iic-jku/SG13G2_ATBS-ADC/FPGA-Design/tbs_core/vivado/tbs_core_ethernet_board/tbs_core_ethernet_board.runs/synth_1/.vivado.begin.rst

<?xml version="1.0"?>
<ProcessHandle Version="1" Minor="0">
    <Process Command="vivado.bat" Owner="si150" Host="SIMIBOOK" Pid="4056" HostCore="16" HostMemory="016458313728">
    </Process>
</ProcessHandle>
