iic-jku/SG13G2_ATBS-ADC/FPGA-Design/tbs_core/vivado/tbs_core_pwm_board/tbs_core_pwm_board.runs/impl_1/.vivado.begin.rst

<?xml version="1.0"?>
<ProcessHandle Version="1" Minor="0">
    <Process Command="vivado.bat" Owner="si150" Host="SIMIBOOK" Pid="18940" HostCore="16" HostMemory="016458313728">
    </Process>
</ProcessHandle>
<?xml version="1.0"?>
<ProcessHandle Version="1" Minor="0">
    <Process Command="vivado.bat" Owner="si150" Host="SIMIBOOK" Pid="1672" HostCore="16" HostMemory="016458313728">
    </Process>
</ProcessHandle>
