iic-jku/SG13G2_ATBS-ADC/FPGA-Design/tbs_core/documentation/TBS/TBS_RTL.pdf

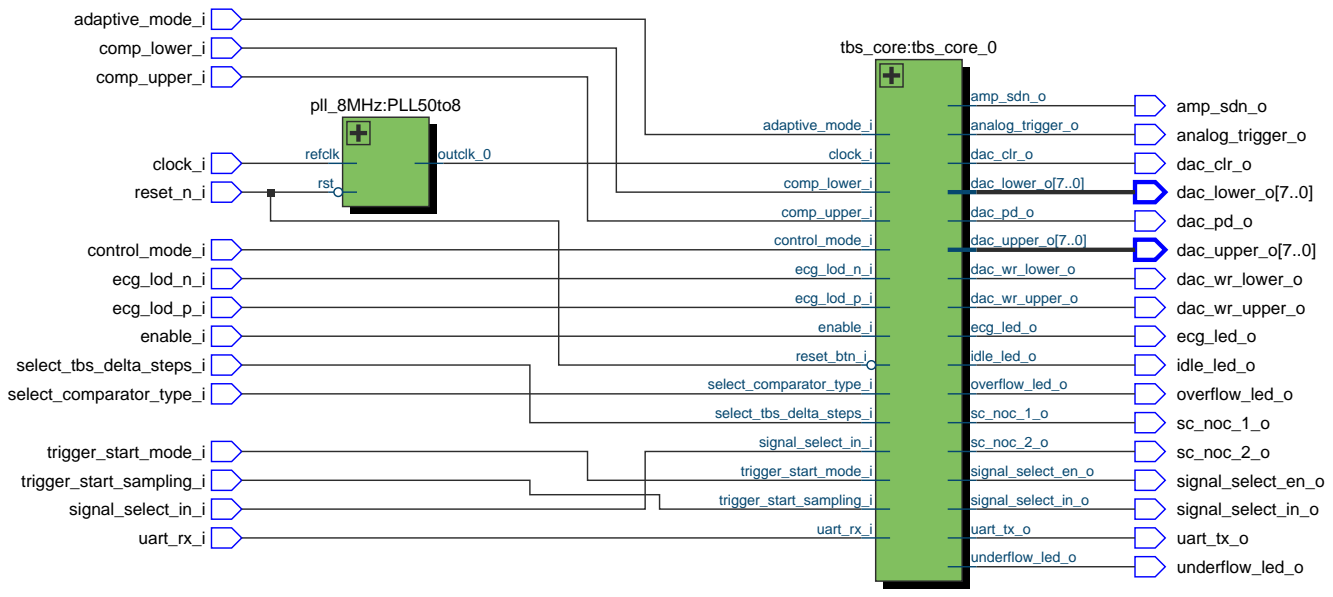
[picture p30: figure]
comp_upper_i; amp_sdn_o; comp_lower_i; analog_trigger_o; adaptive_mode_i; dac_clr_o; tbs_core:tbs_core_0; clock_i; control_mode_i; ecg_lod_n_i; ecg_lod_p_i; enable_i; reset_btn_i; select_comparator_type_i; select_tbs_delta_steps_i; signal_select_in_i; trigger_start_mode_i; trigger_start_sampling_i; uart_rx_i; dac_pd_o; dac_wr_lower_o; dac_wr_upper_o; ecg_led_o; idle_led_o; overflow_led_o; sc_noc_1_o; sc_noc_2_o; signal_select_en_o; signal_select_in_o; uart_tx_o; underflow_led_o; dac_upper_o[7..0]; dac_lower_o[7..0]; pll_8MHz:PLL50to8; refclk; rst; outclk_0; reset_n_i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
