iic-jku/SG13G2_ATBS-ADC/FPGA-Design/tbs_core/documentation/TBS_Ethernet/TBS_Ethernet_RTL.pdf

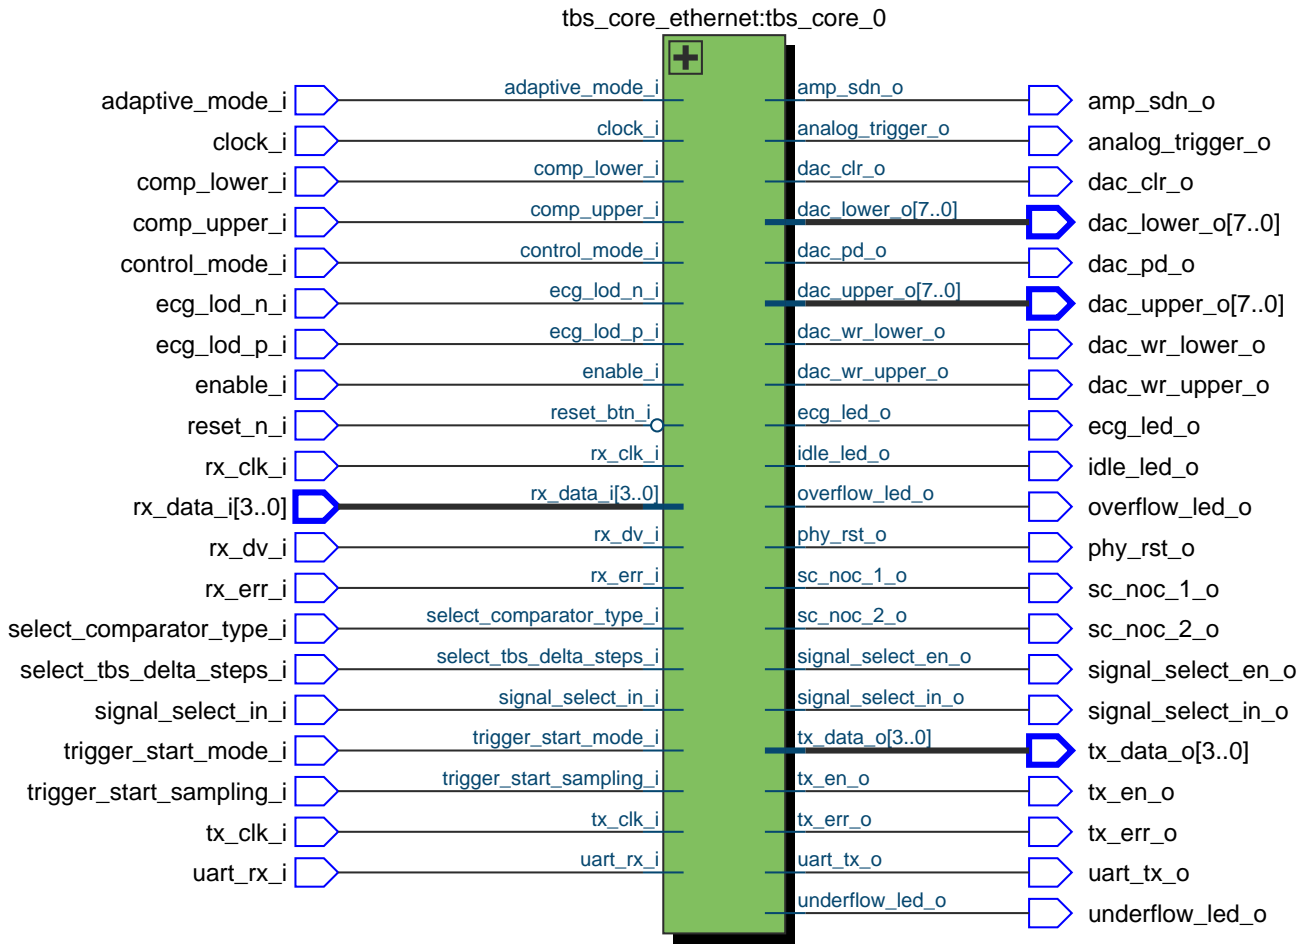
[picture p32: figure]
adaptive_mode_i; amp_sdn_o; clock_i; analog_trigger_o; comp_lower_i; dac_clr_o; comp_upper_i; dac_lower_o[7..0]; tbs_core_ethernet:tbs_core_0; control_mode_i; ecg_lod_n_i; ecg_lod_p_i; enable_i; reset_btn_i; rx_clk_i; rx_err_i; select_comparator_type_i; select_tbs_delta_steps_i; signal_select_in_i; trigger_start_mode_i; trigger_start_sampling_i; tx_clk_i; uart_rx_i; rx_data_i[3..0]; dac_pd_o; dac_wr_lower_o; dac_wr_upper_o; ecg_led_o; idle_led_o; overflow_led_o; phy_rst_o; sc_noc_1_o; sc_noc_2_o; signal_select_en_o; signal_select_in_o; tx_err_o; uart_tx_o; underflow_led_o; dac_upper_o[7..0]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
