iic-jku/SG13G2_ATBS-ADC/FPGA-Design/tbs_core/pwm_modulator/documentation/PWM-Modulator_RTL1.pdf

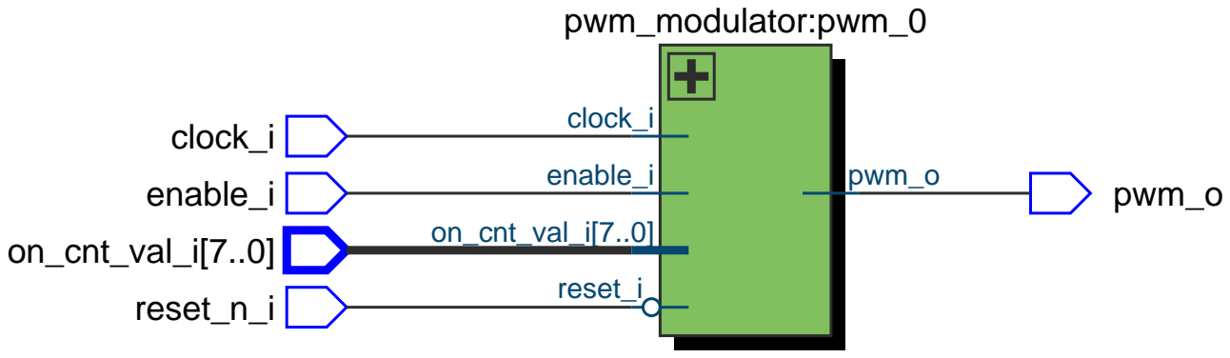
[picture p34: figure]
clock_i; pwm_modulator:pwm_0; enable_i; reset_i; on_cnt_val_i[7..0]; pwm_o enable_i; pwm_o; reset_n_i
