iic-jku/SG13G2_ATBS-ADC/FPGA-Design/tbs_core/pwm_modulator/documentation/PWM-Modulator_RTL2.pdf

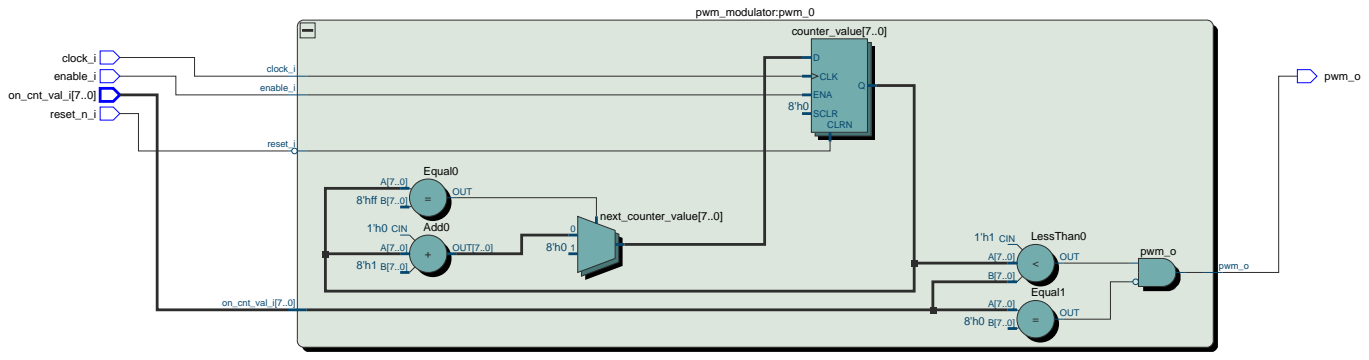
[picture p35: figure]
pwm_modulator:pwm_0; clock_i; enable_i; reset_i; on_cnt_val_i[7..0]; pwm_o; enable_i on_cnt_val_i[7..0] reset_n_i; 1'h0 CIN; Add0; OUT[7..0]; Equal0; 8'hff B[7..0]; OUT; Equal1; OUT <; 1'h1 CIN; LessThan0; counter_value[7..0] D; CLK; CLRN; ENA SCLR 8'h0; next_counter_value[7..0]
