iic-jku/SG13G2_ATBS-ADC/FPGA-Design/tbs_core/quartus/tbs_core_pwm_board/db/tbs_core_pwm_board.lpc.html

Hierarchy | Input | Constant Input | Unused Input | Floating Input | Output | Constant Output | Unused Output | Floating Output | Bidir | Constant Bidir | Unused Bidir | Input only Bidir | Output only Bidir
tbs_core_0|uart_0|uart_rx_0 | 12 | 0 | 0 | 0 | 9 | 0 | 0 | 0 | 0 | 0 | 0 | 0 | 0
tbs_core_0|uart_0|uart_tx_0 | 20 | 0 | 0 | 0 | 2 | 0 | 0 | 0 | 0 | 0 | 0 | 0 | 0
tbs_core_0|uart_0 | 21 | 0 | 0 | 0 | 11 | 0 | 0 | 0 | 0 | 0 | 0 | 0 | 0
tbs_core_0|memory2uart_0 | 24 | 0 | 0 | 0 | 9 | 0 | 0 | 0 | 0 | 0 | 0 | 0 | 0
tbs_core_0|spike_memory_0|\gen_dual_ram:dual_ram_0 | 58 | 41 | 0 | 41 | 40 | 41 | 41 | 41 | 0 | 0 | 0 | 0 | 0
tbs_core_0|spike_memory_0 | 25 | 0 | 0 | 0 | 23 | 0 | 0 | 0 | 0 | 0 | 0 | 0 | 0
tbs_core_0|spike_encoder_0 | 24 | 0 | 0 | 0 | 21 | 0 | 0 | 0 | 0 | 0 | 0 | 0 | 0
tbs_core_0|time_measurement_0 | 2 | 0 | 0 | 0 | 20 | 0 | 0 | 0 | 0 | 0 | 0 | 0 | 0
tbs_core_0|sc_noc_generator_0 | 36 | 0 | 0 | 0 | 2 | 0 | 0 | 0 | 0 | 0 | 0 | 0 | 0
tbs_core_0|analog_trigger_0 | 19 | 0 | 0 | 0 | 1 | 0 | 0 | 0 | 0 | 0 | 0 | 0 | 0
tbs_core_0|pwm_1 | 11 | 0 | 0 | 0 | 1 | 0 | 0 | 0 | 0 | 0 | 0 | 0 | 0
tbs_core_0|dac_control_1|sync_chain_0 | 3 | 0 | 0 | 0 | 1 | 0 | 0 | 0 | 0 | 0 | 0 | 0 | 0
tbs_core_0|dac_control_1 | 16 | 0 | 2 | 0 | 20 | 0 | 0 | 0 | 0 | 0 | 0 | 0 | 0
tbs_core_0|pwm_0 | 11 | 0 | 0 | 0 | 1 | 0 | 0 | 0 | 0 | 0 | 0 | 0 | 0
tbs_core_0|dac_control_0|sync_chain_0 | 3 | 0 | 0 | 0 | 1 | 0 | 0 | 0 | 0 | 0 | 0 | 0 | 0
tbs_core_0|dac_control_0 | 16 | 0 | 0 | 0 | 20 | 0 | 0 | 0 | 0 | 0 | 0 | 0 | 0
tbs_core_0|adaptive_ctrl_0|weyls_discrepancy_0|priority_encoder_1 | 5 | 1 | 2 | 1 | 3 | 1 | 1 | 1 | 0 | 0 | 0 | 0 | 0
tbs_core_0|adaptive_ctrl_0|weyls_discrepancy_0|priority_encoder_0 | 5 | 1 | 2 | 1 | 3 | 1 | 1 | 1 | 0 | 0 | 0 | 0 | 0
tbs_core_0|adaptive_ctrl_0|weyls_discrepancy_0|\gen_spike_2_tc:14:spike_2_tc | 8 | 0 | 0 | 0 | 6 | 0 | 0 | 0 | 0 | 0 | 0 | 0 | 0
tbs_core_0|adaptive_ctrl_0|weyls_discrepancy_0|\gen_spike_2_tc:13:spike_2_tc | 8 | 0 | 0 | 0 | 6 | 0 | 0 | 0 | 0 | 0 | 0 | 0 | 0
tbs_core_0|adaptive_ctrl_0|weyls_discrepancy_0|\gen_spike_2_tc:12:spike_2_tc | 8 | 0 | 0 | 0 | 6 | 0 | 0 | 0 | 0 | 0 | 0 | 0 | 0
tbs_core_0|adaptive_ctrl_0|weyls_discrepancy_0|\gen_spike_2_tc:11:spike_2_tc | 8 | 0 | 0 | 0 | 6 | 0 | 0 | 0 | 0 | 0 | 0 | 0 | 0
tbs_core_0|adaptive_ctrl_0|weyls_discrepancy_0|\gen_spike_2_tc:10:spike_2_tc | 8 | 0 | 0 | 0 | 6 | 0 | 0 | 0 | 0 | 0 | 0 | 0 | 0
tbs_core_0|adaptive_ctrl_0|weyls_discrepancy_0|\gen_spike_2_tc:9:spike_2_tc | 8 | 0 | 0 | 0 | 6 | 0 | 0 | 0 | 0 | 0 | 0 | 0 | 0
tbs_core_0|adaptive_ctrl_0|weyls_discrepancy_0|\gen_spike_2_tc:8:spike_2_tc | 8 | 0 | 0 | 0 | 6 | 0 | 0 | 0 | 0 | 0 | 0 | 0 | 0
tbs_core_0|adaptive_ctrl_0|weyls_discrepancy_0|\gen_spike_2_tc:7:spike_2_tc | 8 | 0 | 0 | 0 | 6 | 0 | 0 | 0 | 0 | 0 | 0 | 0 | 0
tbs_core_0|adaptive_ctrl_0|weyls_discrepancy_0|\gen_spike_2_tc:6:spike_2_tc | 8 | 0 | 0 | 0 | 6 | 0 | 0 | 0 | 0 | 0 | 0 | 0 | 0
tbs_core_0|adaptive_ctrl_0|weyls_discrepancy_0|\gen_spike_2_tc:5:spike_2_tc | 8 | 0 | 0 | 0 | 6 | 0 | 0 | 0 | 0 | 0 | 0 | 0 | 0
tbs_core_0|adaptive_ctrl_0|weyls_discrepancy_0|\gen_spike_2_tc:4:spike_2_tc | 8 | 0 | 0 | 0 | 6 | 0 | 0 | 0 | 0 | 0 | 0 | 0 | 0
tbs_core_0|adaptive_ctrl_0|weyls_discrepancy_0|\gen_spike_2_tc:3:spike_2_tc | 8 | 0 | 0 | 0 | 6 | 0 | 0 | 0 | 0 | 0 | 0 | 0 | 0
tbs_core_0|adaptive_ctrl_0|weyls_discrepancy_0|\gen_spike_2_tc:2:spike_2_tc | 8 | 0 | 0 | 0 | 6 | 0 | 0 | 0 | 0 | 0 | 0 | 0 | 0
tbs_core_0|adaptive_ctrl_0|weyls_discrepancy_0|\gen_spike_2_tc:1:spike_2_tc | 8 | 0 | 0 | 0 | 6 | 0 | 0 | 0 | 0 | 0 | 0 | 0 | 0
tbs_core_0|adaptive_ctrl_0|weyls_discrepancy_0|\gen_spike_2_tc:0:spike_2_tc | 8 | 6 | 0 | 6 | 6 | 6 | 6 | 6 | 0 | 0 | 0 | 0 | 0
tbs_core_0|adaptive_ctrl_0|weyls_discrepancy_0 | 33 | 0 | 0 | 0 | 4 | 0 | 0 | 0 | 0 | 0 | 0 | 0 | 0
tbs_core_0|adaptive_ctrl_0|spike_shift_reg_0 | 44 | 0 | 0 | 0 | 31 | 0 | 0 | 0 | 0 | 0 | 0 | 0 | 0
tbs_core_0|adaptive_ctrl_0 | 59 | 6 | 0 | 6 | 23 | 6 | 6 | 6 | 0 | 0 | 0 | 0 | 0
tbs_core_0|spike_detector_0 | 12 | 0 | 0 | 0 | 2 | 0 | 0 | 0 | 0 | 0 | 0 | 0 | 0
tbs_core_0|sync_chain_1 | 4 | 0 | 0 | 0 | 2 | 0 | 0 | 0 | 0 | 0 | 0 | 0 | 0
tbs_core_0|debouncer_6|sync_chain_0 | 3 | 0 | 0 | 0 | 1 | 0 | 0 | 0 | 0 | 0 | 0 | 0 | 0
tbs_core_0|debouncer_6 | 3 | 0 | 0 | 0 | 1 | 0 | 0 | 0 | 0 | 0 | 0 | 0 | 0
tbs_core_0|debouncer_5|sync_chain_0 | 3 | 0 | 0 | 0 | 1 | 0 | 0 | 0 | 0 | 0 | 0 | 0 | 0
tbs_core_0|debouncer_5 | 3 | 0 | 0 | 0 | 1 | 0 | 0 | 0 | 0 | 0 | 0 | 0 | 0
tbs_core_0|debouncer_4|sync_chain_0 | 3 | 0 | 0 | 0 | 1 | 0 | 0 | 0 | 0 | 0 | 0 | 0 | 0
tbs_core_0|debouncer_4 | 3 | 0 | 0 | 0 | 1 | 0 | 0 | 0 | 0 | 0 | 0 | 0 | 0
tbs_core_0|debouncer_3|sync_chain_0 | 3 | 0 | 0 | 0 | 1 | 0 | 0 | 0 | 0 | 0 | 0 | 0 | 0
tbs_core_0|debouncer_3 | 3 | 0 | 0 | 0 | 1 | 0 | 0 | 0 | 0 | 0 | 0 | 0 | 0
tbs_core_0|debouncer_2|sync_chain_0 | 3 | 0 | 0 | 0 | 1 | 0 | 0 | 0 | 0 | 0 | 0 | 0 | 0
tbs_core_0|debouncer_2 | 3 | 0 | 0 | 0 | 1 | 0 | 0 | 0 | 0 | 0 | 0 | 0 | 0
tbs_core_0|debouncer_1|sync_chain_0 | 3 | 0 | 0 | 0 | 1 | 0 | 0 | 0 | 0 | 0 | 0 | 0 | 0
tbs_core_0|debouncer_1 | 3 | 0 | 0 | 0 | 1 | 0 | 0 | 0 | 0 | 0 | 0 | 0 | 0
tbs_core_0|debouncer_0|sync_chain_0 | 3 | 0 | 0 | 0 | 1 | 0 | 0 | 0 | 0 | 0 | 0 | 0 | 0
tbs_core_0|debouncer_0 | 3 | 0 | 0 | 0 | 1 | 0 | 0 | 0 | 0 | 0 | 0 | 0 | 0
tbs_core_0|sync_chain_2 | 3 | 0 | 0 | 0 | 1 | 0 | 0 | 0 | 0 | 0 | 0 | 0 | 0
tbs_core_0|sync_chain_0 | 3 | 1 | 0 | 1 | 1 | 1 | 1 | 1 | 0 | 0 | 0 | 0 | 0
tbs_core_0 | 15 | 0 | 0 | 0 | 33 | 0 | 0 | 0 | 0 | 0 | 0 | 0 | 0
PLL50to8|pll_8mhz_inst | 2 | 0 | 0 | 0 | 2 | 0 | 0 | 0 | 0 | 0 | 0 | 0 | 0
PLL50to8 | 2 | 1 | 0 | 1 | 2 | 1 | 1 | 1 | 0 | 0 | 0 | 0 | 0
