iic-jku/SG13G2_ATBS-ADC/FPGA-Design/tbs_core/ethernet/documentation/Ethernet_RTL1.pdf

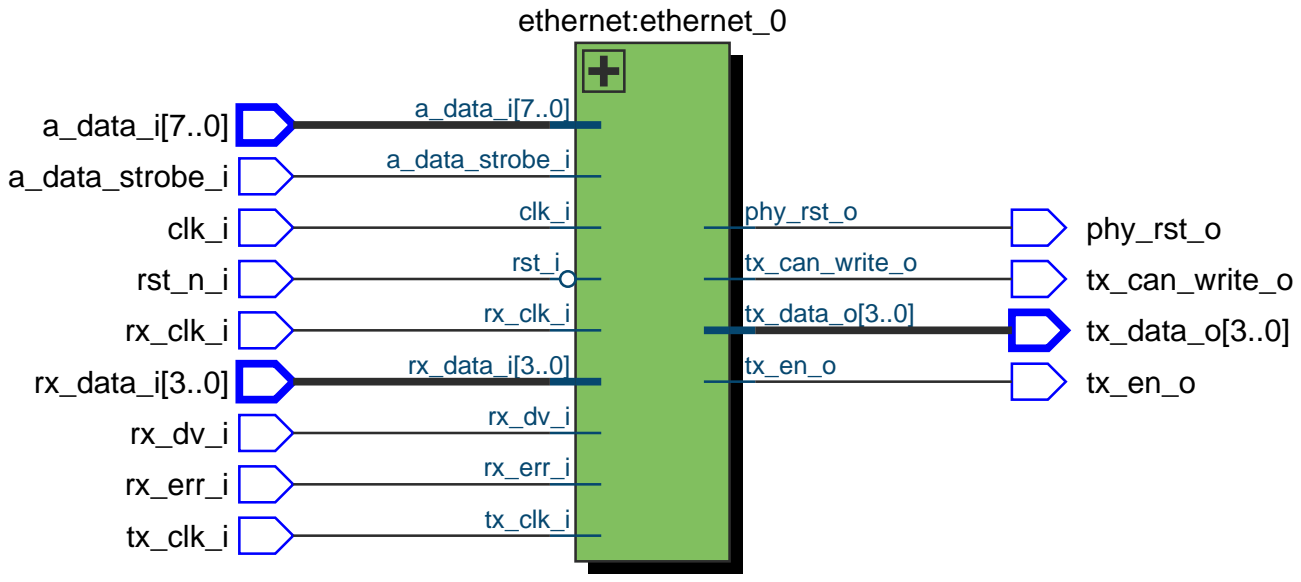
[picture p43: figure]
a_data_i[7..0] a_data_strobe_i; ethernet:ethernet_0; a_data_strobe_i; clk_i; rst_i; rx_clk_i; rx_err_i; tx_clk_i; a_data_i[7..0]; rx_data_i[3..0]; phy_rst_o; tx_can_write_o; tx_data_o[3..0]; rst_n_i; rx_clk_i rx_data_i[3..0]; rx_err_i tx_clk_i
