iic-jku/SG13G2_ATBS-ADC/FPGA-Design/tbs_core/ethernet/documentation/Ethernet_RTL2.pdf

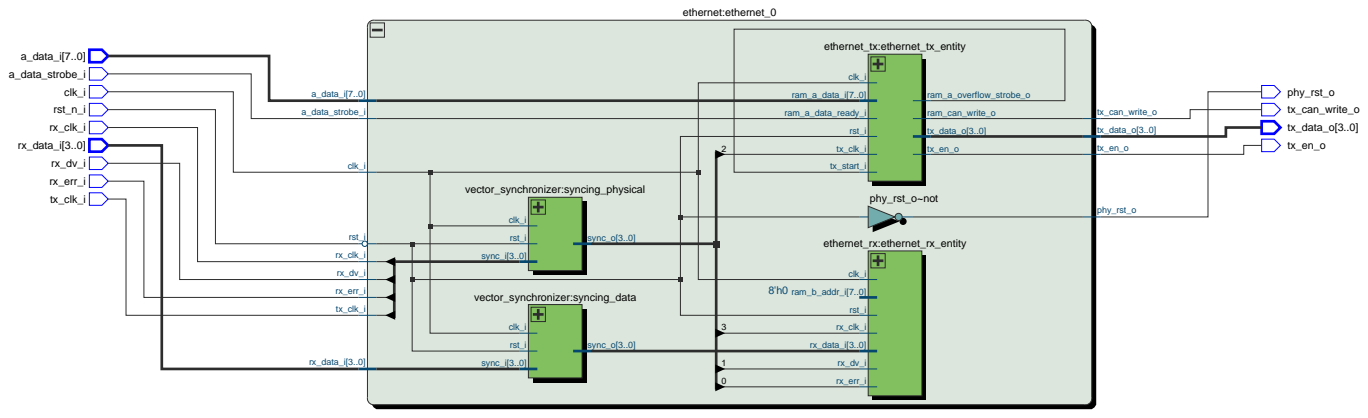
[picture p44: figure]
ethernet:ethernet_0; a_data_strobe_i; clk_i; rst_i; rx_clk_i; rx_err_i; tx_clk_i; a_data_i[7..0]; rx_data_i[3..0]; phy_rst_o; tx_can_write_o; tx_data_o[3..0]; a_data_strobe_i clk_i; ethernet_rx:ethernet_rx_entity; 8'h0 ram_b_addr_i[7..0]; ethernet_tx:ethernet_tx_entity; ram_a_data_ready_i; tx_start_i; ram_a_data_i[7..0]; ram_a_overflow_strobe_o; ram_can_write_o; phy_rst_o~not; vector_synchronizer:syncing_data; sync_i[3..0]; sync_o[3..0]; vector_synchronizer:syncing_physical; rst_n_i rx_clk_i rx_data_i[3..0] rx_dv_i rx_err_i
