iic-jku/SG13G2_ATBS-ADC/FPGA-Design/tbs_core/adaptive_threshold_control/Spike-Buffering/documentation/Spike-Buffering_RTL1.pdf

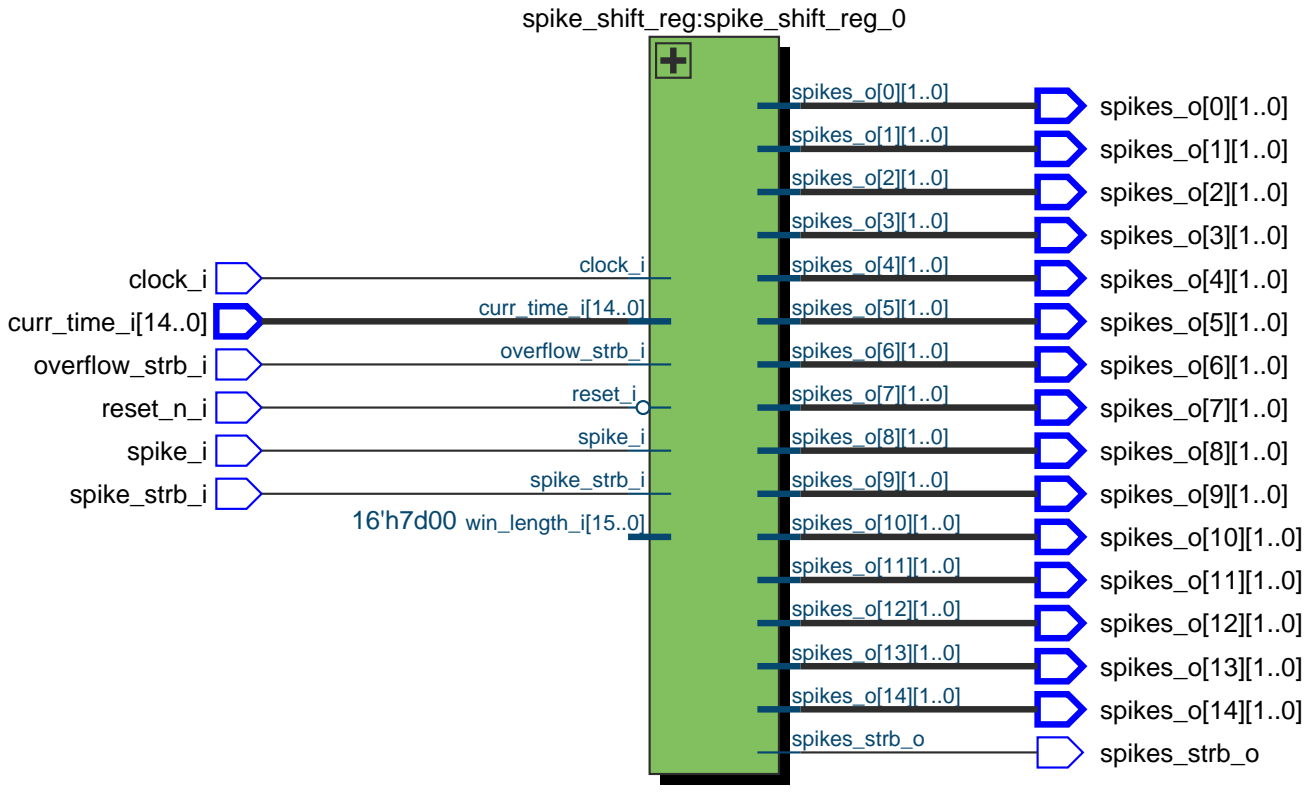
[picture p45: figure]
spikes_o[0][1..0] spikes_o[1][1..0] spikes_o[2][1..0]; spike_shift_reg:spike_shift_reg_0; clock_i; overflow_strb_i; reset_i; spike_i; spike_strb_i; curr_time_i[14..0]; 16'h7d00 win_length_i[15..0]; spikes_strb_o; spikes_o[0][1..0]; spikes_o[1][1..0]; spikes_o[2][1..0]; spikes_o[3][1..0]; spikes_o[4][1..0]; spikes_o[5][1..0]; spikes_o[6][1..0]; spikes_o[7][1..0]; spikes_o[8][1..0]; spikes_o[9][1..0]; spikes_o[10][1..0]; spikes_o[11][1..0]; spikes_o[12][1..0]; spikes_o[13][1..0]; spikes_o[14][1..0]; reset_n_i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
