iic-jku/SG13G2_ATBS-ADC/FPGA-Design/documents/s7-Mini/AP-TE0890-01/TE0890-01/Layerstack/Layerstack.JPG

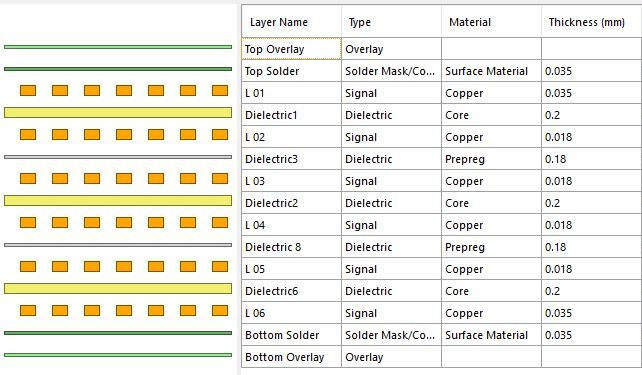
FPGA-Design/documents/s7-Mini/AP-TE0890-01/TE0890-01/Layerstack/Layerstack.JPG
