iic-jku/SG13G2_ATBS-ADC/FPGA-Design/tbs_core/documentation/Main_FSM.jpg

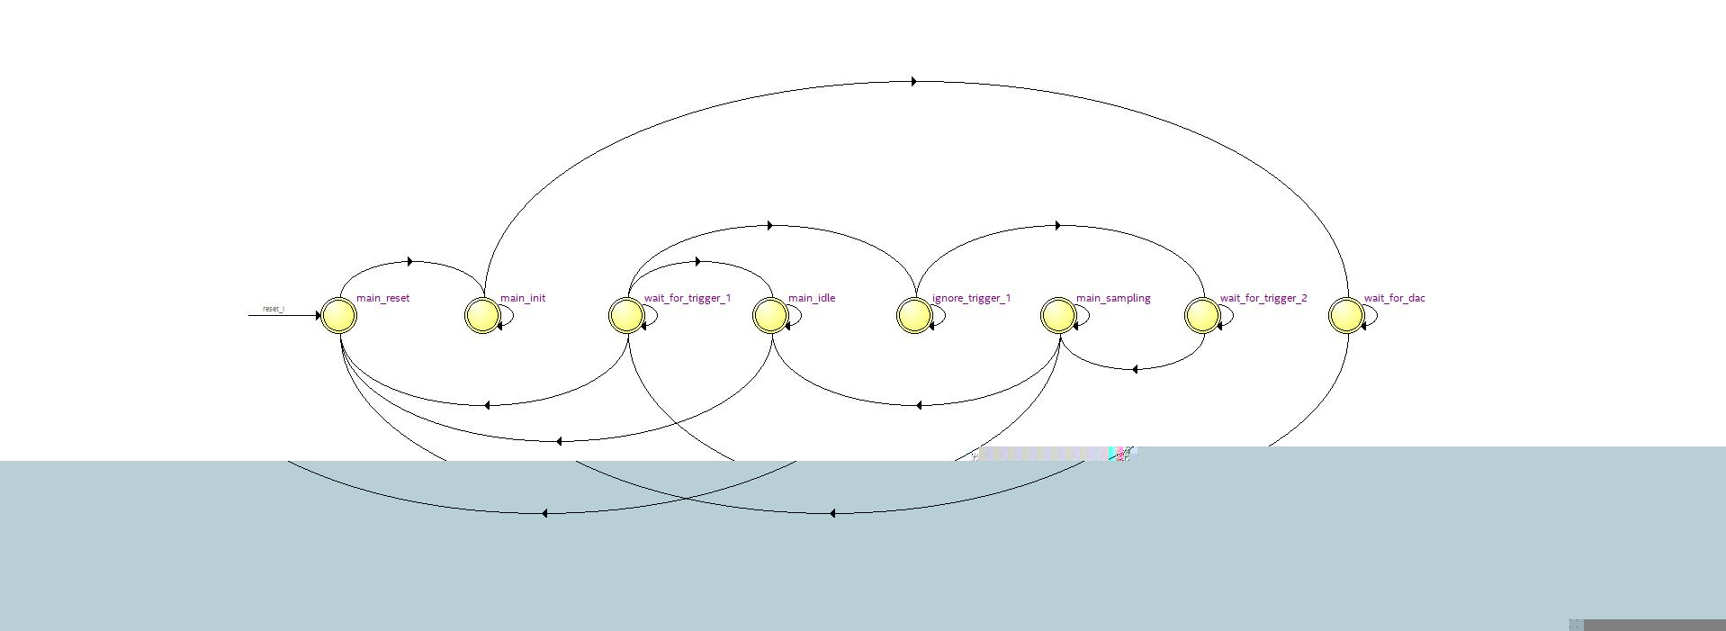
FPGA-Design/tbs_core/documentation/Main_FSM.jpg
