iic-jku/SG13G2_ATBS-ADC/PCB-Design/Ethernet_Breakout-Board/Ethernet_Breakout-Board_Pics/Ethernet_Breakout-Board_Drills_2D.png

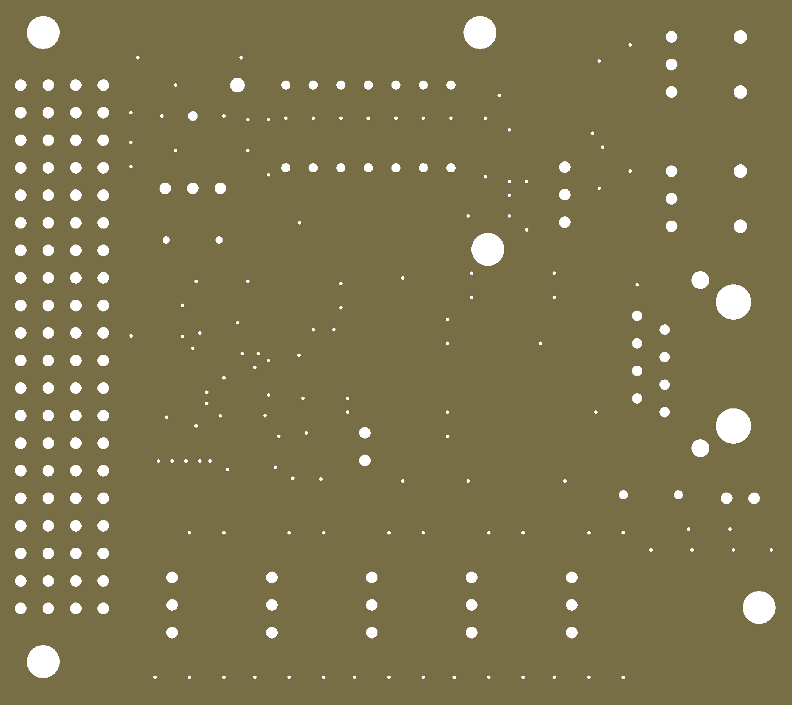
PCB-Design/Ethernet_Breakout-Board/Ethernet_Breakout-Board_Pics/Ethernet_Breakout-Board_Drills_2D.png
