iic-jku/SG13G2_ATBS-ADC/PCB-Design/Ethernet_Breakout-Board/Ethernet_Breakout-Board_Pics/Ethernet_Breakout-Board_Top_3D.png

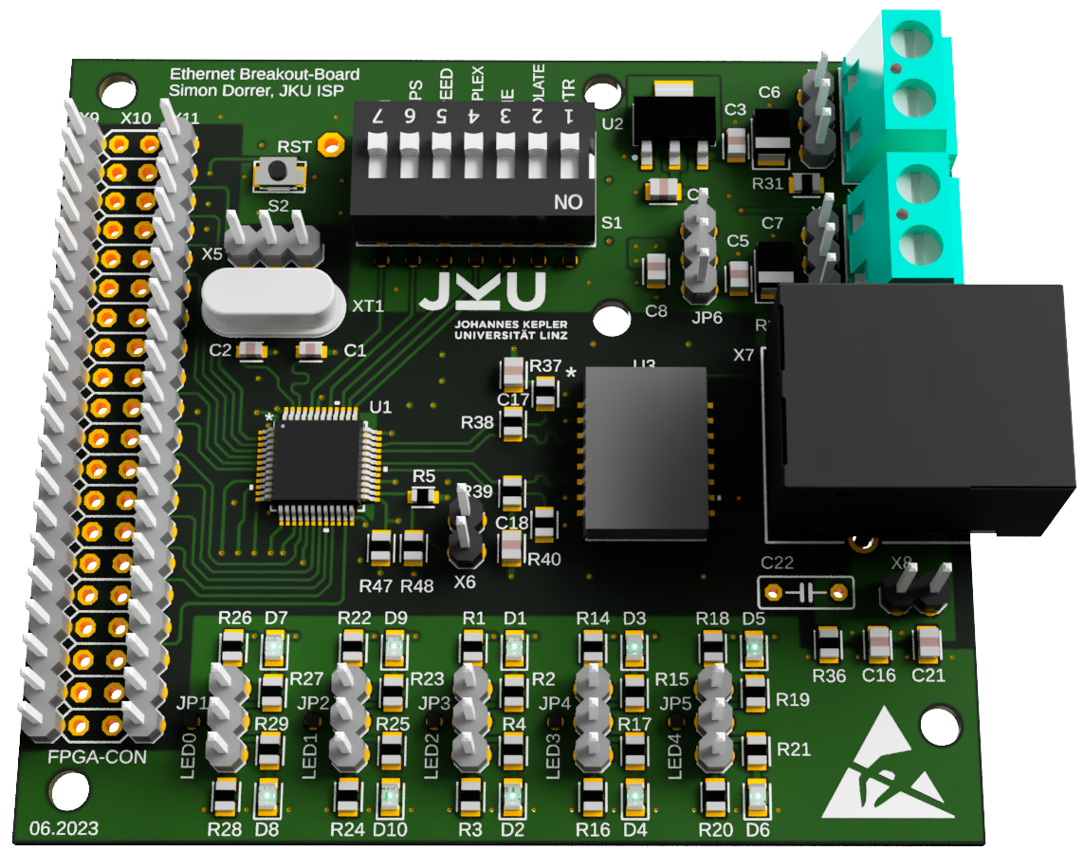
PCB-Design/Ethernet_Breakout-Board/Ethernet_Breakout-Board_Pics/Ethernet_Breakout-Board_Top_3D.png
