iic-jku/SG13G2_ATBS-ADC/PCB-Design/Ethernet_Breakout-Board/Ethernet_Breakout-Board_Stackup.png

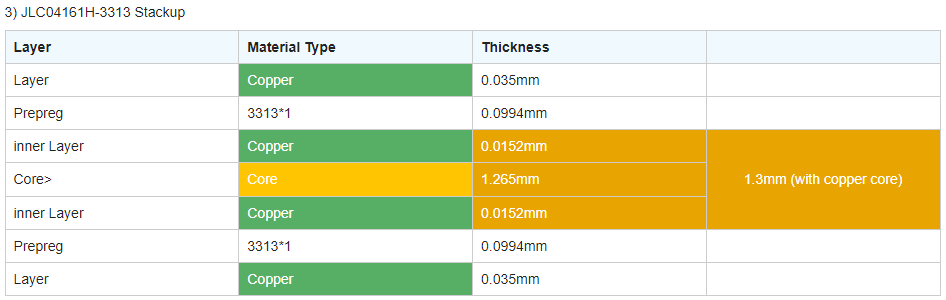
PCB-Design/Ethernet_Breakout-Board/Ethernet_Breakout-Board_Stackup.png
