iic-jku/SG13G2_ATBS-ADC/PCB-Design/Ethernet_Breakout-Board/Impedance-Calculator.png

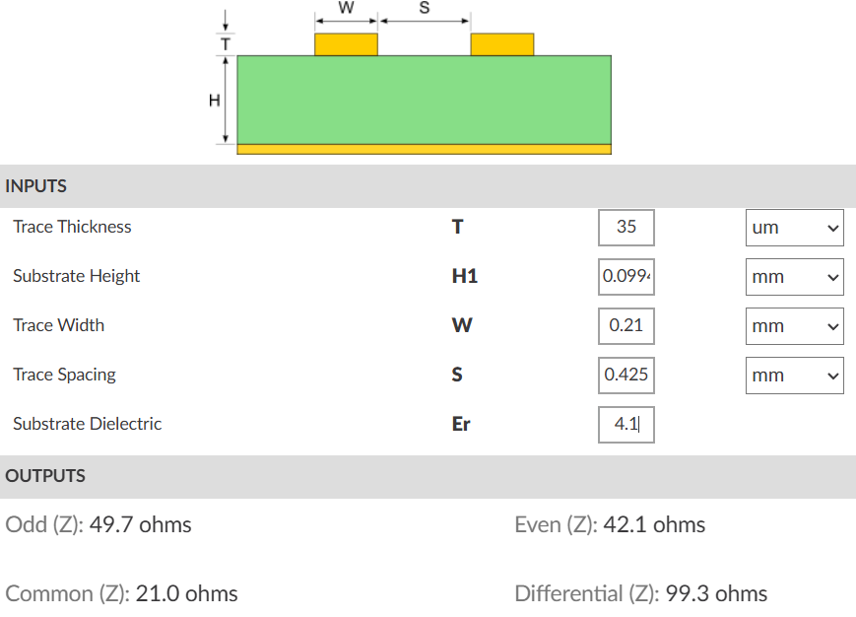
PCB-Design/Ethernet_Breakout-Board/Impedance-Calculator.png
