iic-jku/SG13G2_ATBS-ADC/PCB-Design/s7-Mini-FPGA Development Board/s7-Mini-FPGA-Development-Board_Pics/s7-Mini-FPGA Development Board_3D_Top_original.JPG

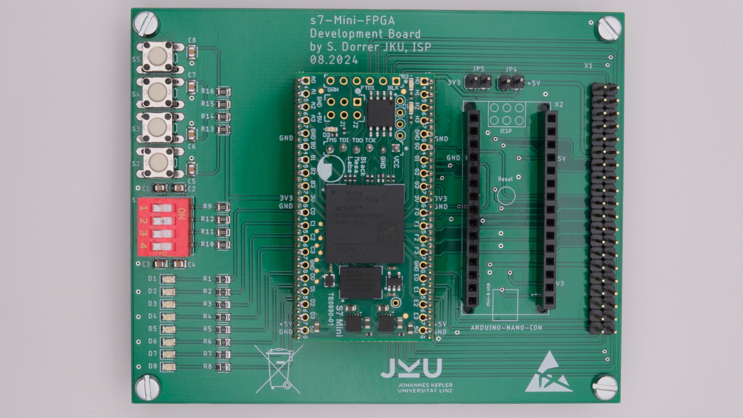
PCB-Design/s7-Mini-FPGA Development Board/s7-Mini-FPGA-Development-Board_Pics/s7-Mini-FPGA Development Board_3D_Top_original.JPG
