iic-jku/SG13G2_ATBS-ADC/PCB-Design/TBS_Analog_Front-End/TBS_Analog_Front-End_Pics/TBS_Analog_Front-End_TOP_2D.png

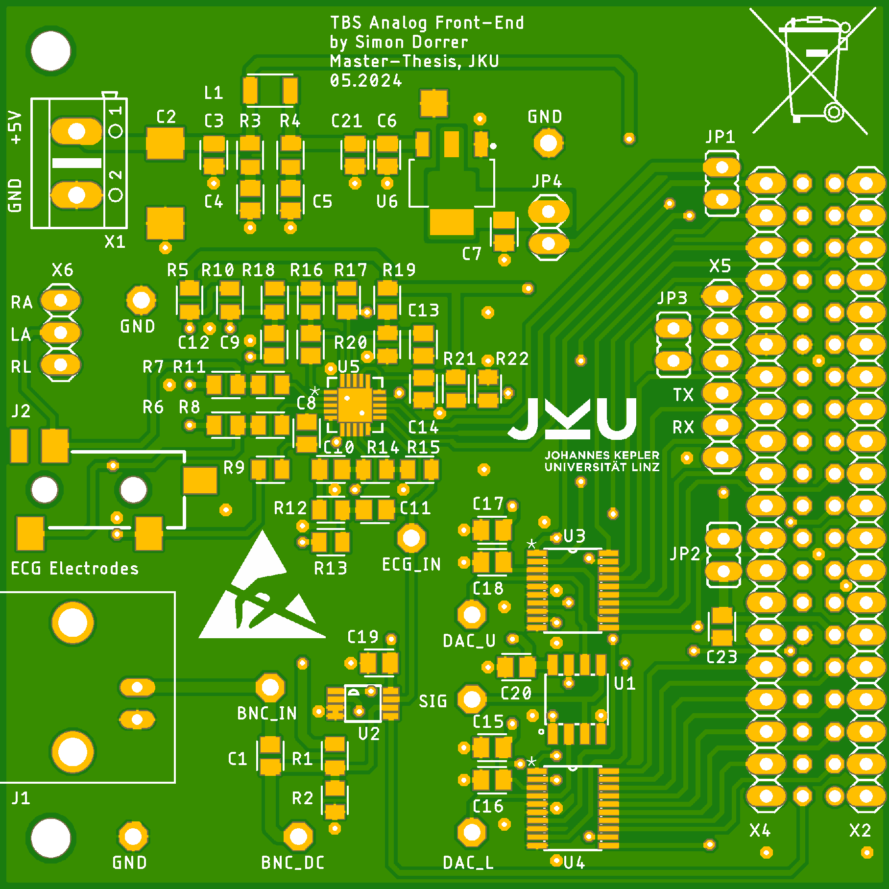
PCB-Design/TBS_Analog_Front-End/TBS_Analog_Front-End_Pics/TBS_Analog_Front-End_TOP_2D.png
