iic-jku/SG13G2_ATBS-ADC/PCB-Design/TBS_Analog_Front-End/TBS_Analog_Front-End_Assembly/TBS_Analog_Front-End_BOM.txt

Partlist exported from C:/Users/si150/AppData/Local/Temp/Neutron/ElectronFileOutput/6176/sch-4c9b82f6-f091-47ea-af62-c991dffd48f1/TBS-Analog_Front-End v54.sch at 24.10.2024 12:45

Qty Value            Device                          Package              Parts                                                   Description                                     CATEGORY  COPYRIGHT                                                CURRENT_RATING DESCRIPTION                  MANUFACTURER       MANUFACTURER_PART_NUMBER MF MFR_NAME           MPN     OC_FARNELL OC_NEWARK OPERATING_TEMP OPERATING_TEMPERATURE PART_STATUS PITCH           POPULARITY PROD_ID    RATING ROHS_COMPLIANCE ROHS_COMPLIANT SERIES  SF_ID     SPICEPREFIX SUB-CATEGORY       THERMALLOSS TOLERANCE TP_SIGNAL_NAME TYPE                                                        VOLTAGE_RATING
1                    L_CHIP-1206(3216-METRIC)        INDC3216X190         L1                                                      Inductor Fixed - Generic                        Inductor                                                                                                                                                                                                                                                                                                                                                                 Fixed                                                                                                                             
4   0R               R_CHIP-0805(2012-METRIC)        RESC2012X65          R5, R22, R25, R26                                       Resistor Fixed - Generic                        Resistor                                                                                                                                                                                                                                                                                                                                                                 Fixed                                                                                                                             
2   1.5nF            C_CHIP-0805(2012-METRIC)        CAPC2012X110         C10, C11                                                Capacitor - Generic                             Capacitor                                                                                                                                                                                                                                                                                                                                                                                                                                                                                                  
3   100k             R_CHIP-0805(2012-METRIC)        RESC2012X65          R1, R2, R14                                             Resistor Fixed - Generic                        Resistor                                                                                                                                                                                                                                                                                                                                                                 Fixed                                                                                                                             
12  100nF            C_CHIP-0805(2012-METRIC)        CAPC2012X110         C3, C6, C7, C13, C14, C16, C18, C19, C20, C22, C23, C24 Capacitor - Generic                             Capacitor                                                                                                                                                                                                                                                                                                                                                                                                                                                                                                  
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
2   AD5331BRUZ       AD5331BRUZ_FUNCAD5331BRUZ       AD5331BRUZ           U3, U4                                                                                                            Copyright (C) 2024 Ultra Librarian. All rights reserved.                                                                AD5331BRUZ                  Analog Devices Inc                                                                                                                                                                                                                                                                                                                           
1   AD8232ACPZ-RL    AD8232ACPZ-RL_FUNCAD8232ACPZ-RL AD8232ACPZ-RL        U5                                                                                                                Copyright (C) 2024 Ultra Librarian. All rights reserved.                                                                AD8232ACPZ-RL               Analog Devices Inc                                                                                                                                                                                                                                                                                                                           
1   AUDIO_JACK_3.5MM AUDIO_JACK_3.5MM_SMD            AUDIO-JACK-3.5MM-SMD J2                                                      Audio Jack                                                                                                                                                                                                                                                                                                                                CONN-10353                                                                                                                                                                                                       
4   DNP              R_CHIP-0805(2012-METRIC)        RESC2012X65          R10, R21, R23, R24                                      Resistor Fixed - Generic                        Resistor                                                                                                                                                                                                                                                                                                                                                                 Fixed                                                                                                                             
1   ECG              PINHD-1X3                       1X03                 X6                                                      PIN HEADER                                      Headers                                                                           Header, Straight, 3 Position Generic                                                           Generic                                     Generic               Active      0.100" (2.54mm)                              Generic                        Generic                       Headers, Male Pins                                      Board to Board or Cable, Unshrouded, Through Hole, Straight               
1   FPGA-CON         CON40                           CON40                X3                                                      CONNECTOR                                                                                                                                                                                                                                unknown    unknown                                                                    0                                                                                                                                                                                                                           
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
1   Meas_I           PINHD-1X2                       1X02                 JP4                                                     PIN HEADER                                      Headers                                                                           Header, Straight, 2 Position Generic                                                           Generic                                     Generic               Active      0.100" (2.54mm)                              Generic                        Generic                       Headers, Male Pins                                      Board to Board or Cable, Unshrouded, Through Hole, Straight               
1   SIGNAL           BNCPTH                          BNC                  J1                                                      BNC Right Angle Connector                                                                                                                                                                                                                                                                                                                 LPA-12729                                                PRT-10550                                                                                                                                               
9   TPPAD1-13        TPPAD1-13                       P1-13                TP1, TP2, TP3, TP4, TP5, TP6, TP7, TP8, TP9             Test pad                                                                                                                                                                                                                                                                                                                       12                                                                                                                                                                                                                          
1   TPTP20SQ         TPTP20SQ                        TP20SQ               TP10                                                    Test pad                                                                                                                                                                                                                                                                                                                       2                                                                                                                                                                                                                           
1   TSX3702IDT       TSX3702IDT                      SOIC127P600X175-8N   U1                                                                                                                                                                                                                                                                                                                                                                                                                                                                                                                                                                                                                 
1   UART             PINHD-1X6                       1X06                 X5                                                      PIN HEADER                                                                                                                                                                                                                                                                                                                     79                                                                                                                                                                                                                          
1   UART_+5V         JP1Q                            JP1                  JP3                                                     JUMPER                                                                                                                                                                                                                                                                                                                         15
