iic-jku/SG13G2_ATBS-ADC/Reconstruction/figures/testing.csv

t_recon | spikes | recon
0.03277825 | -0.25 | 1.65
0.102960875 | 0.25 | 1.753125
0.119981 | -0.25 | 1.65
0.13436775 | 0.25 | 1.753125
0.16749825 | -0.25 | 1.65
0.357068625 | 0.25 | 1.753125
0.39067525 | -0.25 | 1.65
0.394087125 | -0.25 | 1.546875
0.415457625 | 0.25 | 1.65
0.46584325 | -0.25 | 1.546875
0.494399125 | 0.25 | 1.65
0.517446625 | -0.25 | 1.546875
0.53319625 | 0.25 | 1.65
0.5355055 | 0.25 | 1.753125
0.53728 | 0.25 | 1.85625
0.538538625 | 0.25 | 1.959375
0.539564125 | 0.25 | 2.0625
0.540489375 | 0.25 | 2.165625
0.541362 | 0.25 | 2.26875
0.54218925 | 0.25 | 2.371875
0.54303525 | 0.25 | 2.475
0.5438415 | 0.25 | 2.578125
0.5446145 | 0.25 | 2.68125
0.54535475 | 0.25 | 2.784375
0.54608 | 0.25 | 2.8875
0.546811 | 0.25 | 2.990625
0.5475575 | 0.25 | 3.09375
0.548413625 | 0.25 | 3.196875
0.5639985 | -0.25 | 3.09375
0.565222125 | -0.25 | 2.990625
0.56587975 | -0.25 | 2.8875
0.56638925 | -0.25 | 2.784375
0.56683125 | -0.25 | 2.68125
0.56723425 | -0.25 | 2.578125
0.567605125 | -0.25 | 2.475
0.567976875 | -0.25 | 2.371875
0.56831 | -0.25 | 2.26875
0.568648 | -0.25 | 2.165625
0.5689835 | -0.25 | 2.0625
0.56931425 | -0.25 | 1.959375
0.569651875 | -0.25 | 1.85625
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
