iic-jku/SG13G2_ATBS-ADC/PCB-Design/ATBS_Evaluation-Board/ATBS_Evaluation-Board_Pics/ATBS_Evaluation-Board_2D_Top.png

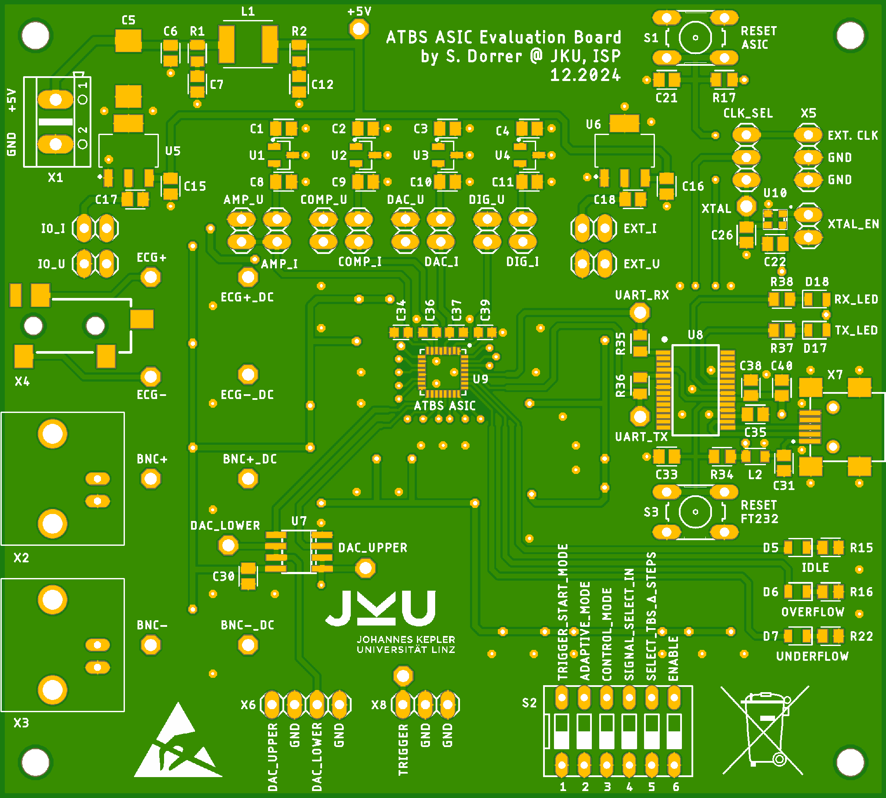
PCB-Design/ATBS_Evaluation-Board/ATBS_Evaluation-Board_Pics/ATBS_Evaluation-Board_2D_Top.png
