iic-jku/SG13G2_ATBS-ADC/PCB-Design/TBS_Analog_Front-End/TBS_Analog_Front-End_LTspice/AD8232.pdf

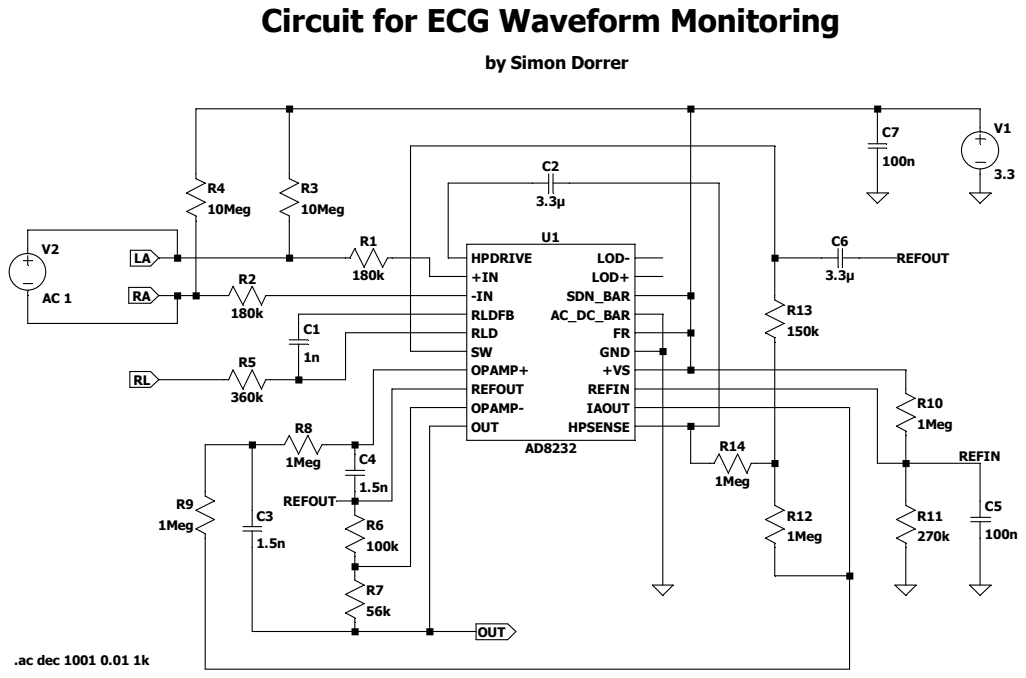
[picture p113: page 1]

Circuit for ECG Waveform Monitoring
