iic-jku/SG13G2_ATBS-ADC/SG13G2_ATBS-ADC-main/python/reconstruction/figures/ATBS_PoC_8Bit_4ms_Sine_Reconstruction.pdf

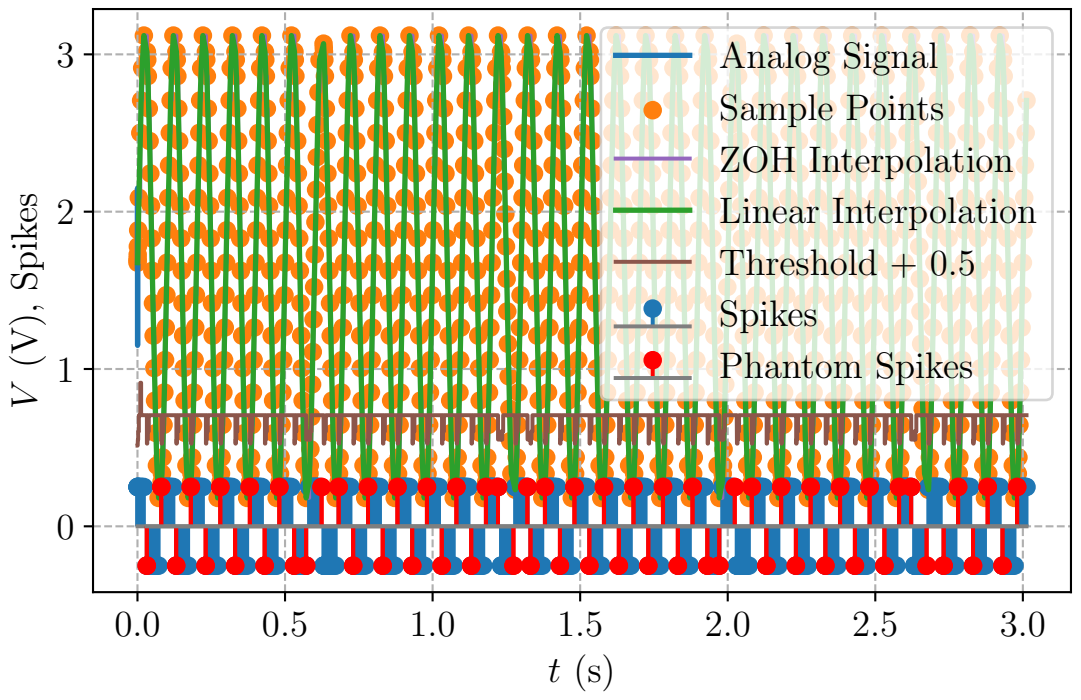
[picture p114: page 1]
V (V), Spikes; Linear Interpolation; Spikes; Phantom

Analog Signal
Sample Points ZOH Interpolation

Threshold | + 0.5
