iic-jku/SG13G2_ATBS-ADC/SG13G2_ATBS-ADC-main/python/reconstruction/figures/TBS_PoC_5Bit_virtual_ECG_Reconstruction.pdf

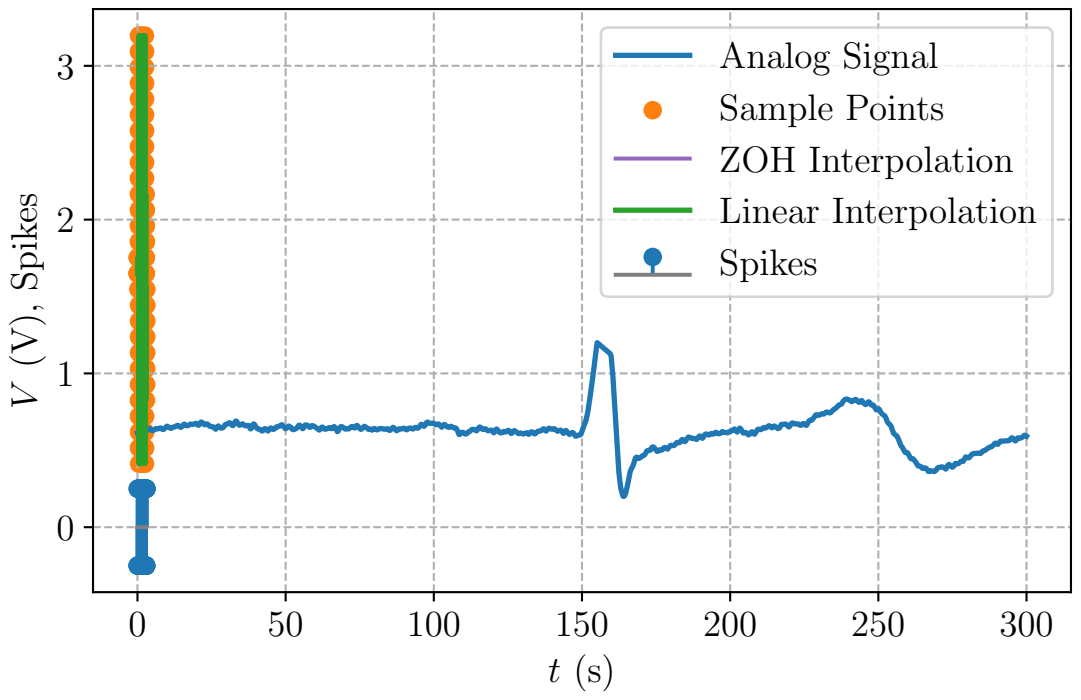
[picture p115: page 1]
V (V), Spikes; Spikes

Analog Signal
Sample Points ZOH Interpolation Linear Interpolation
