iic-jku/SG13G2_ATBS-ADC/SG13G2_ATBS-ADC-main/python/reconstruction/figures/TBS_PoC_5Bit_virtual_Sine_Reconstruction.pdf

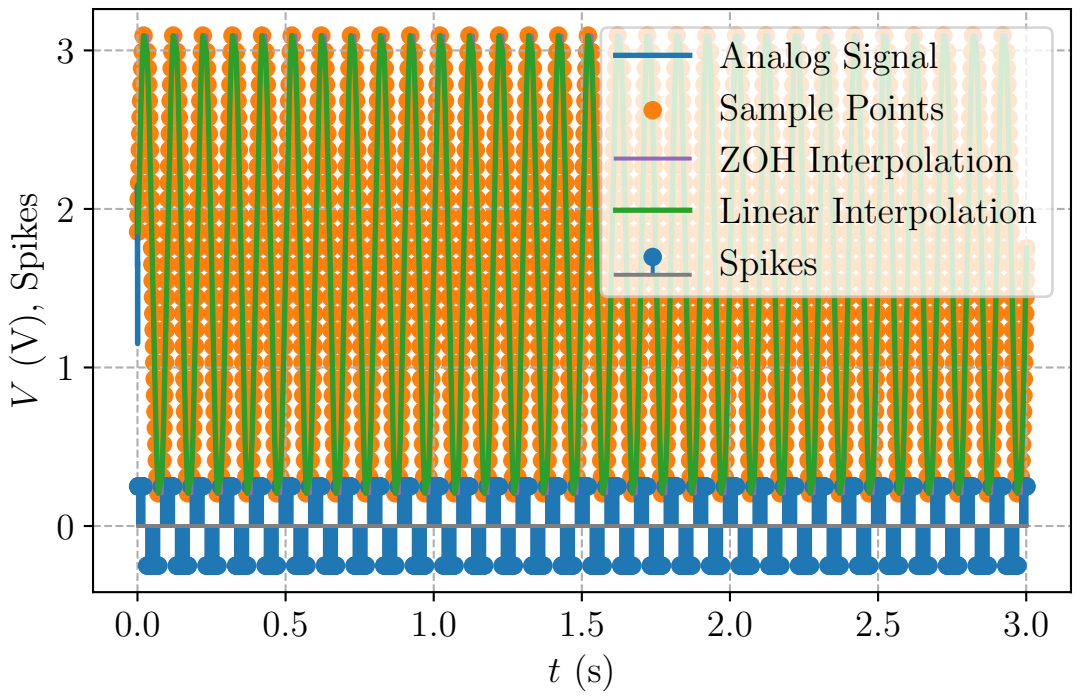
[picture p116: page 1]
V (V), Spikes; Analog Signal Sample Points ZOH Interpolation Linear Interpolation Spikes
