iic-jku/SG13G2_ATBS-ADC/SG13G2_ATBS-ADC-main/python/reconstruction/figures/TBS_Xschem_5Bit_virtual_Sine_Reconstruction_1us.pdf

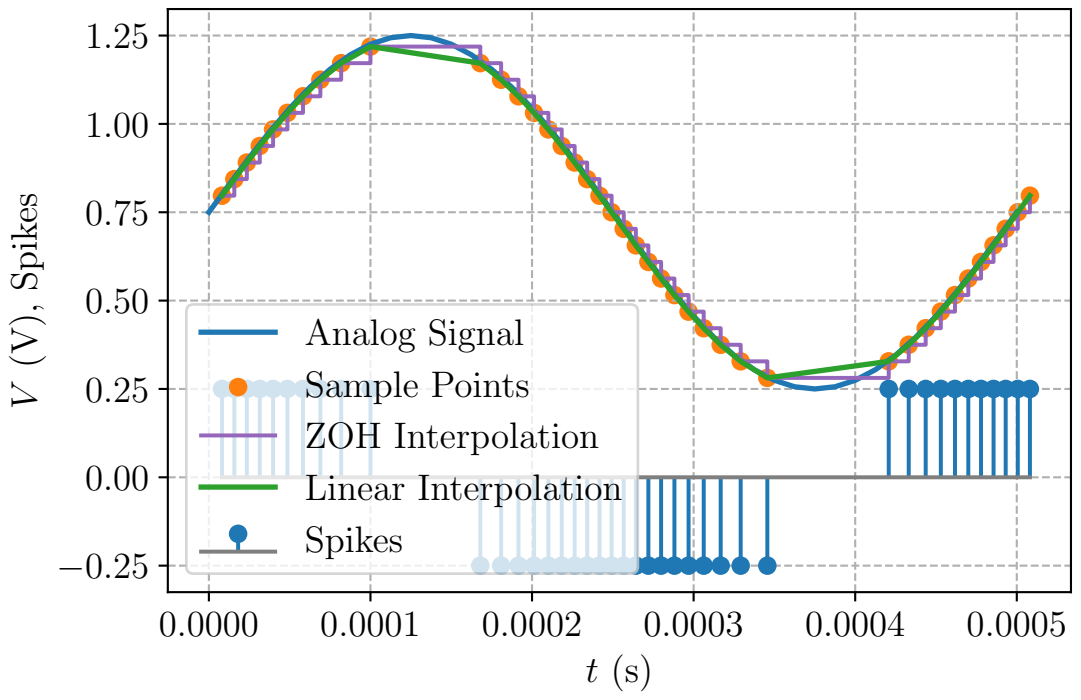
[picture p117: page 1]
V (V), Spikes; Sample Points; Spikes

Analog Signal

ZOH Interpolation
Linear Interpolation
