iic-jku/SG13G2_ATBS-ADC/FPGA-Design/tbs_core/adaptive_threshold_control/documentation/Adaptive-Threshold-Control_RTL2.pdf

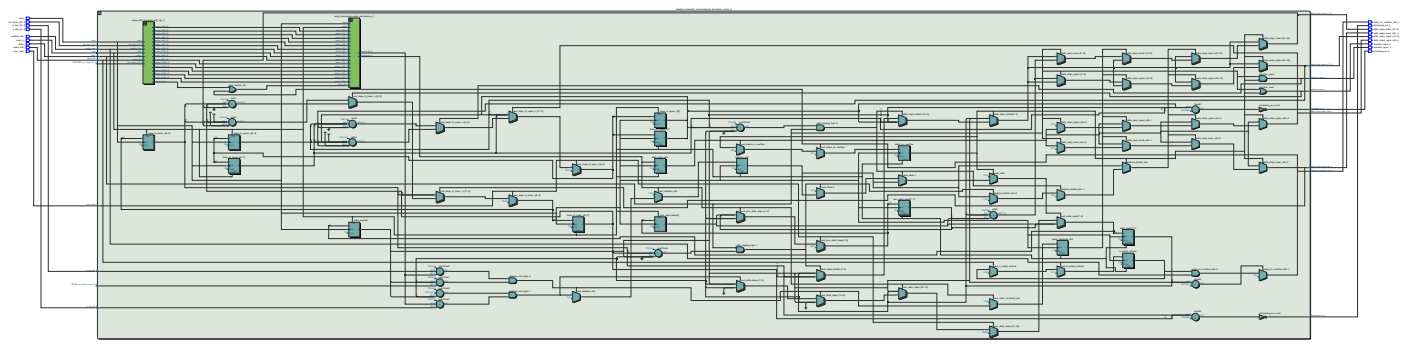
[picture p126: page 1]
adaptive_threshold_control:adaptive_threshold_control_0; clock_i overflow_strb_i reset_i spike_i spike_strb_i; sync_reset_i; curr_time_i[14..0]; d_max_i[2..0]; d_min_i[2..0]; 16'h7d00 win_length_i[15..0]; 8'h20 max_delta_steps_i[7..0]; adapt_on_overflow_strb_o; decreasing_en_o; delta_steps_lower_strb_o; delta_steps_upper_strb_o; direction_lower_o; direction_upper_o; increasing_en_o; delta_steps_upper_o[7..0]; delta_steps_lower_o[7..0]; 1'h0 CIN; Add0; OUT[7..0] +; Add1; OUT[8..0] +; Add2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

SCLR 2'h0 CLKCLRN Q | next_steps_to_upper_v[8..0] 0 9'h7d 1 | delta_steps_strb D SCLR 1'h0 CLKCLRN Q

next_steps_to_lower_v~[17..9] 01 | 1'h0 01 next_adaptive_strb | 1'h0 01 reset_delta~0

1'h0 CIN A[8..0] B[8..0] LessThan5 OUT

delta_steps_limited~[7..0] 01 | next_is_empty_interval 0 1'h0 1 next_is_empty_interval 0 1'h1 1
