iic-jku/SG13G2_ATBS-ADC/FPGA-Design/tbs_core/ethernet/documentation/Ethernet_RTL3.pdf

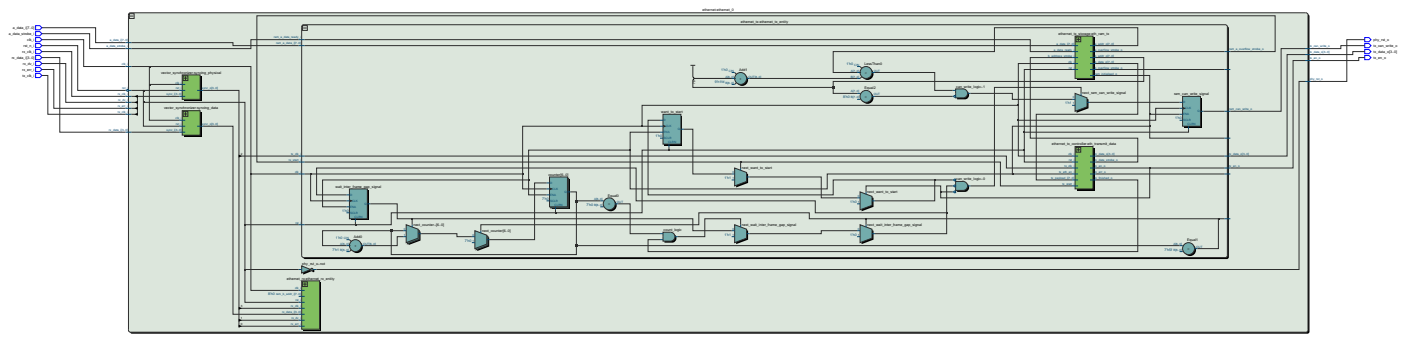
[picture p127: page 1]
ethernet:ethernet_0; a_data_strobe_i; clk_i; rst_i rx_clk_i rx_dv_i rx_err_i; tx_clk_i; a_data_i[7..0]; rx_data_i[3..0]; phy_rst_o; tx_can_write_o; tx_data_o[3..0]; ethernet_tx:ethernet_tx_entity; ram_a_data_ready_i; rst_i; tx_start_i; ram_a_data_i[7..0]; ram_a_overflow_strobe_o; ram_can_write_o; ethernet_rx:ethernet_rx_entity; rst_i rx_clk_i; rx_dv_i rx_err_i; 8'h0 ram_b_addr_i[7..0]; tx_data_o[3..0] +; 1'h0 CIN; Add0; OUT[6..0]; Add1; OUT[8..0] =Equal0; OUT; =Equal1; OUT =Equal2; OUT <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
