iic-jku/SG13G2_ATBS-ADC/FPGA-Design/tbs_core/spike_memory/documentation/Spike-Memory_RTL3.pdf

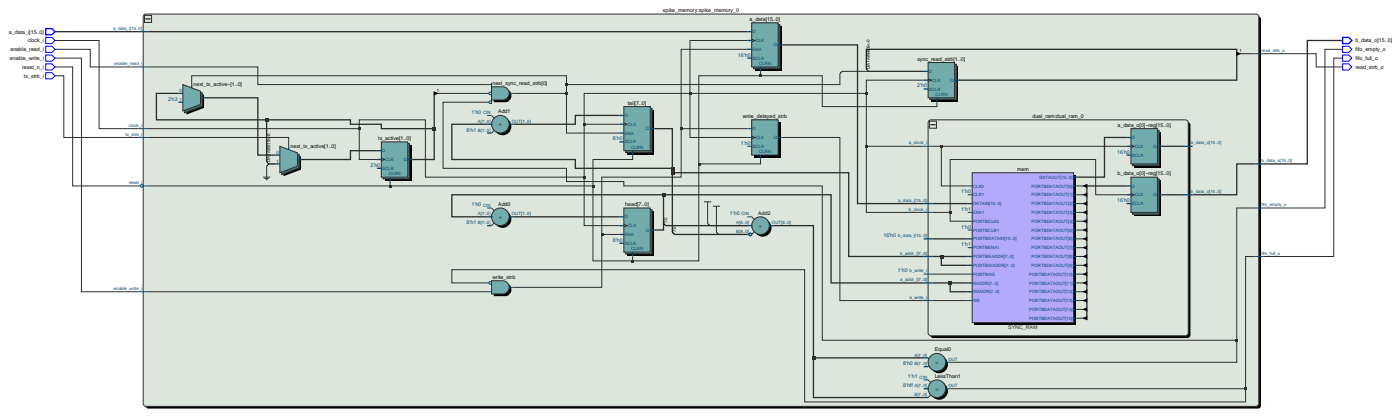
[picture p128: page 1]
spike_memory:spike_memory_0; clock_i; enable_read_i; enable_write_i; reset_i; tx_strb_i; a_data_i[15..0]; fifo_empty_o; fifo_full_o; read_strb_o; b_data_o[15..0]; a_clock_i; a_write_i; b_clock_i; 1'h0 b_write_i a_addr_i[7..0]; b_addr_i[7..0]; 16'h0 b_data_i[15..0]; a_data_o[15..0]; clock_i enable_read_i enable_write_i; fifo_empty_o fifo_full_o; reset_n_i; 1'h0 CIN; Add0; OUT[7..0] +; Add1; OUT[7..0]; Add2; OUT[8..0]; Equal0; OUT <; 1'h1 CIN; LessThan1; 8'hff A[7..0] B[7..0]; OUT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

dual_ram:dual_ram_0
PORTBDATAOUT[0] PORTBDATAOUT[1] PORTBDATAOUT[2] PORTBDATAOUT[3] PORTBDATAOUT[4] PORTBDATAOUT[5] PORTBDATAOUT[6] PORTBDATAOUT[7] PORTBDATAOUT[8] PORTBDATAOUT[9] PORTBDATAOUT[10] PORTBDATAOUT[11] PORTBDATAOUT[12] PORTBDATAOUT[13] PORTBDATAOUT[14] PORTBDATAOUT[15]
