iic-jku/SG13G2_ATBS-ADC/SG13G2_ATBS-ADC-main/sizing/techsweep/techsweep_sg13g2_lv_pmos_plots_overview/techsweep_sg13g2_lv_pmos_plots_overview.pdf

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

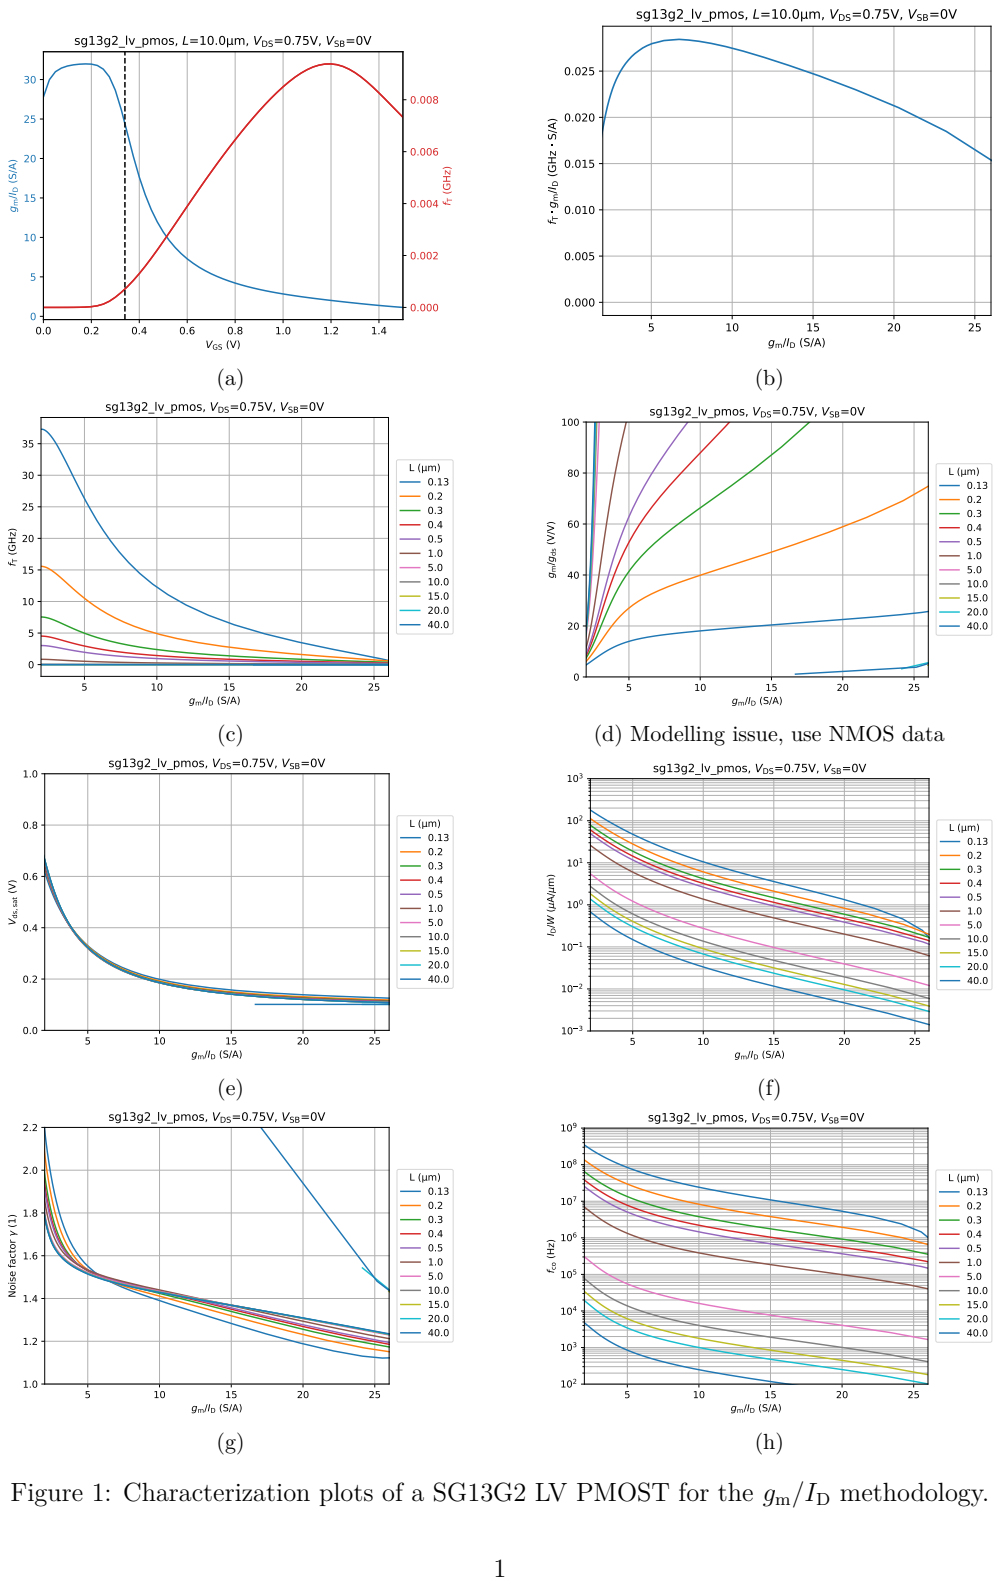
[picture p132: page 1]
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
