iic-jku/SG13G2_ATBS-ADC/SG13G2_ATBS-ADC-main/sizing/techsweep/techsweep_sg13g2_hv_nmos_plots_overview/plots/gamma_gmID.pdf

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

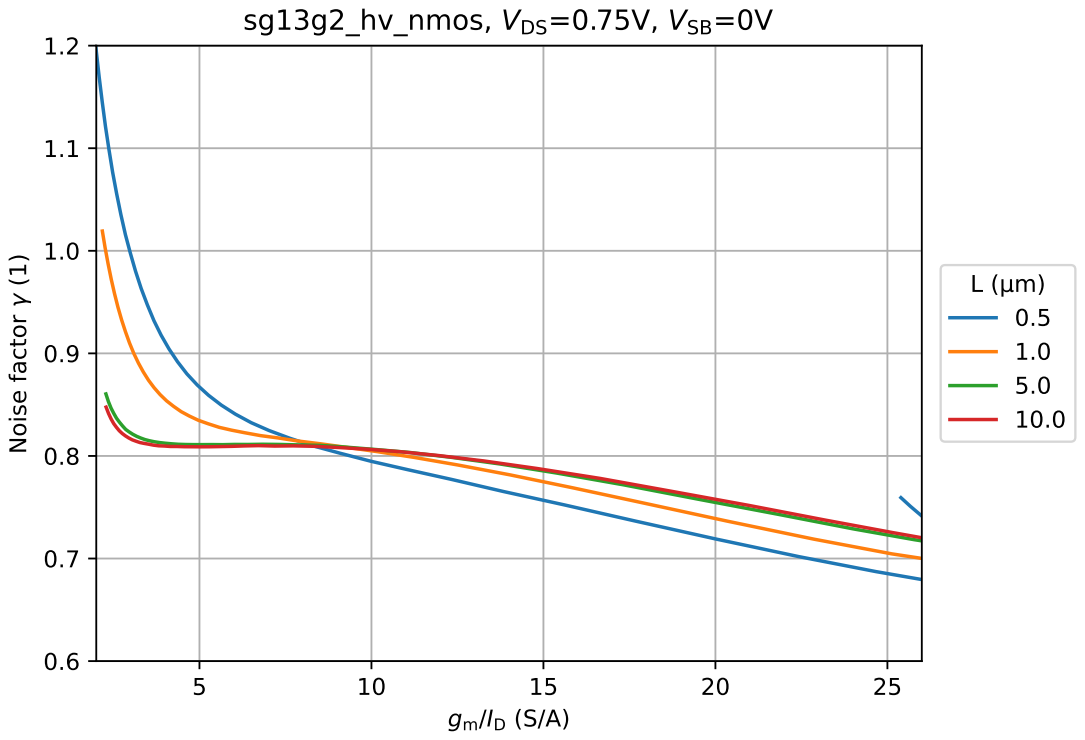
[picture p135: page 1]
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
