iic-jku/SG13G2_ATBS-ADC/PCB-Design/TBS_Analog_Front-End/TBS_Analog_Front-End_LTspice/AD8232.asc

C8: cap; 1n
C9: cap; 3.3µ
C10: cap; 1.5n
C11: cap; 1.5n
C12: cap; 3.3µ
C13: cap; 100n
C14: cap; 100n
R6: res; 10Meg
R7: res; 10Meg
R8: res; 180k
R9: res; 360k
R11: res; 180k
R12: res; 1Meg
R13: res; 1Meg
R14: res; 100k
R15: res; 56k
R16: res; 1Meg
R17: res; 1Meg
R18: res; 150k
R19: res; 1Meg
R20: res; 270k
U1: AD8232
V1: voltage; 3.3
V2: voltage; ""; AC 1
Named nets: LA, RA, RL, OUT, 0, REFOUT, REFIN
Circuit for ECG Waveform Monitoring
by Simon Dorrer
.ac dec 1001 0.01 1k
;.noise OUT V2 dec 1001 0.01 1000
