iic-jku/SG13G2_ATBS-ADC/SG13G2_ATBS-ADC-main/verilog/atbs_core_fixed_window/quartus/db/atbs_core_fixed_window_board.smp_dump.txt

State Machine - |atbs_core_fixed_window_board|atbs_core_fixed_window_8000000_20_800000_4_10_2_2_255_0_2_2_3_8_19_524288_80_8_8_160_11_2048_2_20_9_417_8:atbs_core_0|n1121_q
Name n1121_q.111 n1121_q.110 n1121_q.101 n1121_q.100 n1121_q.011 n1121_q.010 n1121_q.000 n1121_q.001 
n1121_q.001 0 0 0 0 0 0 0 0 
n1121_q.000 0 0 0 0 0 0 1 1 
n1121_q.010 0 0 0 0 0 1 0 1 
n1121_q.011 0 0 0 0 1 0 0 1 
n1121_q.100 0 0 0 1 0 0 0 1 
n1121_q.101 0 0 1 0 0 0 0 1 
n1121_q.110 0 1 0 0 0 0 0 1 
n1121_q.111 1 0 0 0 0 0 0 1 

State Machine - |atbs_core_fixed_window_board|atbs_core_fixed_window_8000000_20_800000_4_10_2_2_255_0_2_2_3_8_19_524288_80_8_8_160_11_2048_2_20_9_417_8:atbs_core_0|uart_9_8:uart_0|uart_rx_9_8:uart_rx_0|n2922_q
Name n2922_q.11 n2922_q.10 n2922_q.01 n2922_q.00 
n2922_q.00 0 0 0 0 
n2922_q.01 0 0 1 1 
n2922_q.10 0 1 0 1 
n2922_q.11 1 0 0 1 

State Machine - |atbs_core_fixed_window_board|atbs_core_fixed_window_8000000_20_800000_4_10_2_2_255_0_2_2_3_8_19_524288_80_8_8_160_11_2048_2_20_9_417_8:atbs_core_0|uart_9_8:uart_0|uart_tx_9_8:uart_tx_0|n2817_q
Name n2817_q.011 n2817_q.010 n2817_q.001 n2817_q.000 n2817_q.100 
n2817_q.000 0 0 0 0 0 
n2817_q.001 0 0 1 1 0 
n2817_q.010 0 1 0 1 0 
n2817_q.011 1 0 0 1 0 
n2817_q.100 0 0 0 1 1 

State Machine - |atbs_core_fixed_window_board|atbs_core_fixed_window_8000000_20_800000_4_10_2_2_255_0_2_2_3_8_19_524288_80_8_8_160_11_2048_2_20_9_417_8:atbs_core_0|debouncer_4_10:debouncer_5|n1220_q
Name n1220_q.00 n1220_q.10 n1220_q.01 
n1220_q.00 0 0 0 
n1220_q.01 1 0 1 
n1220_q.10 1 1 0 

State Machine - |atbs_core_fixed_window_board|atbs_core_fixed_window_8000000_20_800000_4_10_2_2_255_0_2_2_3_8_19_524288_80_8_8_160_11_2048_2_20_9_417_8:atbs_core_0|debouncer_4_10:debouncer_4|n1220_q
Name n1220_q.00 n1220_q.10 n1220_q.01 
n1220_q.00 0 0 0 
n1220_q.01 1 0 1 
n1220_q.10 1 1 0 

State Machine - |atbs_core_fixed_window_board|atbs_core_fixed_window_8000000_20_800000_4_10_2_2_255_0_2_2_3_8_19_524288_80_8_8_160_11_2048_2_20_9_417_8:atbs_core_0|debouncer_4_10:debouncer_3|n1220_q
Name n1220_q.00 n1220_q.10 n1220_q.01 
n1220_q.00 0 0 0 
n1220_q.01 1 0 1 
n1220_q.10 1 1 0 

State Machine - |atbs_core_fixed_window_board|atbs_core_fixed_window_8000000_20_800000_4_10_2_2_255_0_2_2_3_8_19_524288_80_8_8_160_11_2048_2_20_9_417_8:atbs_core_0|debouncer_4_10:debouncer_2|n1220_q
Name n1220_q.00 n1220_q.10 n1220_q.01 
n1220_q.00 0 0 0 
n1220_q.01 1 0 1 
n1220_q.10 1 1 0 

State Machine - |atbs_core_fixed_window_board|atbs_core_fixed_window_8000000_20_800000_4_10_2_2_255_0_2_2_3_8_19_524288_80_8_8_160_11_2048_2_20_9_417_8:atbs_core_0|debouncer_4_10:debouncer_1|n1220_q
Name n1220_q.00 n1220_q.10 n1220_q.01 
n1220_q.00 0 0 0 
n1220_q.01 1 0 1 
n1220_q.10 1 1 0 

State Machine - |atbs_core_fixed_window_board|atbs_core_fixed_window_8000000_20_800000_4_10_2_2_255_0_2_2_3_8_19_524288_80_8_8_160_11_2048_2_20_9_417_8:atbs_core_0|debouncer_4_10:debouncer_0|n1220_q
Name n1220_q.00 n1220_q.10 n1220_q.01 
n1220_q.00 0 0 0 
n1220_q.01 1 0 1 
n1220_q.10 1 1 0 
