iic-jku/SG13G2_ATBS-ADC/SG13G2_ATBS-ADC-main/verilog/atbs_core_fixed_window/rtl/atbs_core_fixed_window_board.v

module priority_encoder_3_3
  (input  clock_i,
   input  reset_i,
   input  [2:0] code_i,
   output [2:0] bin_o);
  wire [2:0] bin;
  wire n3525_o;
  wire [2:0] n3528_o;
  wire n3530_o;
  wire [2:0] n3532_o;
  wire n3533_o;
  wire [2:0] n3535_o;
  assign bin_o = bin; //(module output)
  /* ../../../vhdl/atbs_core_fixed_window/adaptive_threshold_control/Priority-Encoder/rtl/priority_encoder_ea.vhd:33:8  */
  assign bin = n3535_o; // (signal)
  /* ../../../vhdl/atbs_core_fixed_window/adaptive_threshold_control/Priority-Encoder/rtl/priority_encoder_ea.vhd:44:16  */
  assign n3525_o = code_i[0]; // extract
  /* ../../../vhdl/atbs_core_fixed_window/adaptive_threshold_control/Priority-Encoder/rtl/priority_encoder_ea.vhd:44:7  */
  assign n3528_o = n3525_o ? 3'b001 : 3'b000;
  /* ../../../vhdl/atbs_core_fixed_window/adaptive_threshold_control/Priority-Encoder/rtl/priority_encoder_ea.vhd:44:16  */
  assign n3530_o = code_i[1]; // extract
  /* ../../../vhdl/atbs_core_fixed_window/adaptive_threshold_control/Priority-Encoder/rtl/priority_encoder_ea.vhd:44:7  */
  assign n3532_o = n3530_o ? 3'b010 : n3528_o;
  /* ../../../vhdl/atbs_core_fixed_window/adaptive_threshold_control/Priority-Encoder/rtl/priority_encoder_ea.vhd:44:16  */
  assign n3533_o = code_i[2]; // extract
  /* ../../../vhdl/atbs_core_fixed_window/adaptive_threshold_control/Priority-Encoder/rtl/priority_encoder_ea.vhd:44:7  */
  assign n3535_o = n3533_o ? 3'b011 : n3532_o;
endmodule

module spike_2_thermocode_6
  (input  [1:0] spike_i,
   input  [5:0] thermo_i,
   output [5:0] thermo_o);
  wire plus;
  wire minus;
  wire [5:0] thermo;
  wire n3490_o;
  wire n3491_o;
  wire n3494_o;
  wire n3495_o;
  wire n3496_o;
  wire n3497_o;
  wire n3498_o;
  wire n3499_o;
  wire n3500_o;
  wire n3501_o;
  wire n3502_o;
  wire n3503_o;
  wire n3504_o;
  wire n3505_o;
  wire n3506_o;
  wire n3507_o;
  wire n3508_o;
  wire n3509_o;
  wire n3510_o;
  wire n3511_o;
  wire n3512_o;
  wire n3513_o;
  wire n3514_o;
  wire n3515_o;
  wire n3516_o;
  wire n3517_o;
  wire n3518_o;
  wire n3519_o;
  wire [5:0] n3520_o;
  wire [5:0] n3521_o;
  assign thermo_o = thermo; //(module output)
  /* ../../../vhdl/atbs_core_fixed_window/adaptive_threshold_control/Spike-2-Thermocode/rtl/spike_2_thermocode_ea.vhd:30:8  */
  assign plus = n3491_o; // (signal)
  /* ../../../vhdl/atbs_core_fixed_window/adaptive_threshold_control/Spike-2-Thermocode/rtl/spike_2_thermocode_ea.vhd:31:8  */
  assign minus = n3490_o; // (signal)
  /* ../../../vhdl/atbs_core_fixed_window/adaptive_threshold_control/Spike-2-Thermocode/rtl/spike_2_thermocode_ea.vhd:32:8  */
  assign thermo = n3521_o; // (signal)
  /* ../../../vhdl/atbs_core_fixed_window/adaptive_threshold_control/Spike-2-Thermocode/rtl/spike_2_thermocode_ea.vhd:37:19  */
  assign n3490_o = spike_i[1]; // extract
  /* ../../../vhdl/atbs_core_fixed_window/adaptive_threshold_control/Spike-2-Thermocode/rtl/spike_2_thermocode_ea.vhd:38:18  */
  assign n3491_o = spike_i[0]; // extract
  /* ../../../vhdl/atbs_core_fixed_window/adaptive_threshold_control/Spike-2-Thermocode/rtl/spike_2_thermocode_ea.vhd:43:16  */
  assign n3494_o = spike_i == 2'b00;
  /* ../../../vhdl/atbs_core_fixed_window/adaptive_threshold_control/Spike-2-Thermocode/rtl/spike_2_thermocode_ea.vhd:48:37  */
  assign n3495_o = thermo_i[1]; // extract
  /* ../../../vhdl/atbs_core_fixed_window/adaptive_threshold_control/Spike-2-Thermocode/rtl/spike_2_thermocode_ea.vhd:48:41  */
  assign n3496_o = n3495_o & minus;
  /* ../../../vhdl/atbs_core_fixed_window/adaptive_threshold_control/Spike-2-Thermocode/rtl/spike_2_thermocode_ea.vhd:48:25  */
  assign n3497_o = plus | n3496_o;
  /* ../../../vhdl/atbs_core_fixed_window/adaptive_threshold_control/Spike-2-Thermocode/rtl/spike_2_thermocode_ea.vhd:53:31  */
  assign n3498_o = thermo_i[0]; // extract
  /* ../../../vhdl/atbs_core_fixed_window/adaptive_threshold_control/Spike-2-Thermocode/rtl/spike_2_thermocode_ea.vhd:53:37  */
  assign n3499_o = n3498_o & plus;
  /* ../../../vhdl/atbs_core_fixed_window/adaptive_threshold_control/Spike-2-Thermocode/rtl/spike_2_thermocode_ea.vhd:53:59  */
  assign n3500_o = thermo_i[2]; // extract
  /* ../../../vhdl/atbs_core_fixed_window/adaptive_threshold_control/Spike-2-Thermocode/rtl/spike_2_thermocode_ea.vhd:53:65  */
  assign n3501_o = n3500_o & minus;
  /* ../../../vhdl/atbs_core_fixed_window/adaptive_threshold_control/Spike-2-Thermocode/rtl/spike_2_thermocode_ea.vhd:53:47  */
  assign n3502_o = n3499_o | n3501_o;
  /* ../../../vhdl/atbs_core_fixed_window/adaptive_threshold_control/Spike-2-Thermocode/rtl/spike_2_thermocode_ea.vhd:53:31  */
  assign n3503_o = thermo_i[1]; // extract
  /* ../../../vhdl/atbs_core_fixed_window/adaptive_threshold_control/Spike-2-Thermocode/rtl/spike_2_thermocode_ea.vhd:53:37  */
  assign n3504_o = n3503_o & plus;
  /* ../../../vhdl/atbs_core_fixed_window/adaptive_threshold_control/Spike-2-Thermocode/rtl/spike_2_thermocode_ea.vhd:53:59  */
  assign n3505_o = thermo_i[3]; // extract
  /* ../../../vhdl/atbs_core_fixed_window/adaptive_threshold_control/Spike-2-Thermocode/rtl/spike_2_thermocode_ea.vhd:53:65  */
  assign n3506_o = n3505_o & minus;
  /* ../../../vhdl/atbs_core_fixed_window/adaptive_threshold_control/Spike-2-Thermocode/rtl/spike_2_thermocode_ea.vhd:53:47  */
  assign n3507_o = n3504_o | n3506_o;
  /* ../../../vhdl/atbs_core_fixed_window/adaptive_threshold_control/Spike-2-Thermocode/rtl/spike_2_thermocode_ea.vhd:53:31  */
  assign n3508_o = thermo_i[2]; // extract
  /* ../../../vhdl/atbs_core_fixed_window/adaptive_threshold_control/Spike-2-Thermocode/rtl/spike_2_thermocode_ea.vhd:53:37  */
  assign n3509_o = n3508_o & plus;
  /* ../../../vhdl/atbs_core_fixed_window/adaptive_threshold_control/Spike-2-Thermocode/rtl/spike_2_thermocode_ea.vhd:53:59  */
  assign n3510_o = thermo_i[4]; // extract
  /* ../../../vhdl/atbs_core_fixed_window/adaptive_threshold_control/Spike-2-Thermocode/rtl/spike_2_thermocode_ea.vhd:53:65  */
  assign n3511_o = n3510_o & minus;
  /* ../../../vhdl/atbs_core_fixed_window/adaptive_threshold_control/Spike-2-Thermocode/rtl/spike_2_thermocode_ea.vhd:53:47  */
  assign n3512_o = n3509_o | n3511_o;
  /* ../../../vhdl/atbs_core_fixed_window/adaptive_threshold_control/Spike-2-Thermocode/rtl/spike_2_thermocode_ea.vhd:53:31  */
  assign n3513_o = thermo_i[3]; // extract
  /* ../../../vhdl/atbs_core_fixed_window/adaptive_threshold_control/Spike-2-Thermocode/rtl/spike_2_thermocode_ea.vhd:53:37  */
  assign n3514_o = n3513_o & plus;
  /* ../../../vhdl/atbs_core_fixed_window/adaptive_threshold_control/Spike-2-Thermocode/rtl/spike_2_thermocode_ea.vhd:53:59  */
  assign n3515_o = thermo_i[5]; // extract
  /* ../../../vhdl/atbs_core_fixed_window/adaptive_threshold_control/Spike-2-Thermocode/rtl/spike_2_thermocode_ea.vhd:53:65  */
  assign n3516_o = n3515_o & minus;
  /* ../../../vhdl/atbs_core_fixed_window/adaptive_threshold_control/Spike-2-Thermocode/rtl/spike_2_thermocode_ea.vhd:53:47  */
  assign n3517_o = n3514_o | n3516_o;
  /* ../../../vhdl/atbs_core_fixed_window/adaptive_threshold_control/Spike-2-Thermocode/rtl/spike_2_thermocode_ea.vhd:57:40  */
  assign n3518_o = thermo_i[4]; // extract
  /* ../../../vhdl/atbs_core_fixed_window/adaptive_threshold_control/Spike-2-Thermocode/rtl/spike_2_thermocode_ea.vhd:57:56  */
  assign n3519_o = n3518_o & plus;
  assign n3520_o = {n3519_o, n3517_o, n3512_o, n3507_o, n3502_o, n3497_o};
  /* ../../../vhdl/atbs_core_fixed_window/adaptive_threshold_control/Spike-2-Thermocode/rtl/spike_2_thermocode_ea.vhd:43:5  */
  assign n3521_o = n3494_o ? thermo_i : n3520_o;
endmodule

module uart_rx_9_8
  (input  clock_i,
   input  reset_i,
   input  [8:0] baudrate_adj_i,
   input  rx_i,
   output [7:0] data_o,
   output data_valid_strb_o);
  wire [2:0] receive_counter_value;
  wire [2:0] next_receive_counter_value;
  wire [8:0] baud_counter_value;
  wire [8:0] next_baud_counter_value;
  wire [7:0] received_data;
  wire [7:0] next_received_data;
  wire data_valid_strb;
  wire [1:0] rx_state;
  wire [1:0] next_rx_state;
  wire next_strobe;
  wire n3384_o;
  wire n3385_o;
  wire [2:0] n3387_o;
  wire [2:0] n3388_o;
  wire [2:0] n3390_o;
  wire n3393_o;
  wire [8:0] n3395_o;
  wire [8:0] n3397_o;
  wire n3399_o;
  wire [8:0] n3401_o;
  wire n3404_o;
  wire [1:0] n3406_o;
  wire n3408_o;
  wire n3409_o;
  wire [1:0] n3411_o;
  wire n3413_o;
  wire [8:0] n3415_o;
  wire n3416_o;
  wire [7:0] n3420_o;
  wire n3421_o;
  wire n3423_o;
  wire n3424_o;
  wire [1:0] n3426_o;
  wire n3428_o;
  wire [8:0] n3430_o;
  wire n3431_o;
  wire [1:0] n3433_o;
  wire n3436_o;
  wire n3438_o;
  wire [3:0] n3439_o;
  reg [7:0] n3441_o;
  reg [1:0] n3442_o;
  reg n3445_o;
  reg [2:0] n3448_q;
  reg [8:0] n3449_q;
  reg [7:0] n3450_q;
  reg n3451_q;
  reg [1:0] n3452_q;
  wire n3454_o;
  wire n3455_o;
  wire n3456_o;
  wire n3457_o;
  wire n3458_o;
  wire n3459_o;
  wire n3460_o;
  wire n3461_o;
  wire n3462_o;
  wire n3463_o;
  wire n3464_o;
  wire n3465_o;
  wire n3466_o;
  wire n3467_o;
  wire n3468_o;
  wire n3469_o;
  wire n3470_o;
  wire n3471_o;
  wire n3472_o;
  wire n3473_o;
  wire n3474_o;
  wire n3475_o;
  wire n3476_o;
  wire n3477_o;
  wire n3478_o;
  wire n3479_o;
  wire n3480_o;
  wire n3481_o;
  wire n3482_o;
  wire n3483_o;
  wire n3484_o;
  wire n3485_o;
  wire n3486_o;
  wire n3487_o;
  wire [7:0] n3488_o;
  assign data_o = received_data; //(module output)
  assign data_valid_strb_o = data_valid_strb; //(module output)
  /* ../../../vhdl/atbs_core_fixed_window/uart/rtl/uart_rx_ea.vhd:38:8  */
  assign receive_counter_value = n3448_q; // (signal)
  /* ../../../vhdl/atbs_core_fixed_window/uart/rtl/uart_rx_ea.vhd:39:8  */
  assign next_receive_counter_value = n3390_o; // (signal)
  /* ../../../vhdl/atbs_core_fixed_window/uart/rtl/uart_rx_ea.vhd:42:8  */
  assign baud_counter_value = n3449_q; // (signal)
  /* ../../../vhdl/atbs_core_fixed_window/uart/rtl/uart_rx_ea.vhd:43:8  */
  assign next_baud_counter_value = n3401_o; // (signal)
  /* ../../../vhdl/atbs_core_fixed_window/uart/rtl/uart_rx_ea.vhd:46:8  */
  assign received_data = n3450_q; // (signal)
  /* ../../../vhdl/atbs_core_fixed_window/uart/rtl/uart_rx_ea.vhd:47:8  */
  assign next_received_data = n3441_o; // (signal)
  /* ../../../vhdl/atbs_core_fixed_window/uart/rtl/uart_rx_ea.vhd:48:8  */
  assign data_valid_strb = n3451_q; // (signal)
  /* ../../../vhdl/atbs_core_fixed_window/uart/rtl/uart_rx_ea.vhd:51:8  */
  assign rx_state = n3452_q; // (signal)
  /* ../../../vhdl/atbs_core_fixed_window/uart/rtl/uart_rx_ea.vhd:52:8  */
  assign next_rx_state = n3442_o; // (signal)
  /* ../../../vhdl/atbs_core_fixed_window/uart/rtl/uart_rx_ea.vhd:54:8  */
  assign next_strobe = n3445_o; // (signal)
  /* ../../../vhdl/atbs_core_fixed_window/uart/rtl/uart_rx_ea.vhd:81:17  */
  assign n3384_o = rx_state == 2'b10;
  /* ../../../vhdl/atbs_core_fixed_window/uart/rtl/uart_rx_ea.vhd:82:29  */
  assign n3385_o = baud_counter_value == baudrate_adj_i;
  /* ../../../vhdl/atbs_core_fixed_window/uart/rtl/uart_rx_ea.vhd:83:61  */
  assign n3387_o = receive_counter_value + 3'b001;
  /* ../../../vhdl/atbs_core_fixed_window/uart/rtl/uart_rx_ea.vhd:82:7  */
  assign n3388_o = n3385_o ? n3387_o : receive_counter_value;
  /* ../../../vhdl/atbs_core_fixed_window/uart/rtl/uart_rx_ea.vhd:81:5  */
  assign n3390_o = n3384_o ? n3388_o : 3'b000;
  /* ../../../vhdl/atbs_core_fixed_window/uart/rtl/uart_rx_ea.vhd:96:27  */
  assign n3393_o = $unsigned(baud_counter_value) < $unsigned(baudrate_adj_i);
  /* ../../../vhdl/atbs_core_fixed_window/uart/rtl/uart_rx_ea.vhd:97:53  */
  assign n3395_o = baud_counter_value + 9'b000000001;
  /* ../../../vhdl/atbs_core_fixed_window/uart/rtl/uart_rx_ea.vhd:96:5  */
  assign n3397_o = n3393_o ? n3395_o : 9'b000000000;
  /* ../../../vhdl/atbs_core_fixed_window/uart/rtl/uart_rx_ea.vhd:102:17  */
  assign n3399_o = rx_state == 2'b00;
  /* ../../../vhdl/atbs_core_fixed_window/uart/rtl/uart_rx_ea.vhd:102:5  */
  assign n3401_o = n3399_o ? 9'b000000000 : n3397_o;
  /* ../../../vhdl/atbs_core_fixed_window/uart/rtl/uart_rx_ea.vhd:118:17  */
  assign n3404_o = ~rx_i;
  /* ../../../vhdl/atbs_core_fixed_window/uart/rtl/uart_rx_ea.vhd:118:9  */
  assign n3406_o = n3404_o ? 2'b01 : rx_state;
  /* ../../../vhdl/atbs_core_fixed_window/uart/rtl/uart_rx_ea.vhd:116:7  */
  assign n3408_o = rx_state == 2'b00;
  /* ../../../vhdl/atbs_core_fixed_window/uart/rtl/uart_rx_ea.vhd:123:31  */
  assign n3409_o = baud_counter_value == baudrate_adj_i;
  /* ../../../vhdl/atbs_core_fixed_window/uart/rtl/uart_rx_ea.vhd:123:9  */
  assign n3411_o = n3409_o ? 2'b10 : rx_state;
  /* ../../../vhdl/atbs_core_fixed_window/uart/rtl/uart_rx_ea.vhd:122:7  */
  assign n3413_o = rx_state == 2'b01;
  /* ../../../vhdl/atbs_core_fixed_window/uart/rtl/uart_rx_ea.vhd:128:33  */
  assign n3415_o = baudrate_adj_i >> 31'b0000000000000000000000000000001;
  /* ../../../vhdl/atbs_core_fixed_window/uart/rtl/uart_rx_ea.vhd:128:31  */
  assign n3416_o = baud_counter_value == n3415_o;
  /* ../../../vhdl/atbs_core_fixed_window/uart/rtl/uart_rx_ea.vhd:128:9  */
  assign n3420_o = n3416_o ? n3488_o : received_data;
  /* ../../../vhdl/atbs_core_fixed_window/uart/rtl/uart_rx_ea.vhd:131:31  */
  assign n3421_o = baud_counter_value == baudrate_adj_i;
  /* ../../../vhdl/atbs_core_fixed_window/uart/rtl/uart_rx_ea.vhd:131:74  */
  assign n3423_o = receive_counter_value == 3'b111;
  /* ../../../vhdl/atbs_core_fixed_window/uart/rtl/uart_rx_ea.vhd:131:48  */
  assign n3424_o = n3423_o & n3421_o;
  /* ../../../vhdl/atbs_core_fixed_window/uart/rtl/uart_rx_ea.vhd:131:9  */
  assign n3426_o = n3424_o ? 2'b11 : rx_state;
  /* ../../../vhdl/atbs_core_fixed_window/uart/rtl/uart_rx_ea.vhd:127:7  */
  assign n3428_o = rx_state == 2'b10;
  /* ../../../vhdl/atbs_core_fixed_window/uart/rtl/uart_rx_ea.vhd:136:33  */
  assign n3430_o = baudrate_adj_i >> 31'b0000000000000000000000000000001;
  /* ../../../vhdl/atbs_core_fixed_window/uart/rtl/uart_rx_ea.vhd:136:31  */
  assign n3431_o = baud_counter_value == n3430_o;
  /* ../../../vhdl/atbs_core_fixed_window/uart/rtl/uart_rx_ea.vhd:136:9  */
  assign n3433_o = n3431_o ? 2'b00 : rx_state;
  /* ../../../vhdl/atbs_core_fixed_window/uart/rtl/uart_rx_ea.vhd:136:9  */
  assign n3436_o = n3431_o ? 1'b1 : 1'b0;
  /* ../../../vhdl/atbs_core_fixed_window/uart/rtl/uart_rx_ea.vhd:135:7  */
  assign n3438_o = rx_state == 2'b11;
  assign n3439_o = {n3438_o, n3428_o, n3413_o, n3408_o};
  /* ../../../vhdl/atbs_core_fixed_window/uart/rtl/uart_rx_ea.vhd:115:5  */
  always @*
    case (n3439_o)
      4'b1000: n3441_o = received_data;
      4'b0100: n3441_o = n3420_o;
      4'b0010: n3441_o = received_data;
      4'b0001: n3441_o = received_data;
      default: n3441_o = 8'b00000000;
    endcase
  /* ../../../vhdl/atbs_core_fixed_window/uart/rtl/uart_rx_ea.vhd:115:5  */
  always @*
    case (n3439_o)
      4'b1000: n3442_o = n3433_o;
      4'b0100: n3442_o = n3426_o;
      4'b0010: n3442_o = n3411_o;
      4'b0001: n3442_o = n3406_o;
      default: n3442_o = rx_state;
    endcase
  /* ../../../vhdl/atbs_core_fixed_window/uart/rtl/uart_rx_ea.vhd:115:5  */
  always @*
    case (n3439_o)
      4'b1000: n3445_o = n3436_o;
      4'b0100: n3445_o = 1'b0;
      4'b0010: n3445_o = 1'b0;
      4'b0001: n3445_o = 1'b0;
      default: n3445_o = 1'b0;
    endcase
  /* ../../../vhdl/atbs_core_fixed_window/uart/rtl/uart_rx_ea.vhd:66:5  */
  always @(posedge clock_i or posedge reset_i)
    if (reset_i)
      n3448_q <= 3'b000;
    else
      n3448_q <= next_receive_counter_value;
  /* ../../../vhdl/atbs_core_fixed_window/uart/rtl/uart_rx_ea.vhd:66:5  */
  always @(posedge clock_i or posedge reset_i)
    if (reset_i)
      n3449_q <= 9'b000000000;
    else
      n3449_q <= next_baud_counter_value;
  /* ../../../vhdl/atbs_core_fixed_window/uart/rtl/uart_rx_ea.vhd:66:5  */
  always @(posedge clock_i or posedge reset_i)
    if (reset_i)
      n3450_q <= 8'b00000000;
    else
      n3450_q <= next_received_data;
  /* ../../../vhdl/atbs_core_fixed_window/uart/rtl/uart_rx_ea.vhd:66:5  */
  always @(posedge clock_i or posedge reset_i)
    if (reset_i)
      n3451_q <= 1'b0;
    else
      n3451_q <= next_strobe;
  /* ../../../vhdl/atbs_core_fixed_window/uart/rtl/uart_rx_ea.vhd:66:5  */
  always @(posedge clock_i or posedge reset_i)
    if (reset_i)
      n3452_q <= 2'b00;
    else
      n3452_q <= next_rx_state;
  /* ../../../vhdl/atbs_core_fixed_window/uart/rtl/uart_rx_ea.vhd:129:11  */
  assign n3454_o = receive_counter_value[2]; // extract
  /* ../../../vhdl/atbs_core_fixed_window/uart/rtl/uart_rx_ea.vhd:129:11  */
  assign n3455_o = ~n3454_o;
  /* ../../../vhdl/atbs_core_fixed_window/uart/rtl/uart_rx_ea.vhd:129:11  */
  assign n3456_o = receive_counter_value[1]; // extract
  /* ../../../vhdl/atbs_core_fixed_window/uart/rtl/uart_rx_ea.vhd:129:11  */
  assign n3457_o = ~n3456_o;
  /* ../../../vhdl/atbs_core_fixed_window/uart/rtl/uart_rx_ea.vhd:129:11  */
  assign n3458_o = n3455_o & n3457_o;
  /* ../../../vhdl/atbs_core_fixed_window/uart/rtl/uart_rx_ea.vhd:129:11  */
  assign n3459_o = n3455_o & n3456_o;
  /* ../../../vhdl/atbs_core_fixed_window/uart/rtl/uart_rx_ea.vhd:129:11  */
  assign n3460_o = n3454_o & n3457_o;
  /* ../../../vhdl/atbs_core_fixed_window/uart/rtl/uart_rx_ea.vhd:129:11  */
  assign n3461_o = n3454_o & n3456_o;
  /* ../../../vhdl/atbs_core_fixed_window/uart/rtl/uart_rx_ea.vhd:129:11  */
  assign n3462_o = receive_counter_value[0]; // extract
  /* ../../../vhdl/atbs_core_fixed_window/uart/rtl/uart_rx_ea.vhd:129:11  */
  assign n3463_o = ~n3462_o;
  /* ../../../vhdl/atbs_core_fixed_window/uart/rtl/uart_rx_ea.vhd:129:11  */
  assign n3464_o = n3458_o & n3463_o;
  /* ../../../vhdl/atbs_core_fixed_window/uart/rtl/uart_rx_ea.vhd:129:11  */
  assign n3465_o = n3458_o & n3462_o;
  /* ../../../vhdl/atbs_core_fixed_window/uart/rtl/uart_rx_ea.vhd:129:11  */
  assign n3466_o = n3459_o & n3463_o;
  /* ../../../vhdl/atbs_core_fixed_window/uart/rtl/uart_rx_ea.vhd:129:11  */
  assign n3467_o = n3459_o & n3462_o;
  /* ../../../vhdl/atbs_core_fixed_window/uart/rtl/uart_rx_ea.vhd:129:11  */
  assign n3468_o = n3460_o & n3463_o;
  /* ../../../vhdl/atbs_core_fixed_window/uart/rtl/uart_rx_ea.vhd:129:11  */
  assign n3469_o = n3460_o & n3462_o;
  /* ../../../vhdl/atbs_core_fixed_window/uart/rtl/uart_rx_ea.vhd:129:11  */
  assign n3470_o = n3461_o & n3463_o;
  /* ../../../vhdl/atbs_core_fixed_window/uart/rtl/uart_rx_ea.vhd:129:11  */
  assign n3471_o = n3461_o & n3462_o;
  assign n3472_o = received_data[0]; // extract
  /* ../../../vhdl/atbs_core_fixed_window/uart/rtl/uart_rx_ea.vhd:129:11  */
  assign n3473_o = n3464_o ? rx_i : n3472_o;
  assign n3474_o = received_data[1]; // extract
  /* ../../../vhdl/atbs_core_fixed_window/uart/rtl/uart_rx_ea.vhd:129:11  */
  assign n3475_o = n3465_o ? rx_i : n3474_o;
  assign n3476_o = received_data[2]; // extract
  /* ../../../vhdl/atbs_core_fixed_window/uart/rtl/uart_rx_ea.vhd:129:11  */
  assign n3477_o = n3466_o ? rx_i : n3476_o;
  assign n3478_o = received_data[3]; // extract
  /* ../../../vhdl/atbs_core_fixed_window/uart/rtl/uart_rx_ea.vhd:129:11  */
  assign n3479_o = n3467_o ? rx_i : n3478_o;
  assign n3480_o = received_data[4]; // extract
  /* ../../../vhdl/atbs_core_fixed_window/uart/rtl/uart_rx_ea.vhd:129:11  */
  assign n3481_o = n3468_o ? rx_i : n3480_o;
  assign n3482_o = received_data[5]; // extract
  /* ../../../vhdl/atbs_core_fixed_window/uart/rtl/uart_rx_ea.vhd:129:11  */
  assign n3483_o = n3469_o ? rx_i : n3482_o;
  assign n3484_o = received_data[6]; // extract
  /* ../../../vhdl/atbs_core_fixed_window/uart/rtl/uart_rx_ea.vhd:129:11  */
  assign n3485_o = n3470_o ? rx_i : n3484_o;
  assign n3486_o = received_data[7]; // extract
  /* ../../../vhdl/atbs_core_fixed_window/uart/rtl/uart_rx_ea.vhd:129:11  */
  assign n3487_o = n3471_o ? rx_i : n3486_o;
  assign n3488_o = {n3487_o, n3485_o, n3483_o, n3481_o, n3479_o, n3477_o, n3475_o, n3473_o};
endmodule

module uart_tx_9_8
  (input  clock_i,
   input  reset_i,
   input  [8:0] baudrate_adj_i,
   input  tx_start_strb_i,
   input  [7:0] data_i,
   output tx_strb_o,
   output tx_o);
  wire tx;
  wire tx_strb;
  wire next_tx_strb;
  wire [2:0] transmit_counter_value;
  wire [2:0] next_transmit_counter_value;
  wire [8:0] baud_counter_value;
  wire [8:0] next_baud_counter_value;
  wire [2:0] tx_state;
  wire [2:0] next_tx_state;
  wire n3264_o;
  wire n3265_o;
  wire [2:0] n3267_o;
  wire [2:0] n3268_o;
  wire [2:0] n3270_o;
  wire n3273_o;
  wire [8:0] n3275_o;
  wire [8:0] n3277_o;
  wire n3280_o;
  wire [2:0] n3283_o;
  wire [2:0] n3284_o;
  wire n3286_o;
  wire n3287_o;
  wire n3290_o;
  wire [2:0] n3293_o;
  wire n3295_o;
  wire n3296_o;
  wire [2:0] n3298_o;
  wire n3300_o;
  wire n3302_o;
  wire n3307_o;
  wire n3308_o;
  wire n3309_o;
  wire [2:0] n3311_o;
  wire n3313_o;
  wire n3314_o;
  wire n3316_o;
  wire n3317_o;
  wire [2:0] n3320_o;
  wire [2:0] n3321_o;
  wire n3323_o;
  wire [4:0] n3324_o;
  reg n3329_o;
  reg [2:0] n3331_o;
  wire n3335_o;
  wire n3337_o;
  wire n3339_o;
  wire n3340_o;
  wire n3341_o;
  wire n3342_o;
  reg n3344_q;
  reg [2:0] n3345_q;
  reg [8:0] n3346_q;
  reg [2:0] n3347_q;
  wire n3348_o;
  wire n3349_o;
  wire n3350_o;
  wire n3351_o;
  wire n3352_o;
  wire n3353_o;
  wire n3354_o;
  wire n3355_o;
  wire [1:0] n3356_o;
  reg n3357_o;
  wire [1:0] n3358_o;
  reg n3359_o;
  wire n3360_o;
  wire n3361_o;
  assign tx_strb_o = tx_strb; //(module output)
  assign tx_o = tx; //(module output)
  /* ../../../vhdl/atbs_core_fixed_window/uart/rtl/uart_tx_ea.vhd:38:8  */
  assign tx = n3329_o; // (signal)
  /* ../../../vhdl/atbs_core_fixed_window/uart/rtl/uart_tx_ea.vhd:39:8  */
  assign tx_strb = n3344_q; // (signal)
  /* ../../../vhdl/atbs_core_fixed_window/uart/rtl/uart_tx_ea.vhd:40:8  */
  assign next_tx_strb = n3342_o; // (signal)
  /* ../../../vhdl/atbs_core_fixed_window/uart/rtl/uart_tx_ea.vhd:43:8  */
  assign transmit_counter_value = n3345_q; // (signal)
  /* ../../../vhdl/atbs_core_fixed_window/uart/rtl/uart_tx_ea.vhd:44:8  */
  assign next_transmit_counter_value = n3270_o; // (signal)
  /* ../../../vhdl/atbs_core_fixed_window/uart/rtl/uart_tx_ea.vhd:47:8  */
  assign baud_counter_value = n3346_q; // (signal)
  /* ../../../vhdl/atbs_core_fixed_window/uart/rtl/uart_tx_ea.vhd:48:8  */
  assign next_baud_counter_value = n3277_o; // (signal)
  /* ../../../vhdl/atbs_core_fixed_window/uart/rtl/uart_tx_ea.vhd:51:8  */
  assign tx_state = n3347_q; // (signal)
  /* ../../../vhdl/atbs_core_fixed_window/uart/rtl/uart_tx_ea.vhd:52:8  */
  assign next_tx_state = n3331_o; // (signal)
  /* ../../../vhdl/atbs_core_fixed_window/uart/rtl/uart_tx_ea.vhd:78:29  */
  assign n3264_o = tx_state == 3'b011;
  /* ../../../vhdl/atbs_core_fixed_window/uart/rtl/uart_tx_ea.vhd:79:47  */
  assign n3265_o = baud_counter_value == baudrate_adj_i;
  /* ../../../vhdl/atbs_core_fixed_window/uart/rtl/uart_tx_ea.vhd:80:87  */
  assign n3267_o = transmit_counter_value + 3'b001;
  /* ../../../vhdl/atbs_core_fixed_window/uart/rtl/uart_tx_ea.vhd:79:25  */
  assign n3268_o = n3265_o ? n3267_o : transmit_counter_value;
  /* ../../../vhdl/atbs_core_fixed_window/uart/rtl/uart_tx_ea.vhd:78:17  */
  assign n3270_o = n3264_o ? n3268_o : 3'b000;
  /* ../../../vhdl/atbs_core_fixed_window/uart/rtl/uart_tx_ea.vhd:93:39  */
  assign n3273_o = $unsigned(baud_counter_value) < $unsigned(baudrate_adj_i);
  /* ../../../vhdl/atbs_core_fixed_window/uart/rtl/uart_tx_ea.vhd:94:71  */
  assign n3275_o = baud_counter_value + 9'b000000001;
  /* ../../../vhdl/atbs_core_fixed_window/uart/rtl/uart_tx_ea.vhd:93:17  */
  assign n3277_o = n3273_o ? n3275_o : 9'b000000000;
  /* ../../../vhdl/atbs_core_fixed_window/uart/rtl/uart_tx_ea.vhd:111:63  */
  assign n3280_o = baud_counter_value == baudrate_adj_i;
  /* ../../../vhdl/atbs_core_fixed_window/uart/rtl/uart_tx_ea.vhd:111:41  */
  assign n3283_o = n3280_o ? 3'b010 : 3'b001;
  /* ../../../vhdl/atbs_core_fixed_window/uart/rtl/uart_tx_ea.vhd:110:33  */
  assign n3284_o = tx_start_strb_i ? n3283_o : tx_state;
  /* ../../../vhdl/atbs_core_fixed_window/uart/rtl/uart_tx_ea.vhd:108:25  */
  assign n3286_o = tx_state == 3'b000;
  /* ../../../vhdl/atbs_core_fixed_window/uart/rtl/uart_tx_ea.vhd:123:55  */
  assign n3287_o = baud_counter_value == baudrate_adj_i;
  /* ../../../vhdl/atbs_core_fixed_window/uart/rtl/uart_tx_ea.vhd:123:33  */
  assign n3290_o = n3287_o ? 1'b0 : 1'b1;
  /* ../../../vhdl/atbs_core_fixed_window/uart/rtl/uart_tx_ea.vhd:123:33  */
  assign n3293_o = n3287_o ? 3'b010 : tx_state;
  /* ../../../vhdl/atbs_core_fixed_window/uart/rtl/uart_tx_ea.vhd:121:25  */
  assign n3295_o = tx_state == 3'b001;
  /* ../../../vhdl/atbs_core_fixed_window/uart/rtl/uart_tx_ea.vhd:130:55  */
  assign n3296_o = baud_counter_value == baudrate_adj_i;
  /* ../../../vhdl/atbs_core_fixed_window/uart/rtl/uart_tx_ea.vhd:130:33  */
  assign n3298_o = n3296_o ? 3'b011 : tx_state;
  /* ../../../vhdl/atbs_core_fixed_window/uart/rtl/uart_tx_ea.vhd:128:25  */
  assign n3300_o = tx_state == 3'b010;
  /* ../../../vhdl/atbs_core_fixed_window/uart/rtl/uart_tx_ea.vhd:135:59  */
  assign n3302_o = $unsigned(transmit_counter_value) <= $unsigned(3'b111);
  /* ../../../vhdl/atbs_core_fixed_window/uart/rtl/uart_tx_ea.vhd:137:67  */
  assign n3307_o = transmit_counter_value == 3'b111;
  /* ../../../vhdl/atbs_core_fixed_window/uart/rtl/uart_tx_ea.vhd:137:113  */
  assign n3308_o = baud_counter_value == baudrate_adj_i;
  /* ../../../vhdl/atbs_core_fixed_window/uart/rtl/uart_tx_ea.vhd:137:90  */
  assign n3309_o = n3308_o & n3307_o;
  /* ../../../vhdl/atbs_core_fixed_window/uart/rtl/uart_tx_ea.vhd:135:33  */
  assign n3311_o = n3314_o ? 3'b100 : tx_state;
  /* ../../../vhdl/atbs_core_fixed_window/uart/rtl/uart_tx_ea.vhd:135:33  */
  assign n3313_o = n3302_o ? n3361_o : 1'bX;
  /* ../../../vhdl/atbs_core_fixed_window/uart/rtl/uart_tx_ea.vhd:135:33  */
  assign n3314_o = n3309_o & n3302_o;
  /* ../../../vhdl/atbs_core_fixed_window/uart/rtl/uart_tx_ea.vhd:134:25  */
  assign n3316_o = tx_state == 3'b011;
  /* ../../../vhdl/atbs_core_fixed_window/uart/rtl/uart_tx_ea.vhd:144:55  */
  assign n3317_o = baud_counter_value == baudrate_adj_i;
  /* ../../../vhdl/atbs_core_fixed_window/uart/rtl/uart_tx_ea.vhd:146:41  */
  assign n3320_o = tx_start_strb_i ? 3'b010 : 3'b000;
  /* ../../../vhdl/atbs_core_fixed_window/uart/rtl/uart_tx_ea.vhd:144:33  */
  assign n3321_o = n3317_o ? n3320_o : tx_state;
  /* ../../../vhdl/atbs_core_fixed_window/uart/rtl/uart_tx_ea.vhd:142:25  */
  assign n3323_o = tx_state == 3'b100;
  assign n3324_o = {n3323_o, n3316_o, n3300_o, n3295_o, n3286_o};
  /* ../../../vhdl/atbs_core_fixed_window/uart/rtl/uart_tx_ea.vhd:107:17  */
  always @*
    case (n3324_o)
      5'b10000: n3329_o = 1'b1;
      5'b01000: n3329_o = n3313_o;
      5'b00100: n3329_o = 1'b0;
      5'b00010: n3329_o = n3290_o;
      5'b00001: n3329_o = 1'b1;
      default: n3329_o = 1'bX;
    endcase
  /* ../../../vhdl/atbs_core_fixed_window/uart/rtl/uart_tx_ea.vhd:107:17  */
  always @*
    case (n3324_o)
      5'b10000: n3331_o = n3321_o;
      5'b01000: n3331_o = n3311_o;
      5'b00100: n3331_o = n3298_o;
      5'b00010: n3331_o = n3293_o;
      5'b00001: n3331_o = n3284_o;
      default: n3331_o = tx_state;
    endcase
  /* ../../../vhdl/atbs_core_fixed_window/uart/rtl/uart_tx_ea.vhd:158:37  */
  assign n3335_o = tx_state == 3'b100;
  /* ../../../vhdl/atbs_core_fixed_window/uart/rtl/uart_tx_ea.vhd:158:66  */
  assign n3337_o = next_tx_state == 3'b010;
  /* ../../../vhdl/atbs_core_fixed_window/uart/rtl/uart_tx_ea.vhd:158:94  */
  assign n3339_o = next_tx_state == 3'b000;
  /* ../../../vhdl/atbs_core_fixed_window/uart/rtl/uart_tx_ea.vhd:158:77  */
  assign n3340_o = n3337_o | n3339_o;
  /* ../../../vhdl/atbs_core_fixed_window/uart/rtl/uart_tx_ea.vhd:158:47  */
  assign n3341_o = n3340_o & n3335_o;
  /* ../../../vhdl/atbs_core_fixed_window/uart/rtl/uart_tx_ea.vhd:158:23  */
  assign n3342_o = n3341_o ? 1'b1 : 1'b0;
  /* ../../../vhdl/atbs_core_fixed_window/uart/rtl/uart_tx_ea.vhd:63:17  */
  always @(posedge clock_i or posedge reset_i)
    if (reset_i)
      n3344_q <= 1'b0;
    else
      n3344_q <= next_tx_strb;
  /* ../../../vhdl/atbs_core_fixed_window/uart/rtl/uart_tx_ea.vhd:63:17  */
  always @(posedge clock_i or posedge reset_i)
    if (reset_i)
      n3345_q <= 3'b000;
    else
      n3345_q <= next_transmit_counter_value;
  /* ../../../vhdl/atbs_core_fixed_window/uart/rtl/uart_tx_ea.vhd:63:17  */
  always @(posedge clock_i or posedge reset_i)
    if (reset_i)
      n3346_q <= 9'b000000000;
    else
      n3346_q <= next_baud_counter_value;
  /* ../../../vhdl/atbs_core_fixed_window/uart/rtl/uart_tx_ea.vhd:63:17  */
  always @(posedge clock_i or posedge reset_i)
    if (reset_i)
      n3347_q <= 3'b000;
    else
      n3347_q <= next_tx_state;
  /* ../../../vhdl/atbs_core_fixed_window/uart/rtl/uart_tx_ea.vhd:25:17  */
  assign n3348_o = data_i[0]; // extract
  /* ../../../vhdl/atbs_core_fixed_window/uart/rtl/uart_tx_ea.vhd:24:5  */
  assign n3349_o = data_i[1]; // extract
  assign n3350_o = data_i[2]; // extract
  assign n3351_o = data_i[3]; // extract
  /* ../../../vhdl/atbs_core_fixed_window/uart/rtl/uart_tx_ea.vhd:136:54  */
  assign n3352_o = data_i[4]; // extract
  assign n3353_o = data_i[5]; // extract
  /* ../../../vhdl/atbs_core_fixed_window/uart/rtl/uart_tx_ea.vhd:101:9  */
  assign n3354_o = data_i[6]; // extract
  assign n3355_o = data_i[7]; // extract
  /* ../../../vhdl/atbs_core_fixed_window/uart/rtl/uart_tx_ea.vhd:136:53  */
  assign n3356_o = transmit_counter_value[1:0]; // extract
  /* ../../../vhdl/atbs_core_fixed_window/uart/rtl/uart_tx_ea.vhd:136:53  */
  always @*
    case (n3356_o)
      2'b00: n3357_o = n3348_o;
      2'b01: n3357_o = n3349_o;
      2'b10: n3357_o = n3350_o;
      2'b11: n3357_o = n3351_o;
    endcase
  /* ../../../vhdl/atbs_core_fixed_window/uart/rtl/uart_tx_ea.vhd:136:53  */
  assign n3358_o = transmit_counter_value[1:0]; // extract
  /* ../../../vhdl/atbs_core_fixed_window/uart/rtl/uart_tx_ea.vhd:136:53  */
  always @*
    case (n3358_o)
      2'b00: n3359_o = n3352_o;
      2'b01: n3359_o = n3353_o;
      2'b10: n3359_o = n3354_o;
      2'b11: n3359_o = n3355_o;
    endcase
  /* ../../../vhdl/atbs_core_fixed_window/uart/rtl/uart_tx_ea.vhd:136:53  */
  assign n3360_o = transmit_counter_value[2]; // extract
  /* ../../../vhdl/atbs_core_fixed_window/uart/rtl/uart_tx_ea.vhd:136:53  */
  assign n3361_o = n3360_o ? n3359_o : n3357_o;
endmodule

module weyls_discrepancy_8_3_6
  (input  clock_i,
   input  reset_i,
   input  [29:0] spikes_i,
   input  spikes_strb_i,
   output [2:0] weylsd_o,
   output weylsd_strb_o);
  wire [5:0] buf_reg;
  wire [5:0] next_buf_reg;
  wire [1:0] sync_weylsd_strb;
  wire next_weylsd_strb;
  wire [95:0] thermocodes;
  wire [95:0] buf_thermocodes;
  wire [5:0] orresult;
  wire [2:0] neg_orresult;
  wire [95:0] temp_orresult;
  wire [2:0] weylsd;
  wire [2:0] next_weylsd;
  wire [2:0] weylsd_neg;
  wire [2:0] weylsd_pos;
  wire n3033_o;
  wire [1:0] n3035_o;
  wire [5:0] gen_spike_2_tc_n1_spike_2_tc_thermo_o;
  wire [1:0] n3046_o;
  wire [5:0] n3047_o;
  wire [5:0] gen_spike_2_tc_n2_spike_2_tc_thermo_o;
  wire [1:0] n3049_o;
  wire [5:0] n3050_o;
  wire [5:0] gen_spike_2_tc_n3_spike_2_tc_thermo_o;
  wire [1:0] n3052_o;
  wire [5:0] n3053_o;
  wire [5:0] gen_spike_2_tc_n4_spike_2_tc_thermo_o;
  wire [1:0] n3055_o;
  wire [5:0] n3056_o;
  wire [5:0] gen_spike_2_tc_n5_spike_2_tc_thermo_o;
  wire [1:0] n3058_o;
  wire [5:0] n3059_o;
  wire [5:0] gen_spike_2_tc_n6_spike_2_tc_thermo_o;
  wire [1:0] n3061_o;
  wire [5:0] n3062_o;
  wire [5:0] gen_spike_2_tc_n7_spike_2_tc_thermo_o;
  wire [1:0] n3064_o;
  wire [5:0] n3065_o;
  wire [5:0] gen_spike_2_tc_n8_spike_2_tc_thermo_o;
  wire [1:0] n3067_o;
  wire [5:0] n3068_o;
  wire [5:0] gen_spike_2_tc_n9_spike_2_tc_thermo_o;
  wire [1:0] n3070_o;
  wire [5:0] n3071_o;
  wire [5:0] gen_spike_2_tc_n10_spike_2_tc_thermo_o;
  wire [1:0] n3073_o;
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
  assign next_buf_reg = n3092_o; // (signal)
  /* ../../../vhdl/atbs_core_fixed_window/adaptive_threshold_control/Weyls-Discrepancy/rtl/weyls_discrepancy_ea.vhd:63:8  */
  assign sync_weylsd_strb = n3237_q; // (signal)
  /* ../../../vhdl/atbs_core_fixed_window/adaptive_threshold_control/Weyls-Discrepancy/rtl/weyls_discrepancy_ea.vhd:64:8  */
  assign next_weylsd_strb = spikes_strb_i; // (signal)
  /* ../../../vhdl/atbs_core_fixed_window/adaptive_threshold_control/Weyls-Discrepancy/rtl/weyls_discrepancy_ea.vhd:66:8  */
  assign thermocodes = n3238_o; // (signal)
  /* ../../../vhdl/atbs_core_fixed_window/adaptive_threshold_control/Weyls-Discrepancy/rtl/weyls_discrepancy_ea.vhd:67:8  */
  assign buf_thermocodes = n3239_o; // (signal)
  /* ../../../vhdl/atbs_core_fixed_window/adaptive_threshold_control/Weyls-Discrepancy/rtl/weyls_discrepancy_ea.vhd:69:8  */
  assign orresult = n3223_o; // (signal)
  /* ../../../vhdl/atbs_core_fixed_window/adaptive_threshold_control/Weyls-Discrepancy/rtl/weyls_discrepancy_ea.vhd:70:8  */
  assign neg_orresult = n3240_o; // (signal)
  /* ../../../vhdl/atbs_core_fixed_window/adaptive_threshold_control/Weyls-Discrepancy/rtl/weyls_discrepancy_ea.vhd:71:8  */
  assign temp_orresult = n3241_o; // (signal)
  /* ../../../vhdl/atbs_core_fixed_window/adaptive_threshold_control/Weyls-Discrepancy/rtl/weyls_discrepancy_ea.vhd:73:8  */
  assign weylsd = n3242_q; // (signal)
  /* ../../../vhdl/atbs_core_fixed_window/adaptive_threshold_control/Weyls-Discrepancy/rtl/weyls_discrepancy_ea.vhd:74:8  */
  assign next_weylsd = n3234_o; // (signal)
  /* ../../../vhdl/atbs_core_fixed_window/adaptive_threshold_control/Weyls-Discrepancy/rtl/weyls_discrepancy_ea.vhd:75:8  */
  assign weylsd_neg = priority_encoder_0_bin_o; // (signal)
  /* ../../../vhdl/atbs_core_fixed_window/adaptive_threshold_control/Weyls-Discrepancy/rtl/weyls_discrepancy_ea.vhd:76:8  */
  assign weylsd_pos = priority_encoder_1_bin_o; // (signal)
  /* ../../../vhdl/atbs_core_fixed_window/adaptive_threshold_control/Weyls-Discrepancy/rtl/weyls_discrepancy_ea.vhd:97:48  */
  assign n3033_o = sync_weylsd_strb[0]; // extract
  assign n3035_o = {n3033_o, next_weylsd_strb};
  /* ../../../vhdl/atbs_core_fixed_window/adaptive_threshold_control/Weyls-Discrepancy/rtl/weyls_discrepancy_ea.vhd:107:5  */
  spike_2_thermocode_6 gen_spike_2_tc_n1_spike_2_tc (
    .spike_i(n3046_o),
    .thermo_i(n3047_o),
    .thermo_o(gen_spike_2_tc_n1_spike_2_tc_thermo_o));
  /* ../../../vhdl/atbs_core_fixed_window/adaptive_threshold_control/Weyls-Discrepancy/rtl/weyls_discrepancy_ea.vhd:112:30  */
  assign n3046_o = spikes_i[29:28]; // extract
  /* ../../../vhdl/atbs_core_fixed_window/adaptive_threshold_control/Weyls-Discrepancy/rtl/weyls_discrepancy_ea.vhd:113:33  */
  assign n3047_o = thermocodes[5:0]; // extract
  /* ../../../vhdl/atbs_core_fixed_window/adaptive_threshold_control/Weyls-Discrepancy/rtl/weyls_discrepancy_ea.vhd:107:5  */
  spike_2_thermocode_6 gen_spike_2_tc_n2_spike_2_tc (
    .spike_i(n3049_o),
    .thermo_i(n3050_o),
    .thermo_o(gen_spike_2_tc_n2_spike_2_tc_thermo_o));
  /* ../../../vhdl/atbs_core_fixed_window/adaptive_threshold_control/Weyls-Discrepancy/rtl/weyls_discrepancy_ea.vhd:112:30  */
  assign n3049_o = spikes_i[27:26]; // extract
  /* ../../../vhdl/atbs_core_fixed_window/adaptive_threshold_control/Weyls-Discrepancy/rtl/weyls_discrepancy_ea.vhd:113:33  */
  assign n3050_o = thermocodes[11:6]; // extract
  /* ../../../vhdl/atbs_core_fixed_window/adaptive_threshold_control/Weyls-Discrepancy/rtl/weyls_discrepancy_ea.vhd:107:5  */
  spike_2_thermocode_6 gen_spike_2_tc_n3_spike_2_tc (
    .spike_i(n3052_o),
    .thermo_i(n3053_o),
    .thermo_o(gen_spike_2_tc_n3_spike_2_tc_thermo_o));
  /* ../../../vhdl/atbs_core_fixed_window/adaptive_threshold_control/Weyls-Discrepancy/rtl/weyls_discrepancy_ea.vhd:112:30  */
  assign n3052_o = spikes_i[25:24]; // extract
  /* ../../../vhdl/atbs_core_fixed_window/adaptive_threshold_control/Weyls-Discrepancy/rtl/weyls_discrepancy_ea.vhd:113:33  */
  assign n3053_o = thermocodes[17:12]; // extract
  /* ../../../vhdl/atbs_core_fixed_window/adaptive_threshold_control/Weyls-Discrepancy/rtl/weyls_discrepancy_ea.vhd:107:5  */
  spike_2_thermocode_6 gen_spike_2_tc_n4_spike_2_tc (
    .spike_i(n3055_o),
    .thermo_i(n3056_o),
    .thermo_o(gen_spike_2_tc_n4_spike_2_tc_thermo_o));
  /* ../../../vhdl/atbs_core_fixed_window/adaptive_threshold_control/Weyls-Discrepancy/rtl/weyls_discrepancy_ea.vhd:112:30  */
  assign n3055_o = spikes_i[23:22]; // extract
  /* ../../../vhdl/atbs_core_fixed_window/adaptive_threshold_control/Weyls-Discrepancy/rtl/weyls_discrepancy_ea.vhd:113:33  */
  assign n3056_o = thermocodes[23:18]; // extract
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
  assign n3093_o = buf_thermocodes[95:54]; // extract
  assign n3094_o = buf_thermocodes[47:0]; // extract
  /* ../../../vhdl/atbs_core_fixed_window/adaptive_threshold_control/Weyls-Discrepancy/rtl/weyls_discrepancy_ea.vhd:136:12  */
  always @*
    eval_orresult_offset_comp = n3225_o; // (isignal)
  initial
    eval_orresult_offset_comp = 96'bX;
  /* ../../../vhdl/atbs_core_fixed_window/adaptive_threshold_control/Weyls-Discrepancy/rtl/weyls_discrepancy_ea.vhd:138:71  */
  assign n3098_o = thermocodes[2:0]; // extract
  /* ../../../vhdl/atbs_core_fixed_window/adaptive_threshold_control/Weyls-Discrepancy/rtl/weyls_discrepancy_ea.vhd:138:53  */
  assign n3099_o = ~n3098_o;
  /* ../../../vhdl/atbs_core_fixed_window/adaptive_threshold_control/Weyls-Discrepancy/rtl/weyls_discrepancy_ea.vhd:139:77  */
  assign n3100_o = thermocodes[5:3]; // extract
  assign n3101_o = eval_orresult_offset_comp[95:6]; // extract
  assign n3102_o = {n3101_o, n3100_o, n3099_o};
  /* ../../../vhdl/atbs_core_fixed_window/adaptive_threshold_control/Weyls-Discrepancy/rtl/weyls_discrepancy_ea.vhd:140:36  */
  assign n3103_o = n3102_o[5:0]; // extract
  /* ../../../vhdl/atbs_core_fixed_window/adaptive_threshold_control/Weyls-Discrepancy/rtl/weyls_discrepancy_ea.vhd:146:73  */
  assign n3104_o = thermocodes[8:6]; // extract
  /* ../../../vhdl/atbs_core_fixed_window/adaptive_threshold_control/Weyls-Discrepancy/rtl/weyls_discrepancy_ea.vhd:146:55  */
  assign n3105_o = ~n3104_o;
  /* ../../../vhdl/atbs_core_fixed_window/adaptive_threshold_control/Weyls-Discrepancy/rtl/weyls_discrepancy_ea.vhd:147:79  */
  assign n3106_o = thermocodes[11:9]; // extract
  /* ../../../vhdl/atbs_core_fixed_window/adaptive_threshold_control/Weyls-Discrepancy/rtl/weyls_discrepancy_ea.vhd:148:40  */
  assign n3107_o = temp_orresult[5:0]; // extract
  assign n3108_o = eval_orresult_offset_comp[95:12]; // extract
  assign n3109_o = {n3108_o, n3106_o, n3105_o, n3100_o, n3099_o};
  /* ../../../vhdl/atbs_core_fixed_window/adaptive_threshold_control/Weyls-Discrepancy/rtl/weyls_discrepancy_ea.vhd:148:60  */
  assign n3110_o = n3109_o[11:6]; // extract
  /* ../../../vhdl/atbs_core_fixed_window/adaptive_threshold_control/Weyls-Discrepancy/rtl/weyls_discrepancy_ea.vhd:148:46  */
  assign n3111_o = n3107_o | n3110_o;
  /* ../../../vhdl/atbs_core_fixed_window/adaptive_threshold_control/Weyls-Discrepancy/rtl/weyls_discrepancy_ea.vhd:146:73  */
  assign n3112_o = thermocodes[14:12]; // extract
  /* ../../../vhdl/atbs_core_fixed_window/adaptive_threshold_control/Weyls-Discrepancy/rtl/weyls_discrepancy_ea.vhd:146:55  */
  assign n3113_o = ~n3112_o;
  /* ../../../vhdl/atbs_core_fixed_window/adaptive_threshold_control/Weyls-Discrepancy/rtl/weyls_discrepancy_ea.vhd:147:79  */
  assign n3114_o = thermocodes[17:15]; // extract
  /* ../../../vhdl/atbs_core_fixed_window/adaptive_threshold_control/Weyls-Discrepancy/rtl/weyls_discrepancy_ea.vhd:148:40  */
  assign n3115_o = temp_orresult[11:6]; // extract
  assign n3116_o = eval_orresult_offset_comp[95:18]; // extract
  assign n3117_o = {n3116_o, n3114_o, n3113_o, n3106_o, n3105_o, n3100_o, n3099_o};
  /* ../../../vhdl/atbs_core_fixed_window/adaptive_threshold_control/Weyls-Discrepancy/rtl/weyls_discrepancy_ea.vhd:148:60  */
  assign n3118_o = n3117_o[17:12]; // extract
  /* ../../../vhdl/atbs_core_fixed_window/adaptive_threshold_control/Weyls-Discrepancy/rtl/weyls_discrepancy_ea.vhd:148:46  */
  assign n3119_o = n3115_o | n3118_o;
  /* ../../../vhdl/atbs_core_fixed_window/adaptive_threshold_control/Weyls-Discrepancy/rtl/weyls_discrepancy_ea.vhd:146:73  */
  assign n3120_o = thermocodes[20:18]; // extract
  /* ../../../vhdl/atbs_core_fixed_window/adaptive_threshold_control/Weyls-Discrepancy/rtl/weyls_discrepancy_ea.vhd:146:55  */
  assign n3121_o = ~n3120_o;
  /* ../../../vhdl/atbs_core_fixed_window/adaptive_threshold_control/Weyls-Discrepancy/rtl/weyls_discrepancy_ea.vhd:147:79  */
  assign n3122_o = thermocodes[23:21]; // extract
  /* ../../../vhdl/atbs_core_fixed_window/adaptive_threshold_control/Weyls-Discrepancy/rtl/weyls_discrepancy_ea.vhd:148:40  */
  assign n3123_o = temp_orresult[17:12]; // extract
  assign n3124_o = eval_orresult_offset_comp[95:24]; // extract
  assign n3125_o = {n3124_o, n3122_o, n3121_o, n3114_o, n3113_o, n3106_o, n3105_o, n3100_o, n3099_o};
  /* ../../../vhdl/atbs_core_fixed_window/adaptive_threshold_control/Weyls-Discrepancy/rtl/weyls_discrepancy_ea.vhd:148:60  */
  assign n3126_o = n3125_o[23:18]; // extract
  /* ../../../vhdl/atbs_core_fixed_window/adaptive_threshold_control/Weyls-Discrepancy/rtl/weyls_discrepancy_ea.vhd:148:46  */
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
  assign n3154_o = thermocodes[47:45]; // extract
  /* ../../../vhdl/atbs_core_fixed_window/adaptive_threshold_control/Weyls-Discrepancy/rtl/weyls_discrepancy_ea.vhd:148:40  */
  assign n3155_o = temp_orresult[41:36]; // extract
  assign n3156_o = eval_orresult_offset_comp[95:48]; // extract
  assign n3157_o = {n3156_o, n3154_o, n3153_o, n3146_o, n3145_o, n3138_o, n3137_o, n3130_o, n3129_o, n3122_o, n3121_o, n3114_o, n3113_o, n3106_o, n3105_o, n3100_o, n3099_o};
  /* ../../../vhdl/atbs_core_fixed_window/adaptive_threshold_control/Weyls-Discrepancy/rtl/weyls_discrepancy_ea.vhd:148:60  */
  assign n3158_o = n3157_o[47:42]; // extract
  /* ../../../vhdl/atbs_core_fixed_window/adaptive_threshold_control/Weyls-Discrepancy/rtl/weyls_discrepancy_ea.vhd:148:46  */
  assign n3159_o = n3155_o | n3158_o;
  /* ../../../vhdl/atbs_core_fixed_window/adaptive_threshold_control/Weyls-Discrepancy/rtl/weyls_discrepancy_ea.vhd:146:73  */
  assign n3160_o = thermocodes[50:48]; // extract
  /* ../../../vhdl/atbs_core_fixed_window/adaptive_threshold_control/Weyls-Discrepancy/rtl/weyls_discrepancy_ea.vhd:146:55  */
  assign n3161_o = ~n3160_o;
  /* ../../../vhdl/atbs_core_fixed_window/adaptive_threshold_control/Weyls-Discrepancy/rtl/weyls_discrepancy_ea.vhd:147:79  */
  assign n3162_o = thermocodes[53:51]; // extract
  /* ../../../vhdl/atbs_core_fixed_window/adaptive_threshold_control/Weyls-Discrepancy/rtl/weyls_discrepancy_ea.vhd:148:40  */
  assign n3163_o = temp_orresult[47:42]; // extract
  assign n3164_o = eval_orresult_offset_comp[95:54]; // extract
  assign n3165_o = {n3164_o, n3162_o, n3161_o, n3154_o, n3153_o, n3146_o, n3145_o, n3138_o, n3137_o, n3130_o, n3129_o, n3122_o, n3121_o, n3114_o, n3113_o, n3106_o, n3105_o, n3100_o, n3099_o};
  /* ../../../vhdl/atbs_core_fixed_window/adaptive_threshold_control/Weyls-Discrepancy/rtl/weyls_discrepancy_ea.vhd:148:60  */
  assign n3166_o = n3165_o[53:48]; // extract
  /* ../../../vhdl/atbs_core_fixed_window/adaptive_threshold_control/Weyls-Discrepancy/rtl/weyls_discrepancy_ea.vhd:148:46  */
  assign n3167_o = n3163_o | n3166_o;
  /* ../../../vhdl/atbs_core_fixed_window/adaptive_threshold_control/Weyls-Discrepancy/rtl/weyls_discrepancy_ea.vhd:146:73  */
  assign n3168_o = thermocodes[56:54]; // extract
  /* ../../../vhdl/atbs_core_fixed_window/adaptive_threshold_control/Weyls-Discrepancy/rtl/weyls_discrepancy_ea.vhd:146:55  */
  assign n3169_o = ~n3168_o;
  /* ../../../vhdl/atbs_core_fixed_window/adaptive_threshold_control/Weyls-Discrepancy/rtl/weyls_discrepancy_ea.vhd:147:79  */
  assign n3170_o = thermocodes[59:57]; // extract
  /* ../../../vhdl/atbs_core_fixed_window/adaptive_threshold_control/Weyls-Discrepancy/rtl/weyls_discrepancy_ea.vhd:148:40  */
  assign n3171_o = temp_orresult[53:48]; // extract
  assign n3172_o = eval_orresult_offset_comp[95:60]; // extract
  assign n3173_o = {n3172_o, n3170_o, n3169_o, n3162_o, n3161_o, n3154_o, n3153_o, n3146_o, n3145_o, n3138_o, n3137_o, n3130_o, n3129_o, n3122_o, n3121_o, n3114_o, n3113_o, n3106_o, n3105_o, n3100_o, n3099_o};
  /* ../../../vhdl/atbs_core_fixed_window/adaptive_threshold_control/Weyls-Discrepancy/rtl/weyls_discrepancy_ea.vhd:148:60  */
  assign n3174_o = n3173_o[59:54]; // extract
  /* ../../../vhdl/atbs_core_fixed_window/adaptive_threshold_control/Weyls-Discrepancy/rtl/weyls_discrepancy_ea.vhd:148:46  */
  assign n3175_o = n3171_o | n3174_o;
  /* ../../../vhdl/atbs_core_fixed_window/adaptive_threshold_control/Weyls-Discrepancy/rtl/weyls_discrepancy_ea.vhd:146:73  */
  assign n3176_o = thermocodes[62:60]; // extract
  /* ../../../vhdl/atbs_core_fixed_window/adaptive_threshold_control/Weyls-Discrepancy/rtl/weyls_discrepancy_ea.vhd:146:55  */
  assign n3177_o = ~n3176_o;
  /* ../../../vhdl/atbs_core_fixed_window/adaptive_threshold_control/Weyls-Discrepancy/rtl/weyls_discrepancy_ea.vhd:147:79  */
  assign n3178_o = thermocodes[65:63]; // extract
  /* ../../../vhdl/atbs_core_fixed_window/adaptive_threshold_control/Weyls-Discrepancy/rtl/weyls_discrepancy_ea.vhd:148:40  */
  assign n3179_o = temp_orresult[59:54]; // extract
  assign n3180_o = eval_orresult_offset_comp[95:66]; // extract
  assign n3181_o = {n3180_o, n3178_o, n3177_o, n3170_o, n3169_o, n3162_o, n3161_o, n3154_o, n3153_o, n3146_o, n3145_o, n3138_o, n3137_o, n3130_o, n3129_o, n3122_o, n3121_o, n3114_o, n3113_o, n3106_o, n3105_o, n3100_o, n3099_o};
  /* ../../../vhdl/atbs_core_fixed_window/adaptive_threshold_control/Weyls-Discrepancy/rtl/weyls_discrepancy_ea.vhd:148:60  */
  assign n3182_o = n3181_o[65:60]; // extract
  /* ../../../vhdl/atbs_core_fixed_window/adaptive_threshold_control/Weyls-Discrepancy/rtl/weyls_discrepancy_ea.vhd:148:46  */
  assign n3183_o = n3179_o | n3182_o;
  /* ../../../vhdl/atbs_core_fixed_window/adaptive_threshold_control/Weyls-Discrepancy/rtl/weyls_discrepancy_ea.vhd:146:73  */
  assign n3184_o = thermocodes[68:66]; // extract
  /* ../../../vhdl/atbs_core_fixed_window/adaptive_threshold_control/Weyls-Discrepancy/rtl/weyls_discrepancy_ea.vhd:146:55  */
  assign n3185_o = ~n3184_o;
  /* ../../../vhdl/atbs_core_fixed_window/adaptive_threshold_control/Weyls-Discrepancy/rtl/weyls_discrepancy_ea.vhd:147:79  */
  assign n3186_o = thermocodes[71:69]; // extract
  /* ../../../vhdl/atbs_core_fixed_window/adaptive_threshold_control/Weyls-Discrepancy/rtl/weyls_discrepancy_ea.vhd:148:40  */
  assign n3187_o = temp_orresult[65:60]; // extract
  assign n3188_o = eval_orresult_offset_comp[95:72]; // extract
  assign n3189_o = {n3188_o, n3186_o, n3185_o, n3178_o, n3177_o, n3170_o, n3169_o, n3162_o, n3161_o, n3154_o, n3153_o, n3146_o, n3145_o, n3138_o, n3137_o, n3130_o, n3129_o, n3122_o, n3121_o, n3114_o, n3113_o, n3106_o, n3105_o, n3100_o, n3099_o};
  /* ../../../vhdl/atbs_core_fixed_window/adaptive_threshold_control/Weyls-Discrepancy/rtl/weyls_discrepancy_ea.vhd:148:60  */
  assign n3190_o = n3189_o[71:66]; // extract
  /* ../../../vhdl/atbs_core_fixed_window/adaptive_threshold_control/Weyls-Discrepancy/rtl/weyls_discrepancy_ea.vhd:148:46  */
  assign n3191_o = n3187_o | n3190_o;
  /* ../../../vhdl/atbs_core_fixed_window/adaptive_threshold_control/Weyls-Discrepancy/rtl/weyls_discrepancy_ea.vhd:146:73  */
  assign n3192_o = thermocodes[74:72]; // extract
  /* ../../../vhdl/atbs_core_fixed_window/adaptive_threshold_control/Weyls-Discrepancy/rtl/weyls_discrepancy_ea.vhd:146:55  */
  assign n3193_o = ~n3192_o;
  /* ../../../vhdl/atbs_core_fixed_window/adaptive_threshold_control/Weyls-Discrepancy/rtl/weyls_discrepancy_ea.vhd:147:79  */
  assign n3194_o = thermocodes[77:75]; // extract
  /* ../../../vhdl/atbs_core_fixed_window/adaptive_threshold_control/Weyls-Discrepancy/rtl/weyls_discrepancy_ea.vhd:148:40  */
  assign n3195_o = temp_orresult[71:66]; // extract
  assign n3196_o = eval_orresult_offset_comp[95:78]; // extract
  assign n3197_o = {n3196_o, n3194_o, n3193_o, n3186_o, n3185_o, n3178_o, n3177_o, n3170_o, n3169_o, n3162_o, n3161_o, n3154_o, n3153_o, n3146_o, n3145_o, n3138_o, n3137_o, n3130_o, n3129_o, n3122_o, n3121_o, n3114_o, n3113_o, n3106_o, n3105_o, n3100_o, n3099_o};
  /* ../../../vhdl/atbs_core_fixed_window/adaptive_threshold_control/Weyls-Discrepancy/rtl/weyls_discrepancy_ea.vhd:148:60  */
  assign n3198_o = n3197_o[77:72]; // extract
  /* ../../../vhdl/atbs_core_fixed_window/adaptive_threshold_control/Weyls-Discrepancy/rtl/weyls_discrepancy_ea.vhd:148:46  */
  assign n3199_o = n3195_o | n3198_o;
  /* ../../../vhdl/atbs_core_fixed_window/adaptive_threshold_control/Weyls-Discrepancy/rtl/weyls_discrepancy_ea.vhd:146:73  */
  assign n3200_o = thermocodes[80:78]; // extract
  /* ../../../vhdl/atbs_core_fixed_window/adaptive_threshold_control/Weyls-Discrepancy/rtl/weyls_discrepancy_ea.vhd:146:55  */
  assign n3201_o = ~n3200_o;
  /* ../../../vhdl/atbs_core_fixed_window/adaptive_threshold_control/Weyls-Discrepancy/rtl/weyls_discrepancy_ea.vhd:147:79  */
  assign n3202_o = thermocodes[83:81]; // extract
  /* ../../../vhdl/atbs_core_fixed_window/adaptive_threshold_control/Weyls-Discrepancy/rtl/weyls_discrepancy_ea.vhd:148:40  */
  assign n3203_o = temp_orresult[77:72]; // extract
  assign n3204_o = eval_orresult_offset_comp[95:84]; // extract
  assign n3205_o = {n3204_o, n3202_o, n3201_o, n3194_o, n3193_o, n3186_o, n3185_o, n3178_o, n3177_o, n3170_o, n3169_o, n3162_o, n3161_o, n3154_o, n3153_o, n3146_o, n3145_o, n3138_o, n3137_o, n3130_o, n3129_o, n3122_o, n3121_o, n3114_o, n3113_o, n3106_o, n3105_o, n3100_o, n3099_o};
  /* ../../../vhdl/atbs_core_fixed_window/adaptive_threshold_control/Weyls-Discrepancy/rtl/weyls_discrepancy_ea.vhd:148:60  */
  assign n3206_o = n3205_o[83:78]; // extract
  /* ../../../vhdl/atbs_core_fixed_window/adaptive_threshold_control/Weyls-Discrepancy/rtl/weyls_discrepancy_ea.vhd:148:46  */
  assign n3207_o = n3203_o | n3206_o;
  /* ../../../vhdl/atbs_core_fixed_window/adaptive_threshold_control/Weyls-Discrepancy/rtl/weyls_discrepancy_ea.vhd:146:73  */
  assign n3208_o = thermocodes[86:84]; // extract
  /* ../../../vhdl/atbs_core_fixed_window/adaptive_threshold_control/Weyls-Discrepancy/rtl/weyls_discrepancy_ea.vhd:146:55  */
  assign n3209_o = ~n3208_o;
  /* ../../../vhdl/atbs_core_fixed_window/adaptive_threshold_control/Weyls-Discrepancy/rtl/weyls_discrepancy_ea.vhd:147:79  */
  assign n3210_o = thermocodes[89:87]; // extract
  /* ../../../vhdl/atbs_core_fixed_window/adaptive_threshold_control/Weyls-Discrepancy/rtl/weyls_discrepancy_ea.vhd:148:40  */
  assign n3211_o = temp_orresult[83:78]; // extract
  assign n3212_o = eval_orresult_offset_comp[95:90]; // extract
  assign n3213_o = {n3212_o, n3210_o, n3209_o, n3202_o, n3201_o, n3194_o, n3193_o, n3186_o, n3185_o, n3178_o, n3177_o, n3170_o, n3169_o, n3162_o, n3161_o, n3154_o, n3153_o, n3146_o, n3145_o, n3138_o, n3137_o, n3130_o, n3129_o, n3122_o, n3121_o, n3114_o, n3113_o, n3106_o, n3105_o, n3100_o, n3099_o};
  /* ../../../vhdl/atbs_core_fixed_window/adaptive_threshold_control/Weyls-Discrepancy/rtl/weyls_discrepancy_ea.vhd:148:60  */
  assign n3214_o = n3213_o[89:84]; // extract
  /* ../../../vhdl/atbs_core_fixed_window/adaptive_threshold_control/Weyls-Discrepancy/rtl/weyls_discrepancy_ea.vhd:148:46  */
  assign n3215_o = n3211_o | n3214_o;
  /* ../../../vhdl/atbs_core_fixed_window/adaptive_threshold_control/Weyls-Discrepancy/rtl/weyls_discrepancy_ea.vhd:146:73  */
  assign n3216_o = thermocodes[92:90]; // extract
  /* ../../../vhdl/atbs_core_fixed_window/adaptive_threshold_control/Weyls-Discrepancy/rtl/weyls_discrepancy_ea.vhd:146:55  */
  assign n3217_o = ~n3216_o;
  /* ../../../vhdl/atbs_core_fixed_window/adaptive_threshold_control/Weyls-Discrepancy/rtl/weyls_discrepancy_ea.vhd:147:79  */
  assign n3218_o = thermocodes[95:93]; // extract
  /* ../../../vhdl/atbs_core_fixed_window/adaptive_threshold_control/Weyls-Discrepancy/rtl/weyls_discrepancy_ea.vhd:148:40  */
  assign n3219_o = temp_orresult[89:84]; // extract
  assign n3220_o = {n3218_o, n3217_o, n3210_o, n3209_o, n3202_o, n3201_o, n3194_o, n3193_o, n3186_o, n3185_o, n3178_o, n3177_o, n3170_o, n3169_o, n3162_o, n3161_o, n3154_o, n3153_o, n3146_o, n3145_o, n3138_o, n3137_o, n3130_o, n3129_o, n3122_o, n3121_o, n3114_o, n3113_o, n3106_o, n3105_o, n3100_o, n3099_o};
  /* ../../../vhdl/atbs_core_fixed_window/adaptive_threshold_control/Weyls-Discrepancy/rtl/weyls_discrepancy_ea.vhd:148:60  */
  assign n3221_o = n3220_o[95:90]; // extract
  /* ../../../vhdl/atbs_core_fixed_window/adaptive_threshold_control/Weyls-Discrepancy/rtl/weyls_discrepancy_ea.vhd:148:46  */
  assign n3222_o = n3219_o | n3221_o;
  /* ../../../vhdl/atbs_core_fixed_window/adaptive_threshold_control/Weyls-Discrepancy/rtl/weyls_discrepancy_ea.vhd:151:30  */
  assign n3223_o = temp_orresult[95:90]; // extract
  assign n3225_o = {n3218_o, n3217_o, n3210_o, n3209_o, n3202_o, n3201_o, n3194_o, n3193_o, n3186_o, n3185_o, n3178_o, n3177_o, n3170_o, n3169_o, n3162_o, n3161_o, n3154_o, n3153_o, n3146_o, n3145_o, n3138_o, n3137_o, n3130_o, n3129_o, n3122_o, n3121_o, n3114_o, n3113_o, n3106_o, n3105_o, n3100_o, n3099_o};
  /* ../../../vhdl/atbs_core_fixed_window/adaptive_threshold_control/Weyls-Discrepancy/rtl/weyls_discrepancy_ea.vhd:160:54  */
  assign n3227_o = orresult[0]; // extract
  /* ../../../vhdl/atbs_core_fixed_window/adaptive_threshold_control/Weyls-Discrepancy/rtl/weyls_discrepancy_ea.vhd:160:54  */
  assign n3228_o = orresult[1]; // extract
  /* ../../../vhdl/atbs_core_fixed_window/adaptive_threshold_control/Weyls-Discrepancy/rtl/weyls_discrepancy_ea.vhd:160:54  */
  assign n3229_o = orresult[2]; // extract
  /* ../../../vhdl/atbs_core_fixed_window/adaptive_threshold_control/Weyls-Discrepancy/rtl/weyls_discrepancy_ea.vhd:164:3  */
  priority_encoder_3_3 priority_encoder_0 (
    .clock_i(clock_i),
    .reset_i(reset_i),
    .code_i(neg_orresult),
    .bin_o(priority_encoder_0_bin_o));
  /* ../../../vhdl/atbs_core_fixed_window/adaptive_threshold_control/Weyls-Discrepancy/rtl/weyls_discrepancy_ea.vhd:179:3  */
  priority_encoder_3_3 priority_encoder_1 (
    .clock_i(clock_i),
    .reset_i(reset_i),
    .code_i(n3232_o),
    .bin_o(priority_encoder_1_bin_o));
  /* ../../../vhdl/atbs_core_fixed_window/adaptive_threshold_control/Weyls-Discrepancy/rtl/weyls_discrepancy_ea.vhd:187:24  */
  assign n3232_o = orresult[5:3]; // extract
  /* ../../../vhdl/atbs_core_fixed_window/adaptive_threshold_control/Weyls-Discrepancy/rtl/weyls_discrepancy_ea.vhd:194:36  */
  assign n3234_o = weylsd_neg + weylsd_pos;
  /* ../../../vhdl/atbs_core_fixed_window/adaptive_threshold_control/Weyls-Discrepancy/rtl/weyls_discrepancy_ea.vhd:199:36  */
  assign n3235_o = sync_weylsd_strb[1]; // extract
  /* ../../../vhdl/atbs_core_fixed_window/adaptive_threshold_control/Weyls-Discrepancy/rtl/weyls_discrepancy_ea.vhd:91:5  */
  always @(posedge clock_i or posedge reset_i)
    if (reset_i)
      n3236_q <= 6'b000000;
    else
      n3236_q <= next_buf_reg;
  /* ../../../vhdl/atbs_core_fixed_window/adaptive_threshold_control/Weyls-Discrepancy/rtl/weyls_discrepancy_ea.vhd:91:5  */
  always @(posedge clock_i or posedge reset_i)
    if (reset_i)
      n3237_q <= 2'b00;
    else
      n3237_q <= n3035_o;
  /* ../../../vhdl/atbs_core_fixed_window/adaptive_threshold_control/Weyls-Discrepancy/rtl/weyls_discrepancy_ea.vhd:87:5  */
  assign n3238_o = {n3093_o, buf_reg, n3094_o};
  /* ../../../vhdl/atbs_core_fixed_window/adaptive_threshold_control/Weyls-Discrepancy/rtl/weyls_discrepancy_ea.vhd:87:5  */
  assign n3239_o = {gen_spike_2_tc_n15_spike_2_tc_thermo_o, gen_spike_2_tc_n14_spike_2_tc_thermo_o, gen_spike_2_tc_n13_spike_2_tc_thermo_o, gen_spike_2_tc_n12_spike_2_tc_thermo_o, gen_spike_2_tc_n11_spike_2_tc_thermo_o, gen_spike_2_tc_n10_spike_2_tc_thermo_o, gen_spike_2_tc_n9_spike_2_tc_thermo_o, gen_spike_2_tc_n8_spike_2_tc_thermo_o, gen_spike_2_tc_n7_spike_2_tc_thermo_o, gen_spike_2_tc_n6_spike_2_tc_thermo_o, gen_spike_2_tc_n5_spike_2_tc_thermo_o, gen_spike_2_tc_n4_spike_2_tc_thermo_o, gen_spike_2_tc_n3_spike_2_tc_thermo_o, gen_spike_2_tc_n2_spike_2_tc_thermo_o, gen_spike_2_tc_n1_spike_2_tc_thermo_o, 6'b000111};
  assign n3240_o = {n3227_o, n3228_o, n3229_o};
  assign n3241_o = {n3222_o, n3215_o, n3207_o, n3199_o, n3191_o, n3183_o, n3175_o, n3167_o, n3159_o, n3151_o, n3143_o, n3135_o, n3127_o, n3119_o, n3111_o, n3103_o};
  /* ../../../vhdl/atbs_core_fixed_window/adaptive_threshold_control/Weyls-Discrepancy/rtl/weyls_discrepancy_ea.vhd:91:5  */
  always @(posedge clock_i or posedge reset_i)
    if (reset_i)
      n3242_q <= 3'b000;
    else
      n3242_q <= next_weylsd;
endmodule
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
