iic-jku/SG13G2_ATBS-ADC/SG13G2_ATBS-ADC-main/verilog/atbs_core_floating_window/rtl/atbs_core_floating_window_board.v

module priority_encoder_3_3
  (input  clock_i,
   input  reset_i,
   input  [2:0] code_i,
   output [2:0] bin_o);
  wire [2:0] bin;
  wire n2960_o;
  wire [2:0] n2963_o;
  wire n2965_o;
  wire [2:0] n2967_o;
  wire n2968_o;
  wire [2:0] n2970_o;
  assign bin_o = bin; //(module output)
  /* ../../../vhdl/atbs_core_floating_window/adaptive_threshold_control/Priority-Encoder/rtl/priority_encoder_ea.vhd:33:8  */
  assign bin = n2970_o; // (signal)
  /* ../../../vhdl/atbs_core_floating_window/adaptive_threshold_control/Priority-Encoder/rtl/priority_encoder_ea.vhd:44:16  */
  assign n2960_o = code_i[0]; // extract
  /* ../../../vhdl/atbs_core_floating_window/adaptive_threshold_control/Priority-Encoder/rtl/priority_encoder_ea.vhd:44:7  */
  assign n2963_o = n2960_o ? 3'b001 : 3'b000;
  /* ../../../vhdl/atbs_core_floating_window/adaptive_threshold_control/Priority-Encoder/rtl/priority_encoder_ea.vhd:44:16  */
  assign n2965_o = code_i[1]; // extract
  /* ../../../vhdl/atbs_core_floating_window/adaptive_threshold_control/Priority-Encoder/rtl/priority_encoder_ea.vhd:44:7  */
  assign n2967_o = n2965_o ? 3'b010 : n2963_o;
  /* ../../../vhdl/atbs_core_floating_window/adaptive_threshold_control/Priority-Encoder/rtl/priority_encoder_ea.vhd:44:16  */
  assign n2968_o = code_i[2]; // extract
  /* ../../../vhdl/atbs_core_floating_window/adaptive_threshold_control/Priority-Encoder/rtl/priority_encoder_ea.vhd:44:7  */
  assign n2970_o = n2968_o ? 3'b011 : n2967_o;
endmodule

module spike_2_thermocode_6
  (input  [1:0] spike_i,
   input  [5:0] thermo_i,
   output [5:0] thermo_o);
  wire plus;
  wire minus;
  wire [5:0] thermo;
  wire n2925_o;
  wire n2926_o;
  wire n2929_o;
  wire n2930_o;
  wire n2931_o;
  wire n2932_o;
  wire n2933_o;
  wire n2934_o;
  wire n2935_o;
  wire n2936_o;
  wire n2937_o;
  wire n2938_o;
  wire n2939_o;
  wire n2940_o;
  wire n2941_o;
  wire n2942_o;
  wire n2943_o;
  wire n2944_o;
  wire n2945_o;
  wire n2946_o;
  wire n2947_o;
  wire n2948_o;
  wire n2949_o;
  wire n2950_o;
  wire n2951_o;
  wire n2952_o;
  wire n2953_o;
  wire n2954_o;
  wire [5:0] n2955_o;
  wire [5:0] n2956_o;
  assign thermo_o = thermo; //(module output)
  /* ../../../vhdl/atbs_core_floating_window/adaptive_threshold_control/Spike-2-Thermocode/rtl/spike_2_thermocode_ea.vhd:30:8  */
  assign plus = n2926_o; // (signal)
  /* ../../../vhdl/atbs_core_floating_window/adaptive_threshold_control/Spike-2-Thermocode/rtl/spike_2_thermocode_ea.vhd:31:8  */
  assign minus = n2925_o; // (signal)
  /* ../../../vhdl/atbs_core_floating_window/adaptive_threshold_control/Spike-2-Thermocode/rtl/spike_2_thermocode_ea.vhd:32:8  */
  assign thermo = n2956_o; // (signal)
  /* ../../../vhdl/atbs_core_floating_window/adaptive_threshold_control/Spike-2-Thermocode/rtl/spike_2_thermocode_ea.vhd:37:19  */
  assign n2925_o = spike_i[1]; // extract
  /* ../../../vhdl/atbs_core_floating_window/adaptive_threshold_control/Spike-2-Thermocode/rtl/spike_2_thermocode_ea.vhd:38:18  */
  assign n2926_o = spike_i[0]; // extract
  /* ../../../vhdl/atbs_core_floating_window/adaptive_threshold_control/Spike-2-Thermocode/rtl/spike_2_thermocode_ea.vhd:43:16  */
  assign n2929_o = spike_i == 2'b00;
  /* ../../../vhdl/atbs_core_floating_window/adaptive_threshold_control/Spike-2-Thermocode/rtl/spike_2_thermocode_ea.vhd:48:37  */
  assign n2930_o = thermo_i[1]; // extract
  /* ../../../vhdl/atbs_core_floating_window/adaptive_threshold_control/Spike-2-Thermocode/rtl/spike_2_thermocode_ea.vhd:48:41  */
  assign n2931_o = n2930_o & minus;
  /* ../../../vhdl/atbs_core_floating_window/adaptive_threshold_control/Spike-2-Thermocode/rtl/spike_2_thermocode_ea.vhd:48:25  */
  assign n2932_o = plus | n2931_o;
  /* ../../../vhdl/atbs_core_floating_window/adaptive_threshold_control/Spike-2-Thermocode/rtl/spike_2_thermocode_ea.vhd:53:31  */
  assign n2933_o = thermo_i[0]; // extract
  /* ../../../vhdl/atbs_core_floating_window/adaptive_threshold_control/Spike-2-Thermocode/rtl/spike_2_thermocode_ea.vhd:53:37  */
  assign n2934_o = n2933_o & plus;
  /* ../../../vhdl/atbs_core_floating_window/adaptive_threshold_control/Spike-2-Thermocode/rtl/spike_2_thermocode_ea.vhd:53:59  */
  assign n2935_o = thermo_i[2]; // extract
  /* ../../../vhdl/atbs_core_floating_window/adaptive_threshold_control/Spike-2-Thermocode/rtl/spike_2_thermocode_ea.vhd:53:65  */
  assign n2936_o = n2935_o & minus;
  /* ../../../vhdl/atbs_core_floating_window/adaptive_threshold_control/Spike-2-Thermocode/rtl/spike_2_thermocode_ea.vhd:53:47  */
  assign n2937_o = n2934_o | n2936_o;
  /* ../../../vhdl/atbs_core_floating_window/adaptive_threshold_control/Spike-2-Thermocode/rtl/spike_2_thermocode_ea.vhd:53:31  */
  assign n2938_o = thermo_i[1]; // extract
  /* ../../../vhdl/atbs_core_floating_window/adaptive_threshold_control/Spike-2-Thermocode/rtl/spike_2_thermocode_ea.vhd:53:37  */
  assign n2939_o = n2938_o & plus;
  /* ../../../vhdl/atbs_core_floating_window/adaptive_threshold_control/Spike-2-Thermocode/rtl/spike_2_thermocode_ea.vhd:53:59  */
  assign n2940_o = thermo_i[3]; // extract
  /* ../../../vhdl/atbs_core_floating_window/adaptive_threshold_control/Spike-2-Thermocode/rtl/spike_2_thermocode_ea.vhd:53:65  */
  assign n2941_o = n2940_o & minus;
  /* ../../../vhdl/atbs_core_floating_window/adaptive_threshold_control/Spike-2-Thermocode/rtl/spike_2_thermocode_ea.vhd:53:47  */
  assign n2942_o = n2939_o | n2941_o;
  /* ../../../vhdl/atbs_core_floating_window/adaptive_threshold_control/Spike-2-Thermocode/rtl/spike_2_thermocode_ea.vhd:53:31  */
  assign n2943_o = thermo_i[2]; // extract
  /* ../../../vhdl/atbs_core_floating_window/adaptive_threshold_control/Spike-2-Thermocode/rtl/spike_2_thermocode_ea.vhd:53:37  */
  assign n2944_o = n2943_o & plus;
  /* ../../../vhdl/atbs_core_floating_window/adaptive_threshold_control/Spike-2-Thermocode/rtl/spike_2_thermocode_ea.vhd:53:59  */
  assign n2945_o = thermo_i[4]; // extract
  /* ../../../vhdl/atbs_core_floating_window/adaptive_threshold_control/Spike-2-Thermocode/rtl/spike_2_thermocode_ea.vhd:53:65  */
  assign n2946_o = n2945_o & minus;
  /* ../../../vhdl/atbs_core_floating_window/adaptive_threshold_control/Spike-2-Thermocode/rtl/spike_2_thermocode_ea.vhd:53:47  */
  assign n2947_o = n2944_o | n2946_o;
  /* ../../../vhdl/atbs_core_floating_window/adaptive_threshold_control/Spike-2-Thermocode/rtl/spike_2_thermocode_ea.vhd:53:31  */
  assign n2948_o = thermo_i[3]; // extract
  /* ../../../vhdl/atbs_core_floating_window/adaptive_threshold_control/Spike-2-Thermocode/rtl/spike_2_thermocode_ea.vhd:53:37  */
  assign n2949_o = n2948_o & plus;
  /* ../../../vhdl/atbs_core_floating_window/adaptive_threshold_control/Spike-2-Thermocode/rtl/spike_2_thermocode_ea.vhd:53:59  */
  assign n2950_o = thermo_i[5]; // extract
  /* ../../../vhdl/atbs_core_floating_window/adaptive_threshold_control/Spike-2-Thermocode/rtl/spike_2_thermocode_ea.vhd:53:65  */
  assign n2951_o = n2950_o & minus;
  /* ../../../vhdl/atbs_core_floating_window/adaptive_threshold_control/Spike-2-Thermocode/rtl/spike_2_thermocode_ea.vhd:53:47  */
  assign n2952_o = n2949_o | n2951_o;
  /* ../../../vhdl/atbs_core_floating_window/adaptive_threshold_control/Spike-2-Thermocode/rtl/spike_2_thermocode_ea.vhd:57:40  */
  assign n2953_o = thermo_i[4]; // extract
  /* ../../../vhdl/atbs_core_floating_window/adaptive_threshold_control/Spike-2-Thermocode/rtl/spike_2_thermocode_ea.vhd:57:56  */
  assign n2954_o = n2953_o & plus;
  assign n2955_o = {n2954_o, n2952_o, n2947_o, n2942_o, n2937_o, n2932_o};
  /* ../../../vhdl/atbs_core_floating_window/adaptive_threshold_control/Spike-2-Thermocode/rtl/spike_2_thermocode_ea.vhd:43:5  */
  assign n2956_o = n2929_o ? thermo_i : n2955_o;
endmodule

module uart_rx_9_8
  (input  clock_i,
   input  reset_i,
   input  [8:0] baudrate_adj_i,
   input  rx_i,
   output [7:0] data_o,
   output data_valid_strb_o);
  wire [2:0] receive_counter_value;
  wire [2:0] next_receive_counter_value;
  wire [8:0] baud_counter_value;
  wire [8:0] next_baud_counter_value;
  wire [7:0] received_data;
  wire [7:0] next_received_data;
  wire data_valid_strb;
  wire [1:0] rx_state;
  wire [1:0] next_rx_state;
  wire next_strobe;
  wire n2819_o;
  wire n2820_o;
  wire [2:0] n2822_o;
  wire [2:0] n2823_o;
  wire [2:0] n2825_o;
  wire n2828_o;
  wire [8:0] n2830_o;
  wire [8:0] n2832_o;
  wire n2834_o;
  wire [8:0] n2836_o;
  wire n2839_o;
  wire [1:0] n2841_o;
  wire n2843_o;
  wire n2844_o;
  wire [1:0] n2846_o;
  wire n2848_o;
  wire [8:0] n2850_o;
  wire n2851_o;
  wire [7:0] n2855_o;
  wire n2856_o;
  wire n2858_o;
  wire n2859_o;
  wire [1:0] n2861_o;
  wire n2863_o;
  wire [8:0] n2865_o;
  wire n2866_o;
  wire [1:0] n2868_o;
  wire n2871_o;
  wire n2873_o;
  wire [3:0] n2874_o;
  reg [7:0] n2876_o;
  reg [1:0] n2877_o;
  reg n2880_o;
  reg [2:0] n2883_q;
  reg [8:0] n2884_q;
  reg [7:0] n2885_q;
  reg n2886_q;
  reg [1:0] n2887_q;
  wire n2889_o;
  wire n2890_o;
  wire n2891_o;
  wire n2892_o;
  wire n2893_o;
  wire n2894_o;
  wire n2895_o;
  wire n2896_o;
  wire n2897_o;
  wire n2898_o;
  wire n2899_o;
  wire n2900_o;
  wire n2901_o;
  wire n2902_o;
  wire n2903_o;
  wire n2904_o;
  wire n2905_o;
  wire n2906_o;
  wire n2907_o;
  wire n2908_o;
  wire n2909_o;
  wire n2910_o;
  wire n2911_o;
  wire n2912_o;
  wire n2913_o;
  wire n2914_o;
  wire n2915_o;
  wire n2916_o;
  wire n2917_o;
  wire n2918_o;
  wire n2919_o;
  wire n2920_o;
  wire n2921_o;
  wire n2922_o;
  wire [7:0] n2923_o;
  assign data_o = received_data; //(module output)
  assign data_valid_strb_o = data_valid_strb; //(module output)
  /* ../../../vhdl/atbs_core_floating_window/uart/rtl/uart_rx_ea.vhd:38:8  */
  assign receive_counter_value = n2883_q; // (signal)
  /* ../../../vhdl/atbs_core_floating_window/uart/rtl/uart_rx_ea.vhd:39:8  */
  assign next_receive_counter_value = n2825_o; // (signal)
  /* ../../../vhdl/atbs_core_floating_window/uart/rtl/uart_rx_ea.vhd:42:8  */
  assign baud_counter_value = n2884_q; // (signal)
  /* ../../../vhdl/atbs_core_floating_window/uart/rtl/uart_rx_ea.vhd:43:8  */
  assign next_baud_counter_value = n2836_o; // (signal)
  /* ../../../vhdl/atbs_core_floating_window/uart/rtl/uart_rx_ea.vhd:46:8  */
  assign received_data = n2885_q; // (signal)
  /* ../../../vhdl/atbs_core_floating_window/uart/rtl/uart_rx_ea.vhd:47:8  */
  assign next_received_data = n2876_o; // (signal)
  /* ../../../vhdl/atbs_core_floating_window/uart/rtl/uart_rx_ea.vhd:48:8  */
  assign data_valid_strb = n2886_q; // (signal)
  /* ../../../vhdl/atbs_core_floating_window/uart/rtl/uart_rx_ea.vhd:51:8  */
  assign rx_state = n2887_q; // (signal)
  /* ../../../vhdl/atbs_core_floating_window/uart/rtl/uart_rx_ea.vhd:52:8  */
  assign next_rx_state = n2877_o; // (signal)
  /* ../../../vhdl/atbs_core_floating_window/uart/rtl/uart_rx_ea.vhd:54:8  */
  assign next_strobe = n2880_o; // (signal)
  /* ../../../vhdl/atbs_core_floating_window/uart/rtl/uart_rx_ea.vhd:81:17  */
  assign n2819_o = rx_state == 2'b10;
  /* ../../../vhdl/atbs_core_floating_window/uart/rtl/uart_rx_ea.vhd:82:29  */
  assign n2820_o = baud_counter_value == baudrate_adj_i;
  /* ../../../vhdl/atbs_core_floating_window/uart/rtl/uart_rx_ea.vhd:83:61  */
  assign n2822_o = receive_counter_value + 3'b001;
  /* ../../../vhdl/atbs_core_floating_window/uart/rtl/uart_rx_ea.vhd:82:7  */
  assign n2823_o = n2820_o ? n2822_o : receive_counter_value;
  /* ../../../vhdl/atbs_core_floating_window/uart/rtl/uart_rx_ea.vhd:81:5  */
  assign n2825_o = n2819_o ? n2823_o : 3'b000;
  /* ../../../vhdl/atbs_core_floating_window/uart/rtl/uart_rx_ea.vhd:96:27  */
  assign n2828_o = $unsigned(baud_counter_value) < $unsigned(baudrate_adj_i);
  /* ../../../vhdl/atbs_core_floating_window/uart/rtl/uart_rx_ea.vhd:97:53  */
  assign n2830_o = baud_counter_value + 9'b000000001;
  /* ../../../vhdl/atbs_core_floating_window/uart/rtl/uart_rx_ea.vhd:96:5  */
  assign n2832_o = n2828_o ? n2830_o : 9'b000000000;
  /* ../../../vhdl/atbs_core_floating_window/uart/rtl/uart_rx_ea.vhd:102:17  */
  assign n2834_o = rx_state == 2'b00;
  /* ../../../vhdl/atbs_core_floating_window/uart/rtl/uart_rx_ea.vhd:102:5  */
  assign n2836_o = n2834_o ? 9'b000000000 : n2832_o;
  /* ../../../vhdl/atbs_core_floating_window/uart/rtl/uart_rx_ea.vhd:118:17  */
  assign n2839_o = ~rx_i;
  /* ../../../vhdl/atbs_core_floating_window/uart/rtl/uart_rx_ea.vhd:118:9  */
  assign n2841_o = n2839_o ? 2'b01 : rx_state;
  /* ../../../vhdl/atbs_core_floating_window/uart/rtl/uart_rx_ea.vhd:116:7  */
  assign n2843_o = rx_state == 2'b00;
  /* ../../../vhdl/atbs_core_floating_window/uart/rtl/uart_rx_ea.vhd:123:31  */
  assign n2844_o = baud_counter_value == baudrate_adj_i;
  /* ../../../vhdl/atbs_core_floating_window/uart/rtl/uart_rx_ea.vhd:123:9  */
  assign n2846_o = n2844_o ? 2'b10 : rx_state;
  /* ../../../vhdl/atbs_core_floating_window/uart/rtl/uart_rx_ea.vhd:122:7  */
  assign n2848_o = rx_state == 2'b01;
  /* ../../../vhdl/atbs_core_floating_window/uart/rtl/uart_rx_ea.vhd:128:33  */
  assign n2850_o = baudrate_adj_i >> 31'b0000000000000000000000000000001;
  /* ../../../vhdl/atbs_core_floating_window/uart/rtl/uart_rx_ea.vhd:128:31  */
  assign n2851_o = baud_counter_value == n2850_o;
  /* ../../../vhdl/atbs_core_floating_window/uart/rtl/uart_rx_ea.vhd:128:9  */
  assign n2855_o = n2851_o ? n2923_o : received_data;
  /* ../../../vhdl/atbs_core_floating_window/uart/rtl/uart_rx_ea.vhd:131:31  */
  assign n2856_o = baud_counter_value == baudrate_adj_i;
  /* ../../../vhdl/atbs_core_floating_window/uart/rtl/uart_rx_ea.vhd:131:74  */
  assign n2858_o = receive_counter_value == 3'b111;
  /* ../../../vhdl/atbs_core_floating_window/uart/rtl/uart_rx_ea.vhd:131:48  */
  assign n2859_o = n2858_o & n2856_o;
  /* ../../../vhdl/atbs_core_floating_window/uart/rtl/uart_rx_ea.vhd:131:9  */
  assign n2861_o = n2859_o ? 2'b11 : rx_state;
  /* ../../../vhdl/atbs_core_floating_window/uart/rtl/uart_rx_ea.vhd:127:7  */
  assign n2863_o = rx_state == 2'b10;
  /* ../../../vhdl/atbs_core_floating_window/uart/rtl/uart_rx_ea.vhd:136:33  */
  assign n2865_o = baudrate_adj_i >> 31'b0000000000000000000000000000001;
  /* ../../../vhdl/atbs_core_floating_window/uart/rtl/uart_rx_ea.vhd:136:31  */
  assign n2866_o = baud_counter_value == n2865_o;
  /* ../../../vhdl/atbs_core_floating_window/uart/rtl/uart_rx_ea.vhd:136:9  */
  assign n2868_o = n2866_o ? 2'b00 : rx_state;
  /* ../../../vhdl/atbs_core_floating_window/uart/rtl/uart_rx_ea.vhd:136:9  */
  assign n2871_o = n2866_o ? 1'b1 : 1'b0;
  /* ../../../vhdl/atbs_core_floating_window/uart/rtl/uart_rx_ea.vhd:135:7  */
  assign n2873_o = rx_state == 2'b11;
  assign n2874_o = {n2873_o, n2863_o, n2848_o, n2843_o};
  /* ../../../vhdl/atbs_core_floating_window/uart/rtl/uart_rx_ea.vhd:115:5  */
  always @*
    case (n2874_o)
      4'b1000: n2876_o = received_data;
      4'b0100: n2876_o = n2855_o;
      4'b0010: n2876_o = received_data;
      4'b0001: n2876_o = received_data;
      default: n2876_o = 8'b00000000;
    endcase
  /* ../../../vhdl/atbs_core_floating_window/uart/rtl/uart_rx_ea.vhd:115:5  */
  always @*
    case (n2874_o)
      4'b1000: n2877_o = n2868_o;
      4'b0100: n2877_o = n2861_o;
      4'b0010: n2877_o = n2846_o;
      4'b0001: n2877_o = n2841_o;
      default: n2877_o = rx_state;
    endcase
  /* ../../../vhdl/atbs_core_floating_window/uart/rtl/uart_rx_ea.vhd:115:5  */
  always @*
    case (n2874_o)
      4'b1000: n2880_o = n2871_o;
      4'b0100: n2880_o = 1'b0;
      4'b0010: n2880_o = 1'b0;
      4'b0001: n2880_o = 1'b0;
      default: n2880_o = 1'b0;
    endcase
  /* ../../../vhdl/atbs_core_floating_window/uart/rtl/uart_rx_ea.vhd:66:5  */
  always @(posedge clock_i or posedge reset_i)
    if (reset_i)
      n2883_q <= 3'b000;
    else
      n2883_q <= next_receive_counter_value;
  /* ../../../vhdl/atbs_core_floating_window/uart/rtl/uart_rx_ea.vhd:66:5  */
  always @(posedge clock_i or posedge reset_i)
    if (reset_i)
      n2884_q <= 9'b000000000;
    else
      n2884_q <= next_baud_counter_value;
  /* ../../../vhdl/atbs_core_floating_window/uart/rtl/uart_rx_ea.vhd:66:5  */
  always @(posedge clock_i or posedge reset_i)
    if (reset_i)
      n2885_q <= 8'b00000000;
    else
      n2885_q <= next_received_data;
  /* ../../../vhdl/atbs_core_floating_window/uart/rtl/uart_rx_ea.vhd:66:5  */
  always @(posedge clock_i or posedge reset_i)
    if (reset_i)
      n2886_q <= 1'b0;
    else
      n2886_q <= next_strobe;
  /* ../../../vhdl/atbs_core_floating_window/uart/rtl/uart_rx_ea.vhd:66:5  */
  always @(posedge clock_i or posedge reset_i)
    if (reset_i)
      n2887_q <= 2'b00;
    else
      n2887_q <= next_rx_state;
  /* ../../../vhdl/atbs_core_floating_window/uart/rtl/uart_rx_ea.vhd:129:11  */
  assign n2889_o = receive_counter_value[2]; // extract
  /* ../../../vhdl/atbs_core_floating_window/uart/rtl/uart_rx_ea.vhd:129:11  */
  assign n2890_o = ~n2889_o;
  /* ../../../vhdl/atbs_core_floating_window/uart/rtl/uart_rx_ea.vhd:129:11  */
  assign n2891_o = receive_counter_value[1]; // extract
  /* ../../../vhdl/atbs_core_floating_window/uart/rtl/uart_rx_ea.vhd:129:11  */
  assign n2892_o = ~n2891_o;
  /* ../../../vhdl/atbs_core_floating_window/uart/rtl/uart_rx_ea.vhd:129:11  */
  assign n2893_o = n2890_o & n2892_o;
  /* ../../../vhdl/atbs_core_floating_window/uart/rtl/uart_rx_ea.vhd:129:11  */
  assign n2894_o = n2890_o & n2891_o;
  /* ../../../vhdl/atbs_core_floating_window/uart/rtl/uart_rx_ea.vhd:129:11  */
  assign n2895_o = n2889_o & n2892_o;
  /* ../../../vhdl/atbs_core_floating_window/uart/rtl/uart_rx_ea.vhd:129:11  */
  assign n2896_o = n2889_o & n2891_o;
  /* ../../../vhdl/atbs_core_floating_window/uart/rtl/uart_rx_ea.vhd:129:11  */
  assign n2897_o = receive_counter_value[0]; // extract
  /* ../../../vhdl/atbs_core_floating_window/uart/rtl/uart_rx_ea.vhd:129:11  */
  assign n2898_o = ~n2897_o;
  /* ../../../vhdl/atbs_core_floating_window/uart/rtl/uart_rx_ea.vhd:129:11  */
  assign n2899_o = n2893_o & n2898_o;
  /* ../../../vhdl/atbs_core_floating_window/uart/rtl/uart_rx_ea.vhd:129:11  */
  assign n2900_o = n2893_o & n2897_o;
  /* ../../../vhdl/atbs_core_floating_window/uart/rtl/uart_rx_ea.vhd:129:11  */
  assign n2901_o = n2894_o & n2898_o;
  /* ../../../vhdl/atbs_core_floating_window/uart/rtl/uart_rx_ea.vhd:129:11  */
  assign n2902_o = n2894_o & n2897_o;
  /* ../../../vhdl/atbs_core_floating_window/uart/rtl/uart_rx_ea.vhd:129:11  */
  assign n2903_o = n2895_o & n2898_o;
  /* ../../../vhdl/atbs_core_floating_window/uart/rtl/uart_rx_ea.vhd:129:11  */
  assign n2904_o = n2895_o & n2897_o;
  /* ../../../vhdl/atbs_core_floating_window/uart/rtl/uart_rx_ea.vhd:129:11  */
  assign n2905_o = n2896_o & n2898_o;
  /* ../../../vhdl/atbs_core_floating_window/uart/rtl/uart_rx_ea.vhd:129:11  */
  assign n2906_o = n2896_o & n2897_o;
  assign n2907_o = received_data[0]; // extract
  /* ../../../vhdl/atbs_core_floating_window/uart/rtl/uart_rx_ea.vhd:129:11  */
  assign n2908_o = n2899_o ? rx_i : n2907_o;
  assign n2909_o = received_data[1]; // extract
  /* ../../../vhdl/atbs_core_floating_window/uart/rtl/uart_rx_ea.vhd:129:11  */
  assign n2910_o = n2900_o ? rx_i : n2909_o;
  assign n2911_o = received_data[2]; // extract
  /* ../../../vhdl/atbs_core_floating_window/uart/rtl/uart_rx_ea.vhd:129:11  */
  assign n2912_o = n2901_o ? rx_i : n2911_o;
  assign n2913_o = received_data[3]; // extract
  /* ../../../vhdl/atbs_core_floating_window/uart/rtl/uart_rx_ea.vhd:129:11  */
  assign n2914_o = n2902_o ? rx_i : n2913_o;
  assign n2915_o = received_data[4]; // extract
  /* ../../../vhdl/atbs_core_floating_window/uart/rtl/uart_rx_ea.vhd:129:11  */
  assign n2916_o = n2903_o ? rx_i : n2915_o;
  assign n2917_o = received_data[5]; // extract
  /* ../../../vhdl/atbs_core_floating_window/uart/rtl/uart_rx_ea.vhd:129:11  */
  assign n2918_o = n2904_o ? rx_i : n2917_o;
  assign n2919_o = received_data[6]; // extract
  /* ../../../vhdl/atbs_core_floating_window/uart/rtl/uart_rx_ea.vhd:129:11  */
  assign n2920_o = n2905_o ? rx_i : n2919_o;
  assign n2921_o = received_data[7]; // extract
  /* ../../../vhdl/atbs_core_floating_window/uart/rtl/uart_rx_ea.vhd:129:11  */
  assign n2922_o = n2906_o ? rx_i : n2921_o;
  assign n2923_o = {n2922_o, n2920_o, n2918_o, n2916_o, n2914_o, n2912_o, n2910_o, n2908_o};
endmodule

module uart_tx_9_8
  (input  clock_i,
   input  reset_i,
   input  [8:0] baudrate_adj_i,
   input  tx_start_strb_i,
   input  [7:0] data_i,
   output tx_strb_o,
   output tx_o);
  wire tx;
  wire tx_strb;
  wire next_tx_strb;
  wire [2:0] transmit_counter_value;
  wire [2:0] next_transmit_counter_value;
  wire [8:0] baud_counter_value;
  wire [8:0] next_baud_counter_value;
  wire [2:0] tx_state;
  wire [2:0] next_tx_state;
  wire n2699_o;
  wire n2700_o;
  wire [2:0] n2702_o;
  wire [2:0] n2703_o;
  wire [2:0] n2705_o;
  wire n2708_o;
  wire [8:0] n2710_o;
  wire [8:0] n2712_o;
  wire n2715_o;
  wire [2:0] n2718_o;
  wire [2:0] n2719_o;
  wire n2721_o;
  wire n2722_o;
  wire n2725_o;
  wire [2:0] n2728_o;
  wire n2730_o;
  wire n2731_o;
  wire [2:0] n2733_o;
  wire n2735_o;
  wire n2737_o;
  wire n2742_o;
  wire n2743_o;
  wire n2744_o;
  wire [2:0] n2746_o;
  wire n2748_o;
  wire n2749_o;
  wire n2751_o;
  wire n2752_o;
  wire [2:0] n2755_o;
  wire [2:0] n2756_o;
  wire n2758_o;
  wire [4:0] n2759_o;
  reg n2764_o;
  reg [2:0] n2766_o;
  wire n2770_o;
  wire n2772_o;
  wire n2774_o;
  wire n2775_o;
  wire n2776_o;
  wire n2777_o;
  reg n2779_q;
  reg [2:0] n2780_q;
  reg [8:0] n2781_q;
  reg [2:0] n2782_q;
  wire n2783_o;
  wire n2784_o;
  wire n2785_o;
  wire n2786_o;
  wire n2787_o;
  wire n2788_o;
  wire n2789_o;
  wire n2790_o;
  wire [1:0] n2791_o;
  reg n2792_o;
  wire [1:0] n2793_o;
  reg n2794_o;
  wire n2795_o;
  wire n2796_o;
  assign tx_strb_o = tx_strb; //(module output)
  assign tx_o = tx; //(module output)
  /* ../../../vhdl/atbs_core_floating_window/uart/rtl/uart_tx_ea.vhd:38:8  */
  assign tx = n2764_o; // (signal)
  /* ../../../vhdl/atbs_core_floating_window/uart/rtl/uart_tx_ea.vhd:39:8  */
  assign tx_strb = n2779_q; // (signal)
  /* ../../../vhdl/atbs_core_floating_window/uart/rtl/uart_tx_ea.vhd:40:8  */
  assign next_tx_strb = n2777_o; // (signal)
  /* ../../../vhdl/atbs_core_floating_window/uart/rtl/uart_tx_ea.vhd:43:8  */
  assign transmit_counter_value = n2780_q; // (signal)
  /* ../../../vhdl/atbs_core_floating_window/uart/rtl/uart_tx_ea.vhd:44:8  */
  assign next_transmit_counter_value = n2705_o; // (signal)
  /* ../../../vhdl/atbs_core_floating_window/uart/rtl/uart_tx_ea.vhd:47:8  */
  assign baud_counter_value = n2781_q; // (signal)
  /* ../../../vhdl/atbs_core_floating_window/uart/rtl/uart_tx_ea.vhd:48:8  */
  assign next_baud_counter_value = n2712_o; // (signal)
  /* ../../../vhdl/atbs_core_floating_window/uart/rtl/uart_tx_ea.vhd:51:8  */
  assign tx_state = n2782_q; // (signal)
  /* ../../../vhdl/atbs_core_floating_window/uart/rtl/uart_tx_ea.vhd:52:8  */
  assign next_tx_state = n2766_o; // (signal)
  /* ../../../vhdl/atbs_core_floating_window/uart/rtl/uart_tx_ea.vhd:78:29  */
  assign n2699_o = tx_state == 3'b011;
  /* ../../../vhdl/atbs_core_floating_window/uart/rtl/uart_tx_ea.vhd:79:47  */
  assign n2700_o = baud_counter_value == baudrate_adj_i;
  /* ../../../vhdl/atbs_core_floating_window/uart/rtl/uart_tx_ea.vhd:80:87  */
  assign n2702_o = transmit_counter_value + 3'b001;
  /* ../../../vhdl/atbs_core_floating_window/uart/rtl/uart_tx_ea.vhd:79:25  */
  assign n2703_o = n2700_o ? n2702_o : transmit_counter_value;
  /* ../../../vhdl/atbs_core_floating_window/uart/rtl/uart_tx_ea.vhd:78:17  */
  assign n2705_o = n2699_o ? n2703_o : 3'b000;
  /* ../../../vhdl/atbs_core_floating_window/uart/rtl/uart_tx_ea.vhd:93:39  */
  assign n2708_o = $unsigned(baud_counter_value) < $unsigned(baudrate_adj_i);
  /* ../../../vhdl/atbs_core_floating_window/uart/rtl/uart_tx_ea.vhd:94:71  */
  assign n2710_o = baud_counter_value + 9'b000000001;
  /* ../../../vhdl/atbs_core_floating_window/uart/rtl/uart_tx_ea.vhd:93:17  */
  assign n2712_o = n2708_o ? n2710_o : 9'b000000000;
  /* ../../../vhdl/atbs_core_floating_window/uart/rtl/uart_tx_ea.vhd:111:63  */
  assign n2715_o = baud_counter_value == baudrate_adj_i;
  /* ../../../vhdl/atbs_core_floating_window/uart/rtl/uart_tx_ea.vhd:111:41  */
  assign n2718_o = n2715_o ? 3'b010 : 3'b001;
  /* ../../../vhdl/atbs_core_floating_window/uart/rtl/uart_tx_ea.vhd:110:33  */
  assign n2719_o = tx_start_strb_i ? n2718_o : tx_state;
  /* ../../../vhdl/atbs_core_floating_window/uart/rtl/uart_tx_ea.vhd:108:25  */
  assign n2721_o = tx_state == 3'b000;
  /* ../../../vhdl/atbs_core_floating_window/uart/rtl/uart_tx_ea.vhd:123:55  */
  assign n2722_o = baud_counter_value == baudrate_adj_i;
  /* ../../../vhdl/atbs_core_floating_window/uart/rtl/uart_tx_ea.vhd:123:33  */
  assign n2725_o = n2722_o ? 1'b0 : 1'b1;
  /* ../../../vhdl/atbs_core_floating_window/uart/rtl/uart_tx_ea.vhd:123:33  */
  assign n2728_o = n2722_o ? 3'b010 : tx_state;
  /* ../../../vhdl/atbs_core_floating_window/uart/rtl/uart_tx_ea.vhd:121:25  */
  assign n2730_o = tx_state == 3'b001;
  /* ../../../vhdl/atbs_core_floating_window/uart/rtl/uart_tx_ea.vhd:130:55  */
  assign n2731_o = baud_counter_value == baudrate_adj_i;
  /* ../../../vhdl/atbs_core_floating_window/uart/rtl/uart_tx_ea.vhd:130:33  */
  assign n2733_o = n2731_o ? 3'b011 : tx_state;
  /* ../../../vhdl/atbs_core_floating_window/uart/rtl/uart_tx_ea.vhd:128:25  */
  assign n2735_o = tx_state == 3'b010;
  /* ../../../vhdl/atbs_core_floating_window/uart/rtl/uart_tx_ea.vhd:135:59  */
  assign n2737_o = $unsigned(transmit_counter_value) <= $unsigned(3'b111);
  /* ../../../vhdl/atbs_core_floating_window/uart/rtl/uart_tx_ea.vhd:137:67  */
  assign n2742_o = transmit_counter_value == 3'b111;
  /* ../../../vhdl/atbs_core_floating_window/uart/rtl/uart_tx_ea.vhd:137:113  */
  assign n2743_o = baud_counter_value == baudrate_adj_i;
  /* ../../../vhdl/atbs_core_floating_window/uart/rtl/uart_tx_ea.vhd:137:90  */
  assign n2744_o = n2743_o & n2742_o;
  /* ../../../vhdl/atbs_core_floating_window/uart/rtl/uart_tx_ea.vhd:135:33  */
  assign n2746_o = n2749_o ? 3'b100 : tx_state;
  /* ../../../vhdl/atbs_core_floating_window/uart/rtl/uart_tx_ea.vhd:135:33  */
  assign n2748_o = n2737_o ? n2796_o : 1'bX;
  /* ../../../vhdl/atbs_core_floating_window/uart/rtl/uart_tx_ea.vhd:135:33  */
  assign n2749_o = n2744_o & n2737_o;
  /* ../../../vhdl/atbs_core_floating_window/uart/rtl/uart_tx_ea.vhd:134:25  */
  assign n2751_o = tx_state == 3'b011;
  /* ../../../vhdl/atbs_core_floating_window/uart/rtl/uart_tx_ea.vhd:144:55  */
  assign n2752_o = baud_counter_value == baudrate_adj_i;
  /* ../../../vhdl/atbs_core_floating_window/uart/rtl/uart_tx_ea.vhd:146:41  */
  assign n2755_o = tx_start_strb_i ? 3'b010 : 3'b000;
  /* ../../../vhdl/atbs_core_floating_window/uart/rtl/uart_tx_ea.vhd:144:33  */
  assign n2756_o = n2752_o ? n2755_o : tx_state;
  /* ../../../vhdl/atbs_core_floating_window/uart/rtl/uart_tx_ea.vhd:142:25  */
  assign n2758_o = tx_state == 3'b100;
  assign n2759_o = {n2758_o, n2751_o, n2735_o, n2730_o, n2721_o};
  /* ../../../vhdl/atbs_core_floating_window/uart/rtl/uart_tx_ea.vhd:107:17  */
  always @*
    case (n2759_o)
      5'b10000: n2764_o = 1'b1;
      5'b01000: n2764_o = n2748_o;
      5'b00100: n2764_o = 1'b0;
      5'b00010: n2764_o = n2725_o;
      5'b00001: n2764_o = 1'b1;
      default: n2764_o = 1'bX;
    endcase
  /* ../../../vhdl/atbs_core_floating_window/uart/rtl/uart_tx_ea.vhd:107:17  */
  always @*
    case (n2759_o)
      5'b10000: n2766_o = n2756_o;
      5'b01000: n2766_o = n2746_o;
      5'b00100: n2766_o = n2733_o;
      5'b00010: n2766_o = n2728_o;
      5'b00001: n2766_o = n2719_o;
      default: n2766_o = tx_state;
    endcase
  /* ../../../vhdl/atbs_core_floating_window/uart/rtl/uart_tx_ea.vhd:158:37  */
  assign n2770_o = tx_state == 3'b100;
  /* ../../../vhdl/atbs_core_floating_window/uart/rtl/uart_tx_ea.vhd:158:66  */
  assign n2772_o = next_tx_state == 3'b010;
  /* ../../../vhdl/atbs_core_floating_window/uart/rtl/uart_tx_ea.vhd:158:94  */
  assign n2774_o = next_tx_state == 3'b000;
  /* ../../../vhdl/atbs_core_floating_window/uart/rtl/uart_tx_ea.vhd:158:77  */
  assign n2775_o = n2772_o | n2774_o;
  /* ../../../vhdl/atbs_core_floating_window/uart/rtl/uart_tx_ea.vhd:158:47  */
  assign n2776_o = n2775_o & n2770_o;
  /* ../../../vhdl/atbs_core_floating_window/uart/rtl/uart_tx_ea.vhd:158:23  */
  assign n2777_o = n2776_o ? 1'b1 : 1'b0;
  /* ../../../vhdl/atbs_core_floating_window/uart/rtl/uart_tx_ea.vhd:63:17  */
  always @(posedge clock_i or posedge reset_i)
    if (reset_i)
      n2779_q <= 1'b0;
    else
      n2779_q <= next_tx_strb;
  /* ../../../vhdl/atbs_core_floating_window/uart/rtl/uart_tx_ea.vhd:63:17  */
  always @(posedge clock_i or posedge reset_i)
    if (reset_i)
      n2780_q <= 3'b000;
    else
      n2780_q <= next_transmit_counter_value;
  /* ../../../vhdl/atbs_core_floating_window/uart/rtl/uart_tx_ea.vhd:63:17  */
  always @(posedge clock_i or posedge reset_i)
    if (reset_i)
      n2781_q <= 9'b000000000;
    else
      n2781_q <= next_baud_counter_value;
  /* ../../../vhdl/atbs_core_floating_window/uart/rtl/uart_tx_ea.vhd:63:17  */
  always @(posedge clock_i or posedge reset_i)
    if (reset_i)
      n2782_q <= 3'b000;
    else
      n2782_q <= next_tx_state;
  /* ../../../vhdl/atbs_core_floating_window/uart/rtl/uart_tx_ea.vhd:25:17  */
  assign n2783_o = data_i[0]; // extract
  /* ../../../vhdl/atbs_core_floating_window/uart/rtl/uart_tx_ea.vhd:24:5  */
  assign n2784_o = data_i[1]; // extract
  assign n2785_o = data_i[2]; // extract
  assign n2786_o = data_i[3]; // extract
  /* ../../../vhdl/atbs_core_floating_window/uart/rtl/uart_tx_ea.vhd:136:54  */
  assign n2787_o = data_i[4]; // extract
  assign n2788_o = data_i[5]; // extract
  /* ../../../vhdl/atbs_core_floating_window/uart/rtl/uart_tx_ea.vhd:101:9  */
  assign n2789_o = data_i[6]; // extract
  assign n2790_o = data_i[7]; // extract
  /* ../../../vhdl/atbs_core_floating_window/uart/rtl/uart_tx_ea.vhd:136:53  */
  assign n2791_o = transmit_counter_value[1:0]; // extract
  /* ../../../vhdl/atbs_core_floating_window/uart/rtl/uart_tx_ea.vhd:136:53  */
  always @*
    case (n2791_o)
      2'b00: n2792_o = n2783_o;
      2'b01: n2792_o = n2784_o;
      2'b10: n2792_o = n2785_o;
      2'b11: n2792_o = n2786_o;
    endcase
  /* ../../../vhdl/atbs_core_floating_window/uart/rtl/uart_tx_ea.vhd:136:53  */
  assign n2793_o = transmit_counter_value[1:0]; // extract
  /* ../../../vhdl/atbs_core_floating_window/uart/rtl/uart_tx_ea.vhd:136:53  */
  always @*
    case (n2793_o)
      2'b00: n2794_o = n2787_o;
      2'b01: n2794_o = n2788_o;
      2'b10: n2794_o = n2789_o;
      2'b11: n2794_o = n2790_o;
    endcase
  /* ../../../vhdl/atbs_core_floating_window/uart/rtl/uart_tx_ea.vhd:136:53  */
  assign n2795_o = transmit_counter_value[2]; // extract
  /* ../../../vhdl/atbs_core_floating_window/uart/rtl/uart_tx_ea.vhd:136:53  */
  assign n2796_o = n2795_o ? n2794_o : n2792_o;
endmodule

module weyls_discrepancy_8_3_6
  (input  clock_i,
   input  reset_i,
   input  [29:0] spikes_i,
   input  spikes_strb_i,
   output [2:0] weylsd_o,
   output weylsd_strb_o);
  wire [5:0] buf_reg;
  wire [5:0] next_buf_reg;
  wire [1:0] sync_weylsd_strb;
  wire next_weylsd_strb;
  wire [95:0] thermocodes;
  wire [95:0] buf_thermocodes;
  wire [5:0] orresult;
  wire [2:0] neg_orresult;
  wire [95:0] temp_orresult;
  wire [2:0] weylsd;
  wire [2:0] next_weylsd;
  wire [2:0] weylsd_neg;
  wire [2:0] weylsd_pos;
  wire n2468_o;
  wire [1:0] n2470_o;
  wire [5:0] gen_spike_2_tc_n1_spike_2_tc_thermo_o;
  wire [1:0] n2481_o;
  wire [5:0] n2482_o;
  wire [5:0] gen_spike_2_tc_n2_spike_2_tc_thermo_o;
  wire [1:0] n2484_o;
  wire [5:0] n2485_o;
  wire [5:0] gen_spike_2_tc_n3_spike_2_tc_thermo_o;
  wire [1:0] n2487_o;
  wire [5:0] n2488_o;
  wire [5:0] gen_spike_2_tc_n4_spike_2_tc_thermo_o;
  wire [1:0] n2490_o;
  wire [5:0] n2491_o;
  wire [5:0] gen_spike_2_tc_n5_spike_2_tc_thermo_o;
  wire [1:0] n2493_o;
  wire [5:0] n2494_o;
  wire [5:0] gen_spike_2_tc_n6_spike_2_tc_thermo_o;
  wire [1:0] n2496_o;
  wire [5:0] n2497_o;
  wire [5:0] gen_spike_2_tc_n7_spike_2_tc_thermo_o;
  wire [1:0] n2499_o;
  wire [5:0] n2500_o;
  wire [5:0] gen_spike_2_tc_n8_spike_2_tc_thermo_o;
  wire [1:0] n2502_o;
  wire [5:0] n2503_o;
  wire [5:0] gen_spike_2_tc_n9_spike_2_tc_thermo_o;
  wire [1:0] n2505_o;
  wire [5:0] n2506_o;
  wire [5:0] gen_spike_2_tc_n10_spike_2_tc_thermo_o;
  wire [1:0] n2508_o;
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
  assign next_buf_reg = n2527_o; // (signal)
  /* ../../../vhdl/atbs_core_floating_window/adaptive_threshold_control/Weyls-Discrepancy/rtl/weyls_discrepancy_ea.vhd:63:8  */
  assign sync_weylsd_strb = n2672_q; // (signal)
  /* ../../../vhdl/atbs_core_floating_window/adaptive_threshold_control/Weyls-Discrepancy/rtl/weyls_discrepancy_ea.vhd:64:8  */
  assign next_weylsd_strb = spikes_strb_i; // (signal)
  /* ../../../vhdl/atbs_core_floating_window/adaptive_threshold_control/Weyls-Discrepancy/rtl/weyls_discrepancy_ea.vhd:66:8  */
  assign thermocodes = n2673_o; // (signal)
  /* ../../../vhdl/atbs_core_floating_window/adaptive_threshold_control/Weyls-Discrepancy/rtl/weyls_discrepancy_ea.vhd:67:8  */
  assign buf_thermocodes = n2674_o; // (signal)
  /* ../../../vhdl/atbs_core_floating_window/adaptive_threshold_control/Weyls-Discrepancy/rtl/weyls_discrepancy_ea.vhd:69:8  */
  assign orresult = n2658_o; // (signal)
  /* ../../../vhdl/atbs_core_floating_window/adaptive_threshold_control/Weyls-Discrepancy/rtl/weyls_discrepancy_ea.vhd:70:8  */
  assign neg_orresult = n2675_o; // (signal)
  /* ../../../vhdl/atbs_core_floating_window/adaptive_threshold_control/Weyls-Discrepancy/rtl/weyls_discrepancy_ea.vhd:71:8  */
  assign temp_orresult = n2676_o; // (signal)
  /* ../../../vhdl/atbs_core_floating_window/adaptive_threshold_control/Weyls-Discrepancy/rtl/weyls_discrepancy_ea.vhd:73:8  */
  assign weylsd = n2677_q; // (signal)
  /* ../../../vhdl/atbs_core_floating_window/adaptive_threshold_control/Weyls-Discrepancy/rtl/weyls_discrepancy_ea.vhd:74:8  */
  assign next_weylsd = n2669_o; // (signal)
  /* ../../../vhdl/atbs_core_floating_window/adaptive_threshold_control/Weyls-Discrepancy/rtl/weyls_discrepancy_ea.vhd:75:8  */
  assign weylsd_neg = priority_encoder_0_bin_o; // (signal)
  /* ../../../vhdl/atbs_core_floating_window/adaptive_threshold_control/Weyls-Discrepancy/rtl/weyls_discrepancy_ea.vhd:76:8  */
  assign weylsd_pos = priority_encoder_1_bin_o; // (signal)
  /* ../../../vhdl/atbs_core_floating_window/adaptive_threshold_control/Weyls-Discrepancy/rtl/weyls_discrepancy_ea.vhd:97:48  */
  assign n2468_o = sync_weylsd_strb[0]; // extract
  assign n2470_o = {n2468_o, next_weylsd_strb};
  /* ../../../vhdl/atbs_core_floating_window/adaptive_threshold_control/Weyls-Discrepancy/rtl/weyls_discrepancy_ea.vhd:107:5  */
  spike_2_thermocode_6 gen_spike_2_tc_n1_spike_2_tc (
    .spike_i(n2481_o),
    .thermo_i(n2482_o),
    .thermo_o(gen_spike_2_tc_n1_spike_2_tc_thermo_o));
  /* ../../../vhdl/atbs_core_floating_window/adaptive_threshold_control/Weyls-Discrepancy/rtl/weyls_discrepancy_ea.vhd:112:30  */
  assign n2481_o = spikes_i[29:28]; // extract
  /* ../../../vhdl/atbs_core_floating_window/adaptive_threshold_control/Weyls-Discrepancy/rtl/weyls_discrepancy_ea.vhd:113:33  */
  assign n2482_o = thermocodes[5:0]; // extract
  /* ../../../vhdl/atbs_core_floating_window/adaptive_threshold_control/Weyls-Discrepancy/rtl/weyls_discrepancy_ea.vhd:107:5  */
  spike_2_thermocode_6 gen_spike_2_tc_n2_spike_2_tc (
    .spike_i(n2484_o),
    .thermo_i(n2485_o),
    .thermo_o(gen_spike_2_tc_n2_spike_2_tc_thermo_o));
  /* ../../../vhdl/atbs_core_floating_window/adaptive_threshold_control/Weyls-Discrepancy/rtl/weyls_discrepancy_ea.vhd:112:30  */
  assign n2484_o = spikes_i[27:26]; // extract
  /* ../../../vhdl/atbs_core_floating_window/adaptive_threshold_control/Weyls-Discrepancy/rtl/weyls_discrepancy_ea.vhd:113:33  */
  assign n2485_o = thermocodes[11:6]; // extract
  /* ../../../vhdl/atbs_core_floating_window/adaptive_threshold_control/Weyls-Discrepancy/rtl/weyls_discrepancy_ea.vhd:107:5  */
  spike_2_thermocode_6 gen_spike_2_tc_n3_spike_2_tc (
    .spike_i(n2487_o),
    .thermo_i(n2488_o),
    .thermo_o(gen_spike_2_tc_n3_spike_2_tc_thermo_o));
  /* ../../../vhdl/atbs_core_floating_window/adaptive_threshold_control/Weyls-Discrepancy/rtl/weyls_discrepancy_ea.vhd:112:30  */
  assign n2487_o = spikes_i[25:24]; // extract
  /* ../../../vhdl/atbs_core_floating_window/adaptive_threshold_control/Weyls-Discrepancy/rtl/weyls_discrepancy_ea.vhd:113:33  */
  assign n2488_o = thermocodes[17:12]; // extract
  /* ../../../vhdl/atbs_core_floating_window/adaptive_threshold_control/Weyls-Discrepancy/rtl/weyls_discrepancy_ea.vhd:107:5  */
  spike_2_thermocode_6 gen_spike_2_tc_n4_spike_2_tc (
    .spike_i(n2490_o),
    .thermo_i(n2491_o),
    .thermo_o(gen_spike_2_tc_n4_spike_2_tc_thermo_o));
  /* ../../../vhdl/atbs_core_floating_window/adaptive_threshold_control/Weyls-Discrepancy/rtl/weyls_discrepancy_ea.vhd:112:30  */
  assign n2490_o = spikes_i[23:22]; // extract
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
  assign n2524_o = thermocodes[89:84]; // extract
  /* ../../../vhdl/atbs_core_floating_window/adaptive_threshold_control/Weyls-Discrepancy/rtl/weyls_discrepancy_ea.vhd:126:41  */
  assign n2527_o = buf_thermocodes[53:48]; // extract
  assign n2528_o = buf_thermocodes[95:54]; // extract
  assign n2529_o = buf_thermocodes[47:0]; // extract
  /* ../../../vhdl/atbs_core_floating_window/adaptive_threshold_control/Weyls-Discrepancy/rtl/weyls_discrepancy_ea.vhd:136:12  */
  always @*
    eval_orresult_offset_comp = n2660_o; // (isignal)
  initial
    eval_orresult_offset_comp = 96'bX;
  /* ../../../vhdl/atbs_core_floating_window/adaptive_threshold_control/Weyls-Discrepancy/rtl/weyls_discrepancy_ea.vhd:138:71  */
  assign n2533_o = thermocodes[2:0]; // extract
  /* ../../../vhdl/atbs_core_floating_window/adaptive_threshold_control/Weyls-Discrepancy/rtl/weyls_discrepancy_ea.vhd:138:53  */
  assign n2534_o = ~n2533_o;
  /* ../../../vhdl/atbs_core_floating_window/adaptive_threshold_control/Weyls-Discrepancy/rtl/weyls_discrepancy_ea.vhd:139:77  */
  assign n2535_o = thermocodes[5:3]; // extract
  assign n2536_o = eval_orresult_offset_comp[95:6]; // extract
  assign n2537_o = {n2536_o, n2535_o, n2534_o};
  /* ../../../vhdl/atbs_core_floating_window/adaptive_threshold_control/Weyls-Discrepancy/rtl/weyls_discrepancy_ea.vhd:140:36  */
  assign n2538_o = n2537_o[5:0]; // extract
  /* ../../../vhdl/atbs_core_floating_window/adaptive_threshold_control/Weyls-Discrepancy/rtl/weyls_discrepancy_ea.vhd:146:73  */
  assign n2539_o = thermocodes[8:6]; // extract
  /* ../../../vhdl/atbs_core_floating_window/adaptive_threshold_control/Weyls-Discrepancy/rtl/weyls_discrepancy_ea.vhd:146:55  */
  assign n2540_o = ~n2539_o;
  /* ../../../vhdl/atbs_core_floating_window/adaptive_threshold_control/Weyls-Discrepancy/rtl/weyls_discrepancy_ea.vhd:147:79  */
  assign n2541_o = thermocodes[11:9]; // extract
  /* ../../../vhdl/atbs_core_floating_window/adaptive_threshold_control/Weyls-Discrepancy/rtl/weyls_discrepancy_ea.vhd:148:40  */
  assign n2542_o = temp_orresult[5:0]; // extract
  assign n2543_o = eval_orresult_offset_comp[95:12]; // extract
  assign n2544_o = {n2543_o, n2541_o, n2540_o, n2535_o, n2534_o};
  /* ../../../vhdl/atbs_core_floating_window/adaptive_threshold_control/Weyls-Discrepancy/rtl/weyls_discrepancy_ea.vhd:148:60  */
  assign n2545_o = n2544_o[11:6]; // extract
  /* ../../../vhdl/atbs_core_floating_window/adaptive_threshold_control/Weyls-Discrepancy/rtl/weyls_discrepancy_ea.vhd:148:46  */
  assign n2546_o = n2542_o | n2545_o;
  /* ../../../vhdl/atbs_core_floating_window/adaptive_threshold_control/Weyls-Discrepancy/rtl/weyls_discrepancy_ea.vhd:146:73  */
  assign n2547_o = thermocodes[14:12]; // extract
  /* ../../../vhdl/atbs_core_floating_window/adaptive_threshold_control/Weyls-Discrepancy/rtl/weyls_discrepancy_ea.vhd:146:55  */
  assign n2548_o = ~n2547_o;
  /* ../../../vhdl/atbs_core_floating_window/adaptive_threshold_control/Weyls-Discrepancy/rtl/weyls_discrepancy_ea.vhd:147:79  */
  assign n2549_o = thermocodes[17:15]; // extract
  /* ../../../vhdl/atbs_core_floating_window/adaptive_threshold_control/Weyls-Discrepancy/rtl/weyls_discrepancy_ea.vhd:148:40  */
  assign n2550_o = temp_orresult[11:6]; // extract
  assign n2551_o = eval_orresult_offset_comp[95:18]; // extract
  assign n2552_o = {n2551_o, n2549_o, n2548_o, n2541_o, n2540_o, n2535_o, n2534_o};
  /* ../../../vhdl/atbs_core_floating_window/adaptive_threshold_control/Weyls-Discrepancy/rtl/weyls_discrepancy_ea.vhd:148:60  */
  assign n2553_o = n2552_o[17:12]; // extract
  /* ../../../vhdl/atbs_core_floating_window/adaptive_threshold_control/Weyls-Discrepancy/rtl/weyls_discrepancy_ea.vhd:148:46  */
  assign n2554_o = n2550_o | n2553_o;
  /* ../../../vhdl/atbs_core_floating_window/adaptive_threshold_control/Weyls-Discrepancy/rtl/weyls_discrepancy_ea.vhd:146:73  */
  assign n2555_o = thermocodes[20:18]; // extract
  /* ../../../vhdl/atbs_core_floating_window/adaptive_threshold_control/Weyls-Discrepancy/rtl/weyls_discrepancy_ea.vhd:146:55  */
  assign n2556_o = ~n2555_o;
  /* ../../../vhdl/atbs_core_floating_window/adaptive_threshold_control/Weyls-Discrepancy/rtl/weyls_discrepancy_ea.vhd:147:79  */
  assign n2557_o = thermocodes[23:21]; // extract
  /* ../../../vhdl/atbs_core_floating_window/adaptive_threshold_control/Weyls-Discrepancy/rtl/weyls_discrepancy_ea.vhd:148:40  */
  assign n2558_o = temp_orresult[17:12]; // extract
  assign n2559_o = eval_orresult_offset_comp[95:24]; // extract
  assign n2560_o = {n2559_o, n2557_o, n2556_o, n2549_o, n2548_o, n2541_o, n2540_o, n2535_o, n2534_o};
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
  assign n2605_o = thermocodes[59:57]; // extract
  /* ../../../vhdl/atbs_core_floating_window/adaptive_threshold_control/Weyls-Discrepancy/rtl/weyls_discrepancy_ea.vhd:148:40  */
  assign n2606_o = temp_orresult[53:48]; // extract
  assign n2607_o = eval_orresult_offset_comp[95:60]; // extract
  assign n2608_o = {n2607_o, n2605_o, n2604_o, n2597_o, n2596_o, n2589_o, n2588_o, n2581_o, n2580_o, n2573_o, n2572_o, n2565_o, n2564_o, n2557_o, n2556_o, n2549_o, n2548_o, n2541_o, n2540_o, n2535_o, n2534_o};
  /* ../../../vhdl/atbs_core_floating_window/adaptive_threshold_control/Weyls-Discrepancy/rtl/weyls_discrepancy_ea.vhd:148:60  */
  assign n2609_o = n2608_o[59:54]; // extract
  /* ../../../vhdl/atbs_core_floating_window/adaptive_threshold_control/Weyls-Discrepancy/rtl/weyls_discrepancy_ea.vhd:148:46  */
  assign n2610_o = n2606_o | n2609_o;
  /* ../../../vhdl/atbs_core_floating_window/adaptive_threshold_control/Weyls-Discrepancy/rtl/weyls_discrepancy_ea.vhd:146:73  */
  assign n2611_o = thermocodes[62:60]; // extract
  /* ../../../vhdl/atbs_core_floating_window/adaptive_threshold_control/Weyls-Discrepancy/rtl/weyls_discrepancy_ea.vhd:146:55  */
  assign n2612_o = ~n2611_o;
  /* ../../../vhdl/atbs_core_floating_window/adaptive_threshold_control/Weyls-Discrepancy/rtl/weyls_discrepancy_ea.vhd:147:79  */
  assign n2613_o = thermocodes[65:63]; // extract
  /* ../../../vhdl/atbs_core_floating_window/adaptive_threshold_control/Weyls-Discrepancy/rtl/weyls_discrepancy_ea.vhd:148:40  */
  assign n2614_o = temp_orresult[59:54]; // extract
  assign n2615_o = eval_orresult_offset_comp[95:66]; // extract
  assign n2616_o = {n2615_o, n2613_o, n2612_o, n2605_o, n2604_o, n2597_o, n2596_o, n2589_o, n2588_o, n2581_o, n2580_o, n2573_o, n2572_o, n2565_o, n2564_o, n2557_o, n2556_o, n2549_o, n2548_o, n2541_o, n2540_o, n2535_o, n2534_o};
  /* ../../../vhdl/atbs_core_floating_window/adaptive_threshold_control/Weyls-Discrepancy/rtl/weyls_discrepancy_ea.vhd:148:60  */
  assign n2617_o = n2616_o[65:60]; // extract
  /* ../../../vhdl/atbs_core_floating_window/adaptive_threshold_control/Weyls-Discrepancy/rtl/weyls_discrepancy_ea.vhd:148:46  */
  assign n2618_o = n2614_o | n2617_o;
  /* ../../../vhdl/atbs_core_floating_window/adaptive_threshold_control/Weyls-Discrepancy/rtl/weyls_discrepancy_ea.vhd:146:73  */
  assign n2619_o = thermocodes[68:66]; // extract
  /* ../../../vhdl/atbs_core_floating_window/adaptive_threshold_control/Weyls-Discrepancy/rtl/weyls_discrepancy_ea.vhd:146:55  */
  assign n2620_o = ~n2619_o;
  /* ../../../vhdl/atbs_core_floating_window/adaptive_threshold_control/Weyls-Discrepancy/rtl/weyls_discrepancy_ea.vhd:147:79  */
  assign n2621_o = thermocodes[71:69]; // extract
  /* ../../../vhdl/atbs_core_floating_window/adaptive_threshold_control/Weyls-Discrepancy/rtl/weyls_discrepancy_ea.vhd:148:40  */
  assign n2622_o = temp_orresult[65:60]; // extract
  assign n2623_o = eval_orresult_offset_comp[95:72]; // extract
  assign n2624_o = {n2623_o, n2621_o, n2620_o, n2613_o, n2612_o, n2605_o, n2604_o, n2597_o, n2596_o, n2589_o, n2588_o, n2581_o, n2580_o, n2573_o, n2572_o, n2565_o, n2564_o, n2557_o, n2556_o, n2549_o, n2548_o, n2541_o, n2540_o, n2535_o, n2534_o};
  /* ../../../vhdl/atbs_core_floating_window/adaptive_threshold_control/Weyls-Discrepancy/rtl/weyls_discrepancy_ea.vhd:148:60  */
  assign n2625_o = n2624_o[71:66]; // extract
  /* ../../../vhdl/atbs_core_floating_window/adaptive_threshold_control/Weyls-Discrepancy/rtl/weyls_discrepancy_ea.vhd:148:46  */
  assign n2626_o = n2622_o | n2625_o;
  /* ../../../vhdl/atbs_core_floating_window/adaptive_threshold_control/Weyls-Discrepancy/rtl/weyls_discrepancy_ea.vhd:146:73  */
  assign n2627_o = thermocodes[74:72]; // extract
  /* ../../../vhdl/atbs_core_floating_window/adaptive_threshold_control/Weyls-Discrepancy/rtl/weyls_discrepancy_ea.vhd:146:55  */
  assign n2628_o = ~n2627_o;
  /* ../../../vhdl/atbs_core_floating_window/adaptive_threshold_control/Weyls-Discrepancy/rtl/weyls_discrepancy_ea.vhd:147:79  */
  assign n2629_o = thermocodes[77:75]; // extract
  /* ../../../vhdl/atbs_core_floating_window/adaptive_threshold_control/Weyls-Discrepancy/rtl/weyls_discrepancy_ea.vhd:148:40  */
  assign n2630_o = temp_orresult[71:66]; // extract
  assign n2631_o = eval_orresult_offset_comp[95:78]; // extract
  assign n2632_o = {n2631_o, n2629_o, n2628_o, n2621_o, n2620_o, n2613_o, n2612_o, n2605_o, n2604_o, n2597_o, n2596_o, n2589_o, n2588_o, n2581_o, n2580_o, n2573_o, n2572_o, n2565_o, n2564_o, n2557_o, n2556_o, n2549_o, n2548_o, n2541_o, n2540_o, n2535_o, n2534_o};
  /* ../../../vhdl/atbs_core_floating_window/adaptive_threshold_control/Weyls-Discrepancy/rtl/weyls_discrepancy_ea.vhd:148:60  */
  assign n2633_o = n2632_o[77:72]; // extract
  /* ../../../vhdl/atbs_core_floating_window/adaptive_threshold_control/Weyls-Discrepancy/rtl/weyls_discrepancy_ea.vhd:148:46  */
  assign n2634_o = n2630_o | n2633_o;
  /* ../../../vhdl/atbs_core_floating_window/adaptive_threshold_control/Weyls-Discrepancy/rtl/weyls_discrepancy_ea.vhd:146:73  */
  assign n2635_o = thermocodes[80:78]; // extract
  /* ../../../vhdl/atbs_core_floating_window/adaptive_threshold_control/Weyls-Discrepancy/rtl/weyls_discrepancy_ea.vhd:146:55  */
  assign n2636_o = ~n2635_o;
  /* ../../../vhdl/atbs_core_floating_window/adaptive_threshold_control/Weyls-Discrepancy/rtl/weyls_discrepancy_ea.vhd:147:79  */
  assign n2637_o = thermocodes[83:81]; // extract
  /* ../../../vhdl/atbs_core_floating_window/adaptive_threshold_control/Weyls-Discrepancy/rtl/weyls_discrepancy_ea.vhd:148:40  */
  assign n2638_o = temp_orresult[77:72]; // extract
  assign n2639_o = eval_orresult_offset_comp[95:84]; // extract
  assign n2640_o = {n2639_o, n2637_o, n2636_o, n2629_o, n2628_o, n2621_o, n2620_o, n2613_o, n2612_o, n2605_o, n2604_o, n2597_o, n2596_o, n2589_o, n2588_o, n2581_o, n2580_o, n2573_o, n2572_o, n2565_o, n2564_o, n2557_o, n2556_o, n2549_o, n2548_o, n2541_o, n2540_o, n2535_o, n2534_o};
  /* ../../../vhdl/atbs_core_floating_window/adaptive_threshold_control/Weyls-Discrepancy/rtl/weyls_discrepancy_ea.vhd:148:60  */
  assign n2641_o = n2640_o[83:78]; // extract
  /* ../../../vhdl/atbs_core_floating_window/adaptive_threshold_control/Weyls-Discrepancy/rtl/weyls_discrepancy_ea.vhd:148:46  */
  assign n2642_o = n2638_o | n2641_o;
  /* ../../../vhdl/atbs_core_floating_window/adaptive_threshold_control/Weyls-Discrepancy/rtl/weyls_discrepancy_ea.vhd:146:73  */
  assign n2643_o = thermocodes[86:84]; // extract
  /* ../../../vhdl/atbs_core_floating_window/adaptive_threshold_control/Weyls-Discrepancy/rtl/weyls_discrepancy_ea.vhd:146:55  */
  assign n2644_o = ~n2643_o;
  /* ../../../vhdl/atbs_core_floating_window/adaptive_threshold_control/Weyls-Discrepancy/rtl/weyls_discrepancy_ea.vhd:147:79  */
  assign n2645_o = thermocodes[89:87]; // extract
  /* ../../../vhdl/atbs_core_floating_window/adaptive_threshold_control/Weyls-Discrepancy/rtl/weyls_discrepancy_ea.vhd:148:40  */
  assign n2646_o = temp_orresult[83:78]; // extract
  assign n2647_o = eval_orresult_offset_comp[95:90]; // extract
  assign n2648_o = {n2647_o, n2645_o, n2644_o, n2637_o, n2636_o, n2629_o, n2628_o, n2621_o, n2620_o, n2613_o, n2612_o, n2605_o, n2604_o, n2597_o, n2596_o, n2589_o, n2588_o, n2581_o, n2580_o, n2573_o, n2572_o, n2565_o, n2564_o, n2557_o, n2556_o, n2549_o, n2548_o, n2541_o, n2540_o, n2535_o, n2534_o};
  /* ../../../vhdl/atbs_core_floating_window/adaptive_threshold_control/Weyls-Discrepancy/rtl/weyls_discrepancy_ea.vhd:148:60  */
  assign n2649_o = n2648_o[89:84]; // extract
  /* ../../../vhdl/atbs_core_floating_window/adaptive_threshold_control/Weyls-Discrepancy/rtl/weyls_discrepancy_ea.vhd:148:46  */
  assign n2650_o = n2646_o | n2649_o;
  /* ../../../vhdl/atbs_core_floating_window/adaptive_threshold_control/Weyls-Discrepancy/rtl/weyls_discrepancy_ea.vhd:146:73  */
  assign n2651_o = thermocodes[92:90]; // extract
  /* ../../../vhdl/atbs_core_floating_window/adaptive_threshold_control/Weyls-Discrepancy/rtl/weyls_discrepancy_ea.vhd:146:55  */
  assign n2652_o = ~n2651_o;
  /* ../../../vhdl/atbs_core_floating_window/adaptive_threshold_control/Weyls-Discrepancy/rtl/weyls_discrepancy_ea.vhd:147:79  */
  assign n2653_o = thermocodes[95:93]; // extract
  /* ../../../vhdl/atbs_core_floating_window/adaptive_threshold_control/Weyls-Discrepancy/rtl/weyls_discrepancy_ea.vhd:148:40  */
  assign n2654_o = temp_orresult[89:84]; // extract
  assign n2655_o = {n2653_o, n2652_o, n2645_o, n2644_o, n2637_o, n2636_o, n2629_o, n2628_o, n2621_o, n2620_o, n2613_o, n2612_o, n2605_o, n2604_o, n2597_o, n2596_o, n2589_o, n2588_o, n2581_o, n2580_o, n2573_o, n2572_o, n2565_o, n2564_o, n2557_o, n2556_o, n2549_o, n2548_o, n2541_o, n2540_o, n2535_o, n2534_o};
  /* ../../../vhdl/atbs_core_floating_window/adaptive_threshold_control/Weyls-Discrepancy/rtl/weyls_discrepancy_ea.vhd:148:60  */
  assign n2656_o = n2655_o[95:90]; // extract
  /* ../../../vhdl/atbs_core_floating_window/adaptive_threshold_control/Weyls-Discrepancy/rtl/weyls_discrepancy_ea.vhd:148:46  */
  assign n2657_o = n2654_o | n2656_o;
  /* ../../../vhdl/atbs_core_floating_window/adaptive_threshold_control/Weyls-Discrepancy/rtl/weyls_discrepancy_ea.vhd:151:30  */
  assign n2658_o = temp_orresult[95:90]; // extract
  assign n2660_o = {n2653_o, n2652_o, n2645_o, n2644_o, n2637_o, n2636_o, n2629_o, n2628_o, n2621_o, n2620_o, n2613_o, n2612_o, n2605_o, n2604_o, n2597_o, n2596_o, n2589_o, n2588_o, n2581_o, n2580_o, n2573_o, n2572_o, n2565_o, n2564_o, n2557_o, n2556_o, n2549_o, n2548_o, n2541_o, n2540_o, n2535_o, n2534_o};
  /* ../../../vhdl/atbs_core_floating_window/adaptive_threshold_control/Weyls-Discrepancy/rtl/weyls_discrepancy_ea.vhd:160:54  */
  assign n2662_o = orresult[0]; // extract
  /* ../../../vhdl/atbs_core_floating_window/adaptive_threshold_control/Weyls-Discrepancy/rtl/weyls_discrepancy_ea.vhd:160:54  */
  assign n2663_o = orresult[1]; // extract
  /* ../../../vhdl/atbs_core_floating_window/adaptive_threshold_control/Weyls-Discrepancy/rtl/weyls_discrepancy_ea.vhd:160:54  */
  assign n2664_o = orresult[2]; // extract
  /* ../../../vhdl/atbs_core_floating_window/adaptive_threshold_control/Weyls-Discrepancy/rtl/weyls_discrepancy_ea.vhd:164:3  */
  priority_encoder_3_3 priority_encoder_0 (
    .clock_i(clock_i),
    .reset_i(reset_i),
    .code_i(neg_orresult),
    .bin_o(priority_encoder_0_bin_o));
  /* ../../../vhdl/atbs_core_floating_window/adaptive_threshold_control/Weyls-Discrepancy/rtl/weyls_discrepancy_ea.vhd:179:3  */
  priority_encoder_3_3 priority_encoder_1 (
    .clock_i(clock_i),
    .reset_i(reset_i),
    .code_i(n2667_o),
    .bin_o(priority_encoder_1_bin_o));
  /* ../../../vhdl/atbs_core_floating_window/adaptive_threshold_control/Weyls-Discrepancy/rtl/weyls_discrepancy_ea.vhd:187:24  */
  assign n2667_o = orresult[5:3]; // extract
  /* ../../../vhdl/atbs_core_floating_window/adaptive_threshold_control/Weyls-Discrepancy/rtl/weyls_discrepancy_ea.vhd:194:36  */
  assign n2669_o = weylsd_neg + weylsd_pos;
  /* ../../../vhdl/atbs_core_floating_window/adaptive_threshold_control/Weyls-Discrepancy/rtl/weyls_discrepancy_ea.vhd:199:36  */
  assign n2670_o = sync_weylsd_strb[1]; // extract
  /* ../../../vhdl/atbs_core_floating_window/adaptive_threshold_control/Weyls-Discrepancy/rtl/weyls_discrepancy_ea.vhd:91:5  */
  always @(posedge clock_i or posedge reset_i)
    if (reset_i)
      n2671_q <= 6'b000000;
    else
      n2671_q <= next_buf_reg;
  /* ../../../vhdl/atbs_core_floating_window/adaptive_threshold_control/Weyls-Discrepancy/rtl/weyls_discrepancy_ea.vhd:91:5  */
  always @(posedge clock_i or posedge reset_i)
    if (reset_i)
      n2672_q <= 2'b00;
    else
      n2672_q <= n2470_o;
  /* ../../../vhdl/atbs_core_floating_window/adaptive_threshold_control/Weyls-Discrepancy/rtl/weyls_discrepancy_ea.vhd:87:5  */
  assign n2673_o = {n2528_o, buf_reg, n2529_o};
  /* ../../../vhdl/atbs_core_floating_window/adaptive_threshold_control/Weyls-Discrepancy/rtl/weyls_discrepancy_ea.vhd:87:5  */
  assign n2674_o = {gen_spike_2_tc_n15_spike_2_tc_thermo_o, gen_spike_2_tc_n14_spike_2_tc_thermo_o, gen_spike_2_tc_n13_spike_2_tc_thermo_o, gen_spike_2_tc_n12_spike_2_tc_thermo_o, gen_spike_2_tc_n11_spike_2_tc_thermo_o, gen_spike_2_tc_n10_spike_2_tc_thermo_o, gen_spike_2_tc_n9_spike_2_tc_thermo_o, gen_spike_2_tc_n8_spike_2_tc_thermo_o, gen_spike_2_tc_n7_spike_2_tc_thermo_o, gen_spike_2_tc_n6_spike_2_tc_thermo_o, gen_spike_2_tc_n5_spike_2_tc_thermo_o, gen_spike_2_tc_n4_spike_2_tc_thermo_o, gen_spike_2_tc_n3_spike_2_tc_thermo_o, gen_spike_2_tc_n2_spike_2_tc_thermo_o, gen_spike_2_tc_n1_spike_2_tc_thermo_o, 6'b000111};
  assign n2675_o = {n2662_o, n2663_o, n2664_o};
  assign n2676_o = {n2657_o, n2650_o, n2642_o, n2634_o, n2626_o, n2618_o, n2610_o, n2602_o, n2594_o, n2586_o, n2578_o, n2570_o, n2562_o, n2554_o, n2546_o, n2538_o};
  /* ../../../vhdl/atbs_core_floating_window/adaptive_threshold_control/Weyls-Discrepancy/rtl/weyls_discrepancy_ea.vhd:91:5  */
  always @(posedge clock_i or posedge reset_i)
    if (reset_i)
      n2677_q <= 3'b000;
    else
      n2677_q <= next_weylsd;
endmodule
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
